wyolum/KlokTHREEjr/images/IMG_20180121_123737154.jpg

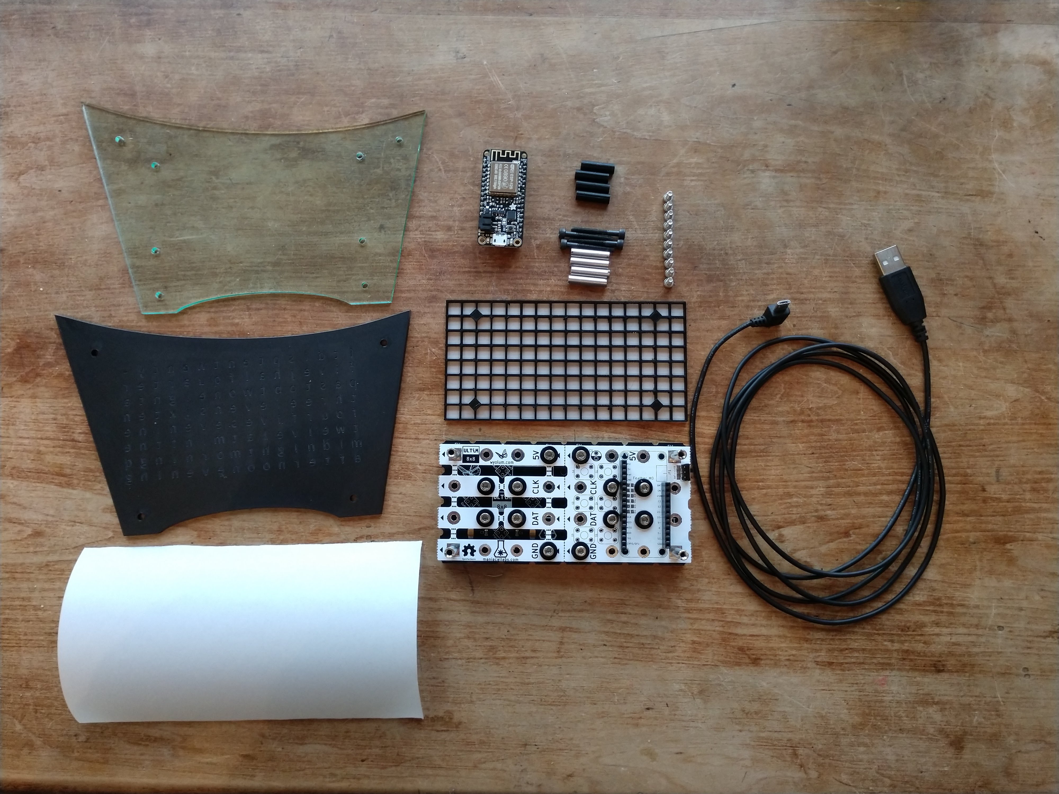
images/IMG_20180121_123737154.jpg
