wyolum/KlokTHREEjr/images/IMG_20180121_124737628.jpg

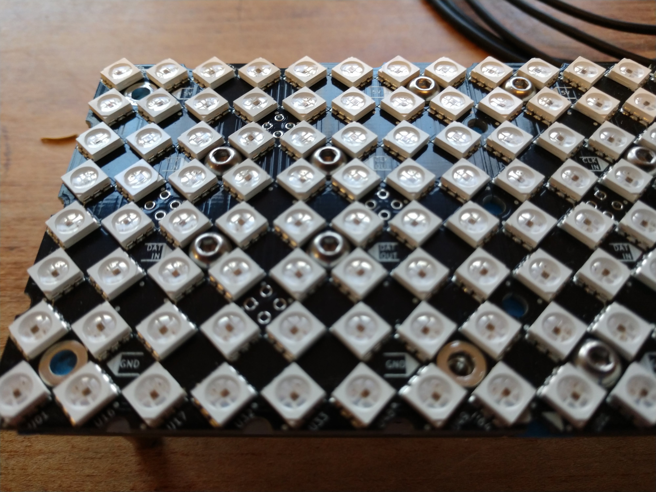
images/IMG_20180121_124737628.jpg
