wyolum/KlokTHREEjr/images/IMG_20180121_130417669.jpg

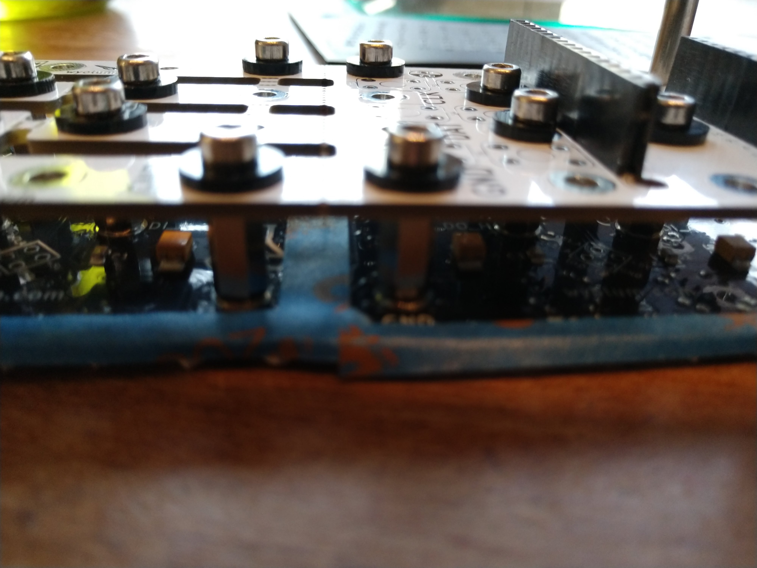
images/IMG_20180121_130417669.jpg
