wyolum/KlokTHREEjr/images/IMG_20180121_130429405.jpg

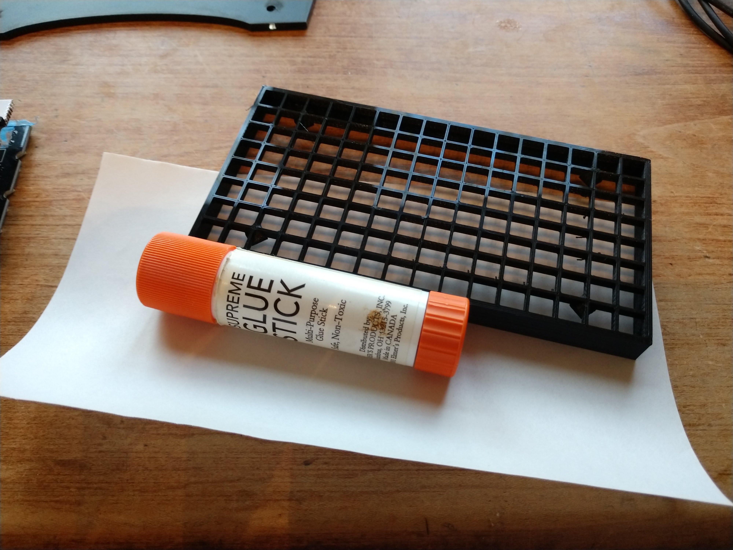
images/IMG_20180121_130429405.jpg
