wyolum/KlokTHREEjr/images/IMG_20180121_130903656.jpg

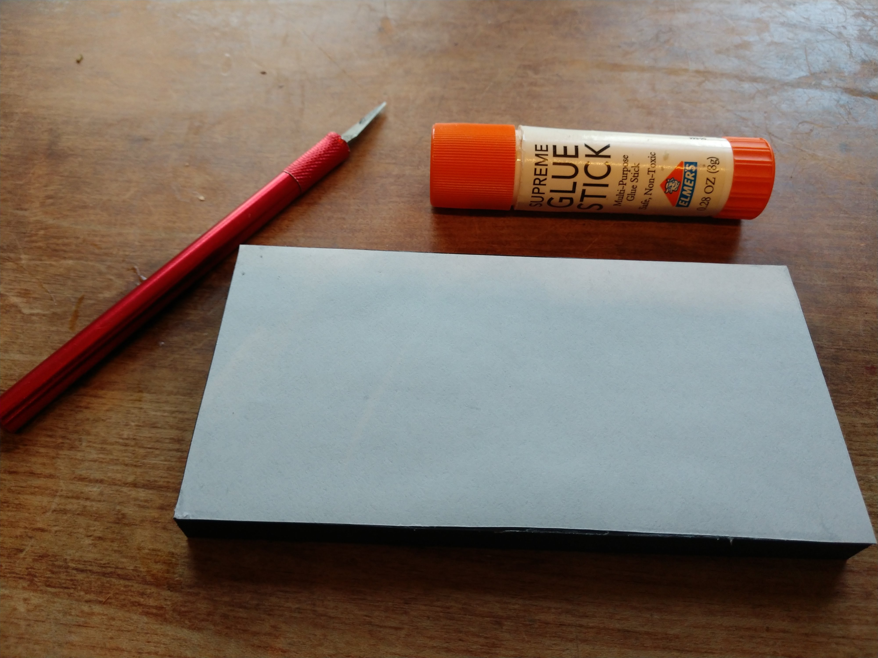
images/IMG_20180121_130903656.jpg
