wyolum/KlokTHREEjr/images/IMG_20180121_130914929.jpg

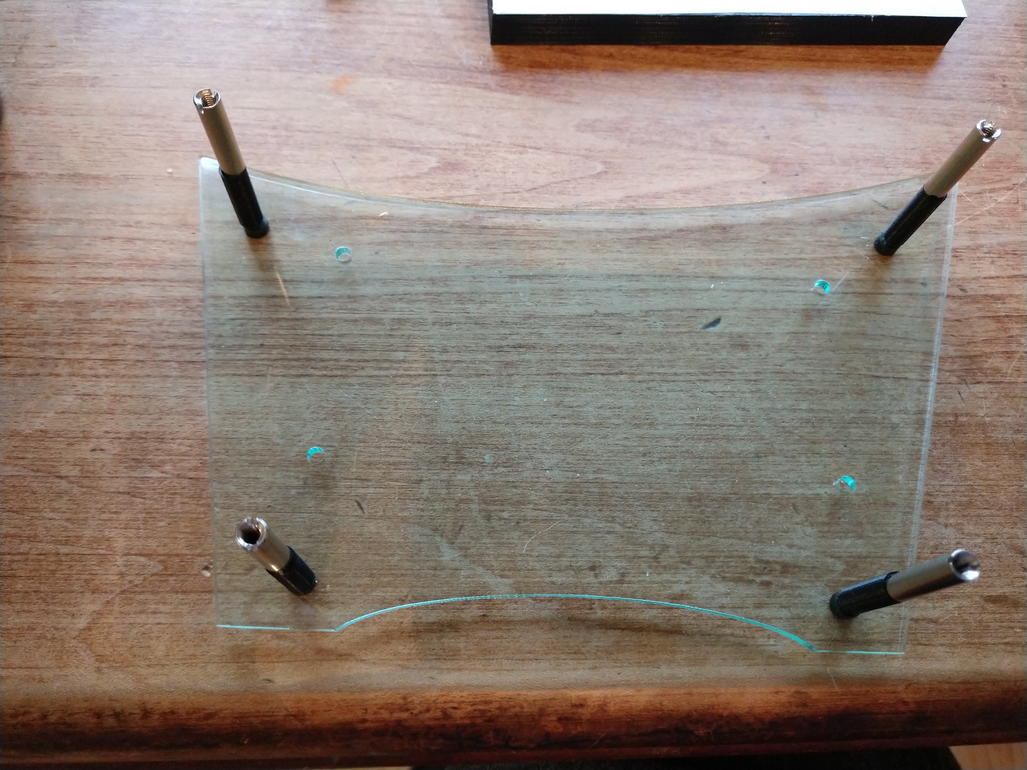
images/IMG_20180121_130914929.jpg
