wyolum/KlokTHREEjr/images/IMG_20180121_131034821.jpg

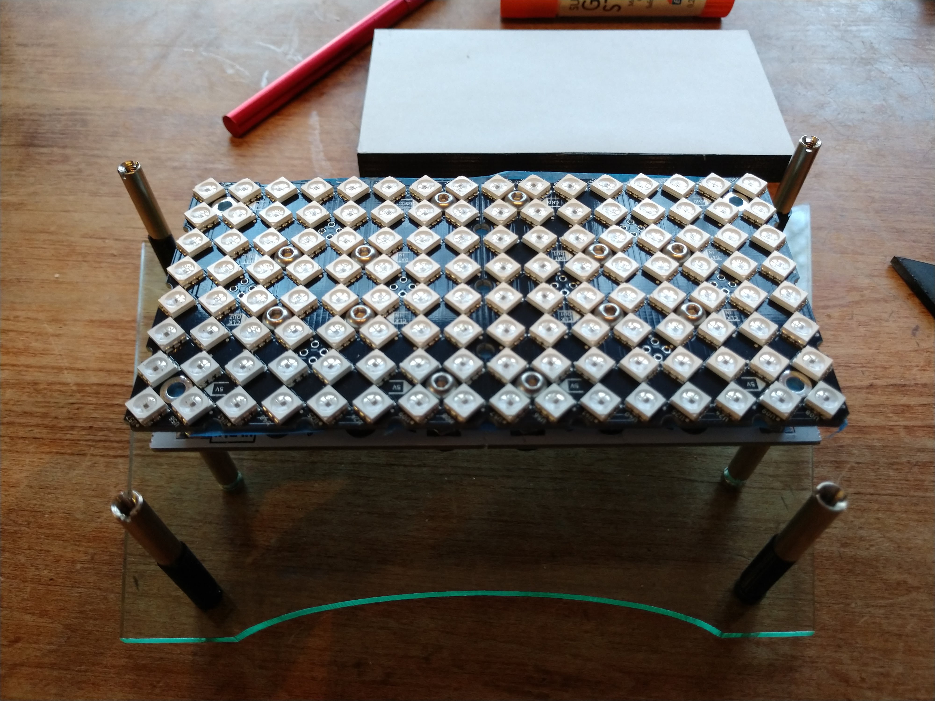
images/IMG_20180121_131034821.jpg
