wyolum/KlokTHREEjr/images/IMG_20180121_131046575.jpg

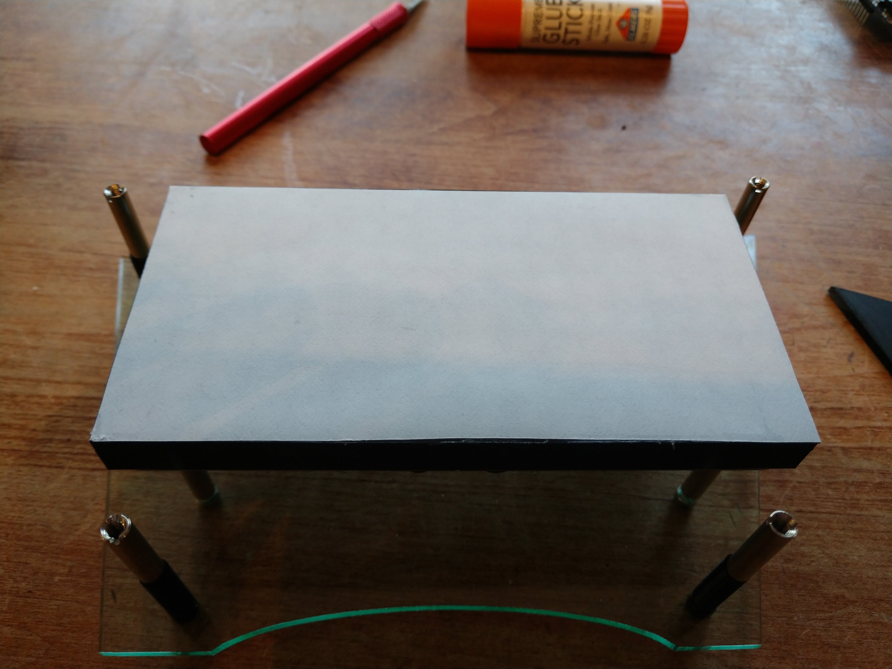
images/IMG_20180121_131046575.jpg
