wyolum/KlokTHREEjr/images/IMG_20180121_131612478.jpg

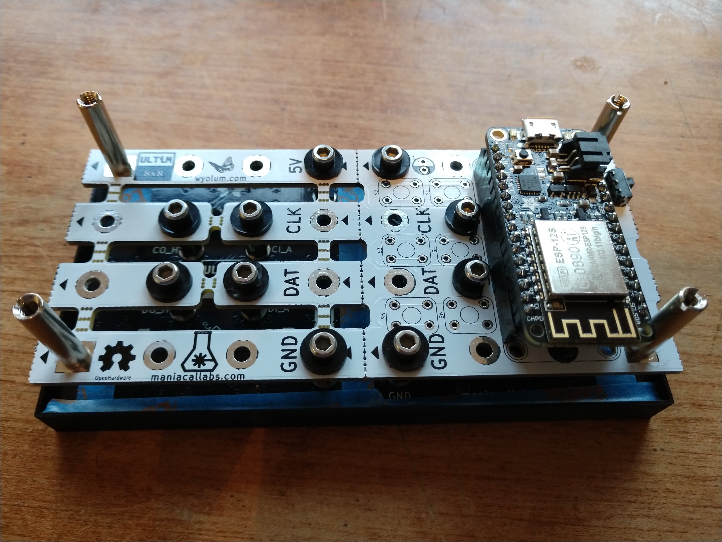
images/IMG_20180121_131612478.jpg
