wyolum/KlokTHREEjr/images/IMG_20180121_131839371.jpg

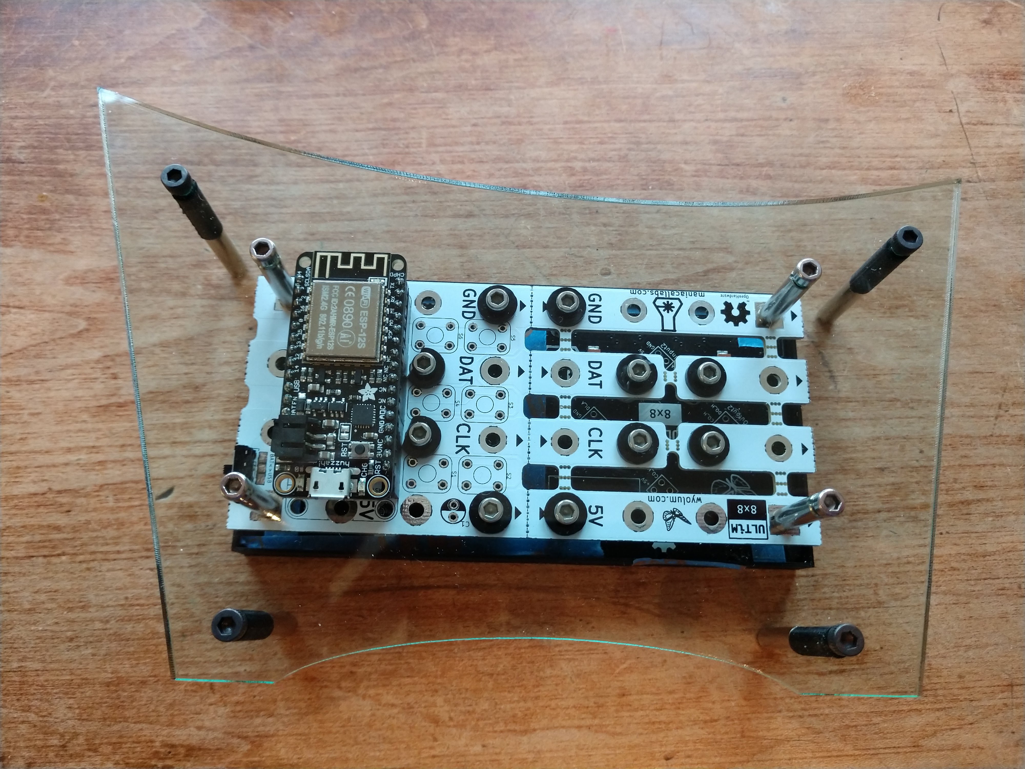
images/IMG_20180121_131839371.jpg
