wyolum/KlokTHREEjr/images/IMG_20180121_131950804.jpg

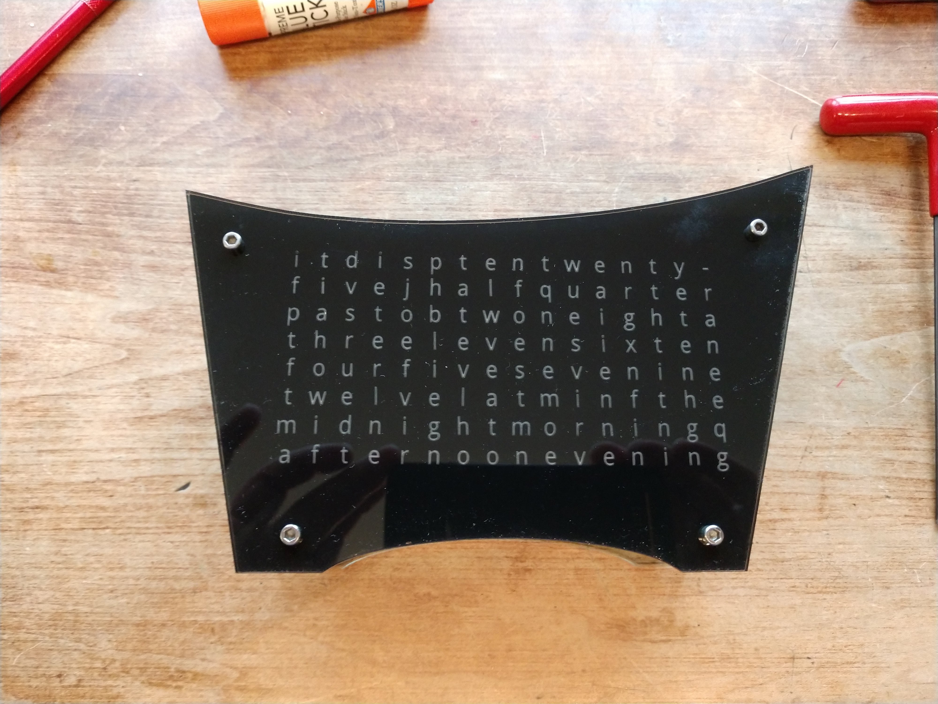
images/IMG_20180121_131950804.jpg
