wyolum/KlokTHREEjr/k3jr_controller_kicad_v2/3d_render/k3jr_controller_01.png

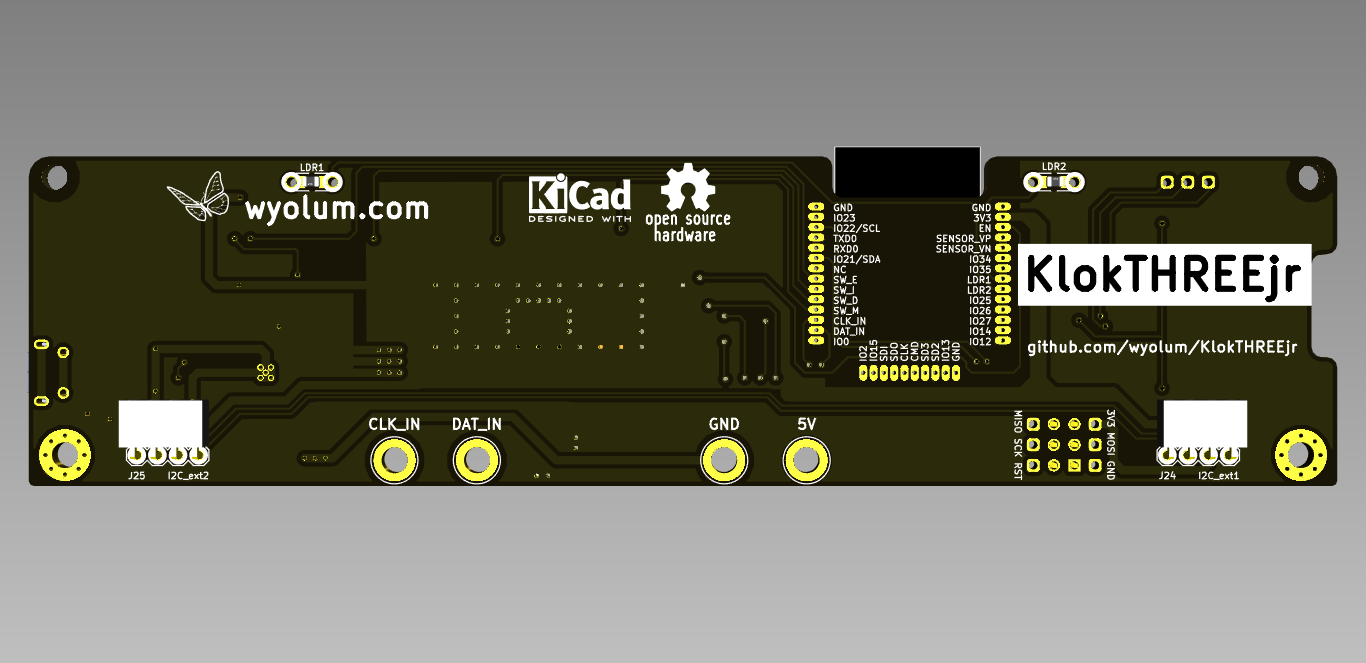
k3jr_controller_kicad_v2/3d_render/k3jr_controller_01.png
