wyolum/KlokTHREEjr/k3jr_controller_kicad_v2/3d_render/k3jr_controller_03.png

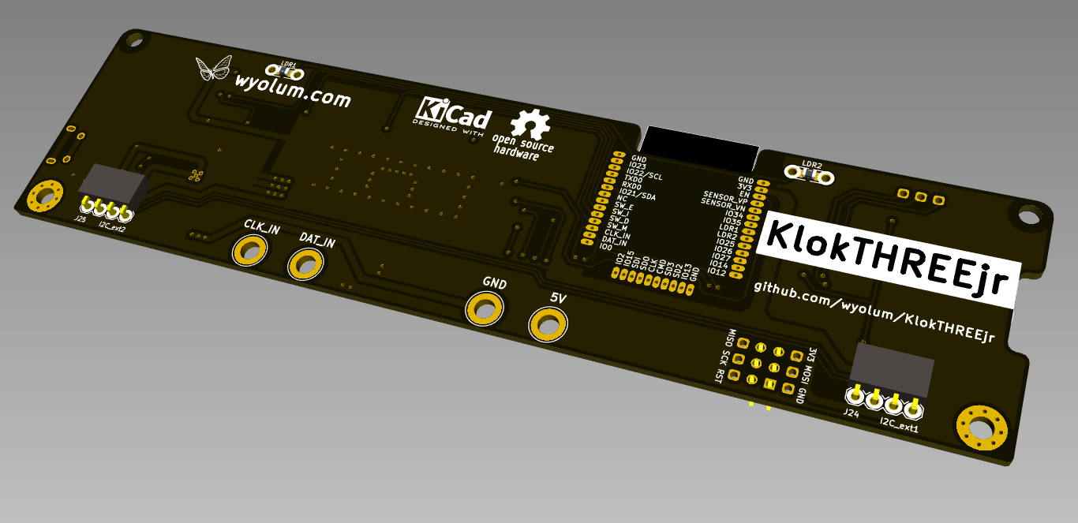
k3jr_controller_kicad_v2/3d_render/k3jr_controller_03.png
