wyolum/KlokTHREEjr/kicad/3d_render/KlokTHREEjr03.png

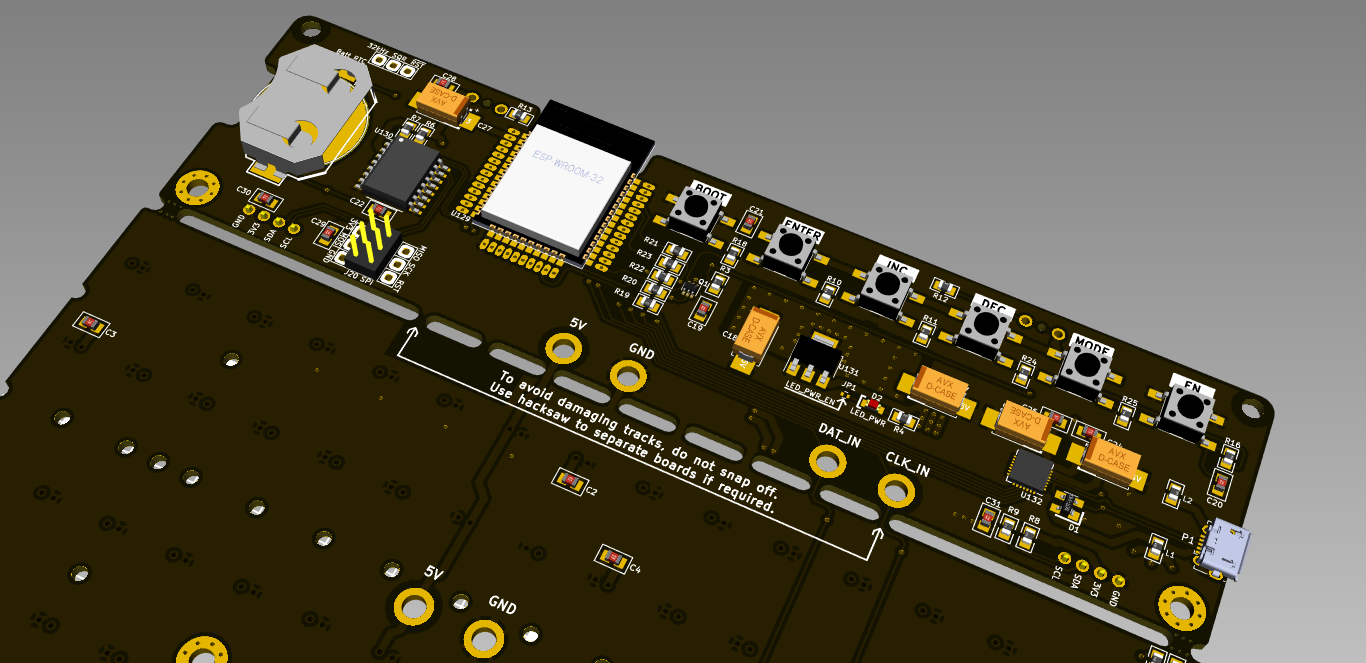
kicad/3d_render/KlokTHREEjr03.png
