wyolum/KlokTHREEjr/kicad/3d_render/KlokTHREEjr04.png

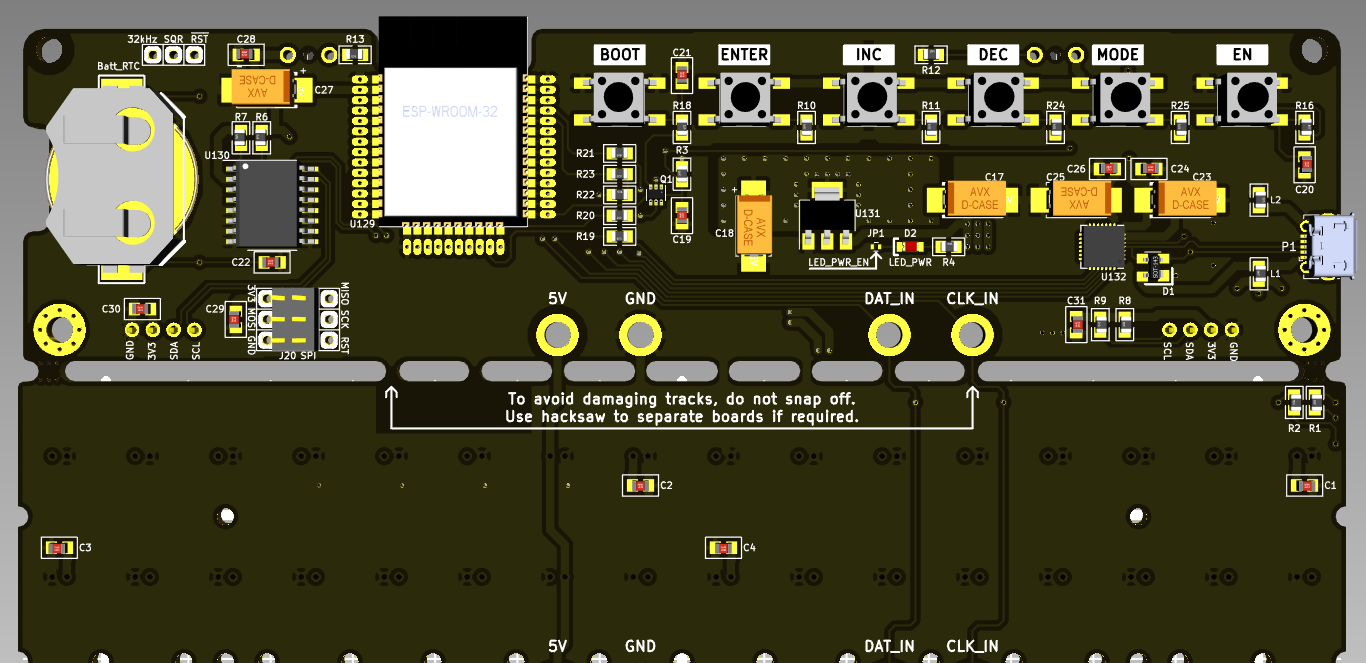
kicad/3d_render/KlokTHREEjr04.png
