wyolum/KlokTHREEjr/kicad/3d_render/KlokTHREEjr05.png

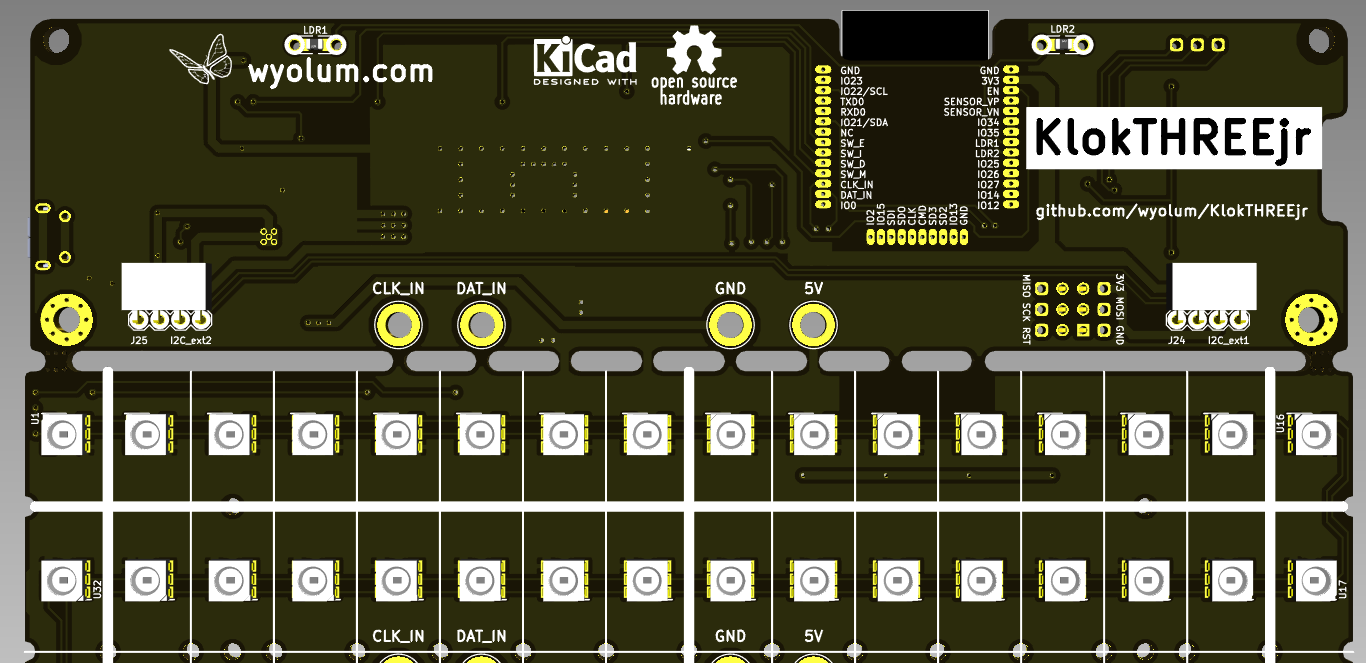
kicad/3d_render/KlokTHREEjr05.png
