wyolum/KlokTHREEjr/kicad/3d_render/KlokTHREEjr06.png

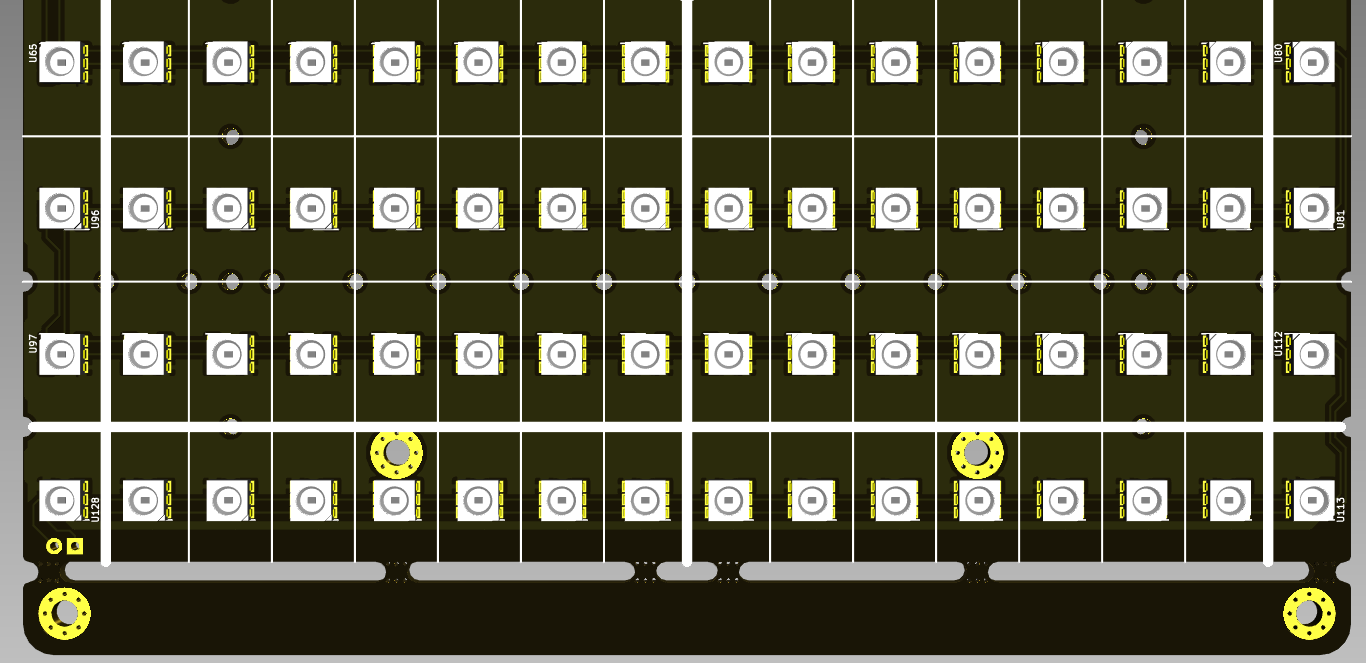
kicad/3d_render/KlokTHREEjr06.png
