wyolum/KlokTHREEjr/k3jr_controller_kicad_v2/3d_modules/QFN28-0_5.step

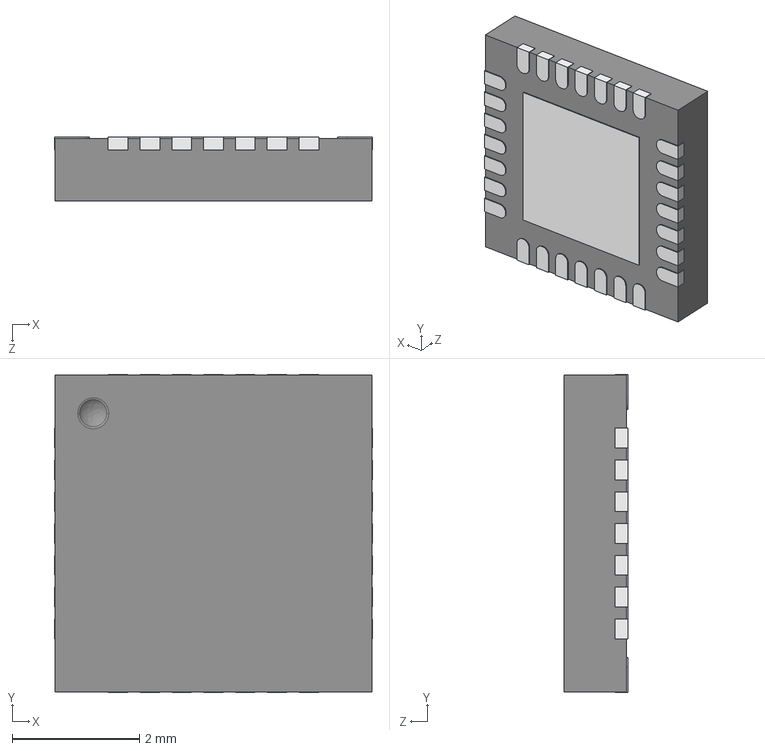
[picture p38: CAD file, 2017-12-30]
k3jr_controller_kicad_v2/3d_modules/QFN28-0_5.step
5.00 x 5.00 x 1.00 mm
User Library-QFN28-0_5_Fusion
User Library-QFN28-0_5_Fillet
