wyolum/KlokTHREEjr/k3jr_controller_kicad_v2/3d_modules/SOT-223.step

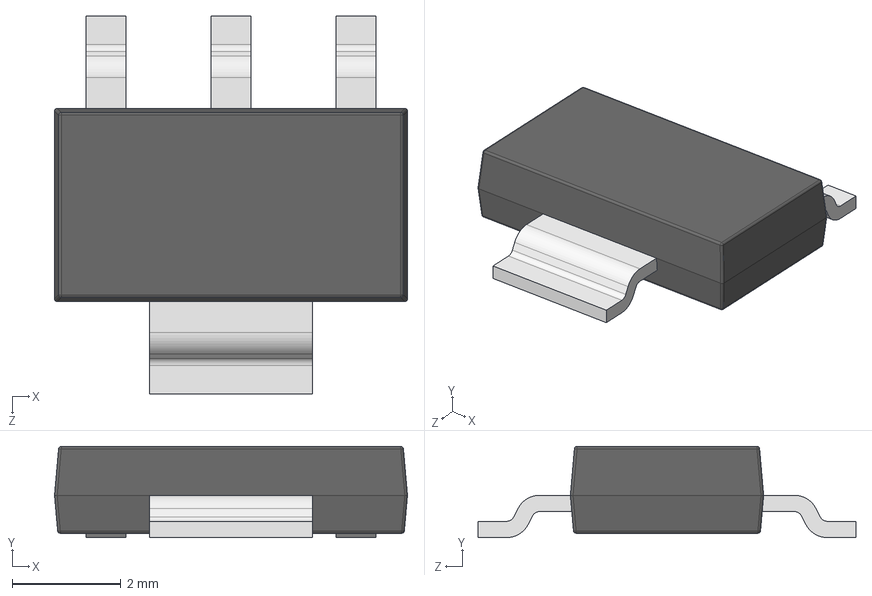
[picture p39: CAD file, 2017-12-30]
k3jr_controller_kicad_v2/3d_modules/SOT-223.step
6.50 x 1.68 x 6.96 mm
