wyolum/KlokTHREEjr/k3jr_controller_kicad_v2/3d_modules/QFN-28.step

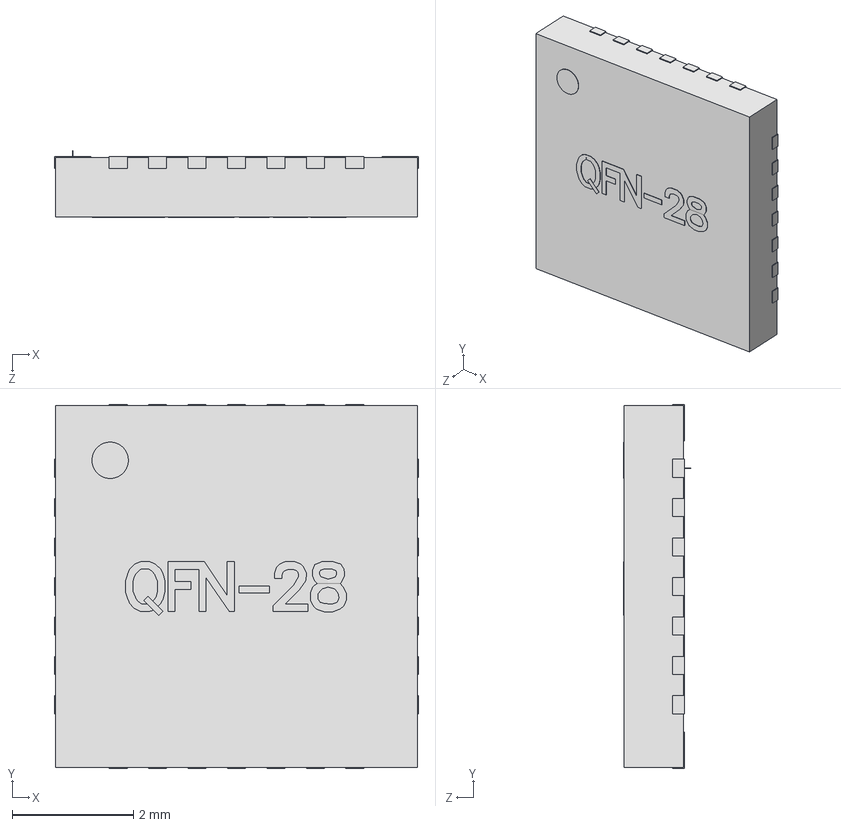
[picture p40: CAD file, 2017-12-30]
k3jr_controller_kicad_v2/3d_modules/QFN-28.step
6.00 x 6.00 x 1.11 mm
SW3dPS-QFN-28_Board1
SW3dPS-QFN-28_Extruded22 x 7
SW3dPS-QFN-28_Cylinder1
SW3dPS-QFN-28_Extruded25 x 7
SW3dPS-QFN-28_Extruded20
SW3dPS-QFN-28_Extruded14 x 7
SW3dPS-QFN-28_Extruded24
SW3dPS-QFN-28_Extruded16
SW3dPS-QFN-28_Extruded19
SW3dPS-QFN-28_Extruded17
SW3dPS-QFN-28_Extruded21 x 7
SW3dPS-QFN-28_Extruded23
SW3dPS-QFN-28_Extruded13
SW3dPS-QFN-28_Extruded18
SW3dPS-QFN-28_Extruded15
