wyolum/KlokTHREEjr/k3jr_controller_kicad_v2/3d_modules/led_0805.step

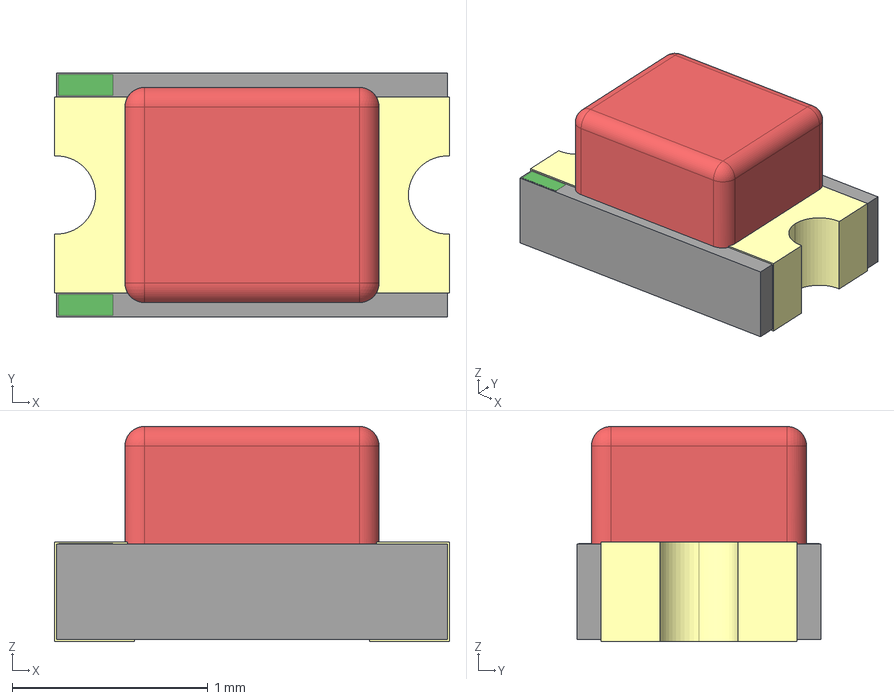
[picture p41: CAD file, 2017-12-30]
k3jr_controller_kicad_v2/3d_modules/led_0805.step
2.02 x 1.25 x 1.10 mm
