wyolum/KlokTHREEjr/k3jr_controller_kicad_v2/3d_modules/SOT-363.step

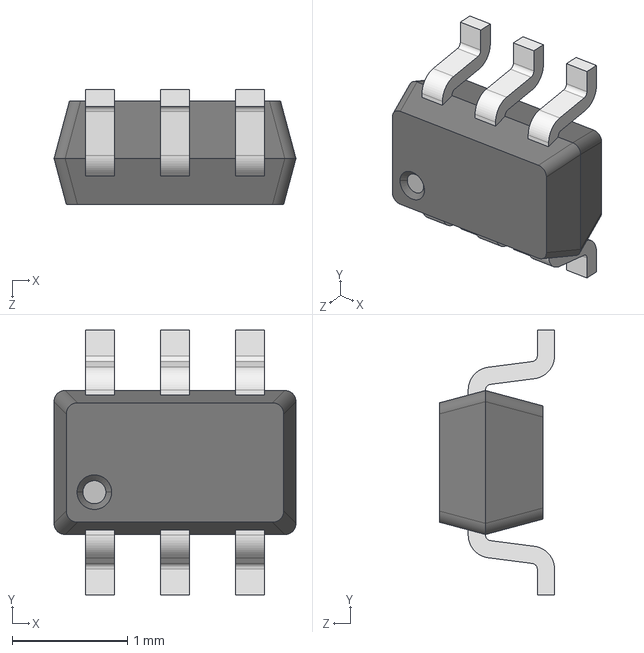
[picture p42: CAD file, 2017-12-30]
k3jr_controller_kicad_v2/3d_modules/SOT-363.step
2.10 x 2.30 x 1.00 mm
