wyolum/KlokTHREEjr/k3jr_controller_kicad_v2/3d_modules/QFN_28_1EP_5x5mm.step

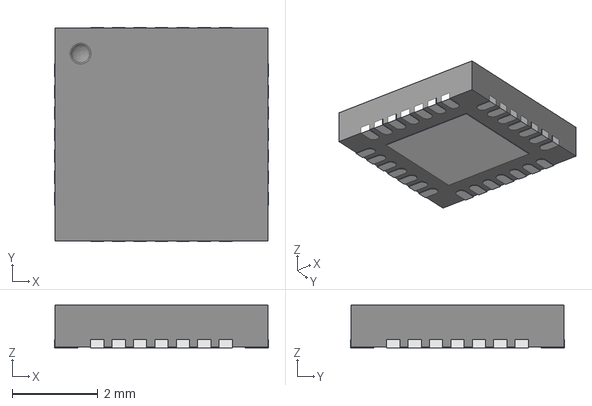
[picture p43: CAD file, 2017-12-30]
k3jr_controller_kicad_v2/3d_modules/QFN_28_1EP_5x5mm.step
5.00 x 5.00 x 1.00 mm
