wyolum/KlokTHREEjr/k3jr_controller_kicad_v2/3d_modules/MicroUSB-B_Molex_105017-0001.step

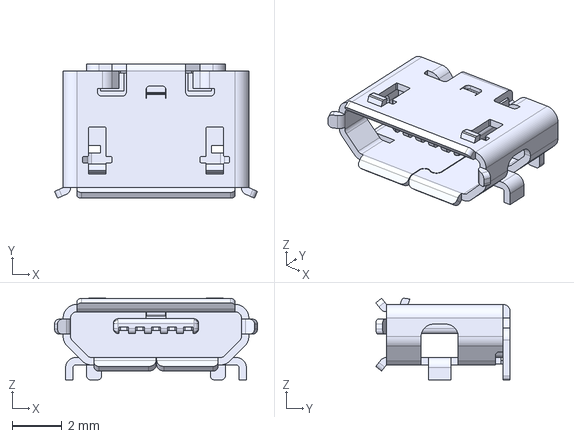
[picture p44: CAD file, 2017-12-30]
k3jr_controller_kicad_v2/3d_modules/MicroUSB-B_Molex_105017-0001.step
8.20 x 5.43 x 3.30 mm
