wyolum/KlokTHREEjr/k3jr_controller_kicad_v2/3d_modules/SOIC16_Wide.step

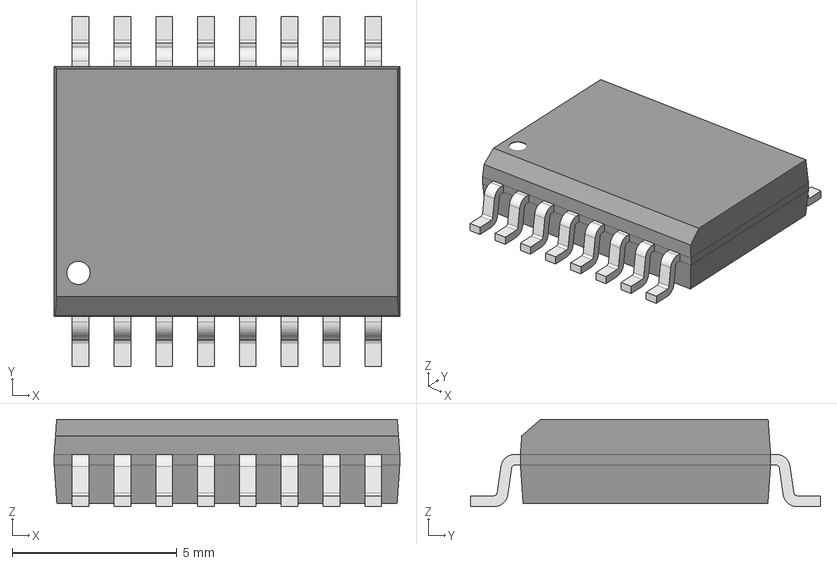
[picture p45: CAD file, 2017-12-27]
k3jr_controller_kicad_v2/3d_modules/SOIC16_Wide.step
10.5 x 10.6 x 2.65 mm
