wyolum/KlokTHREEjr/k3jr_controller_kicad_v2/3d_modules/cap_2917_7343M.step

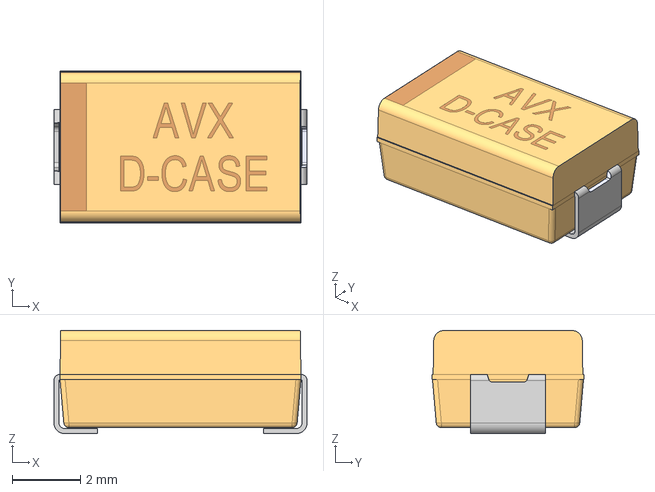
[picture p46: CAD file, 2017-12-27]
k3jr_controller_kicad_v2/3d_modules/cap_2917_7343M.step
7.40 x 4.45 x 3.01 mm
