wyolum/KlokTHREEjr/k3jr_controller_kicad_v2/3d_modules/cap_0805_2012M.step

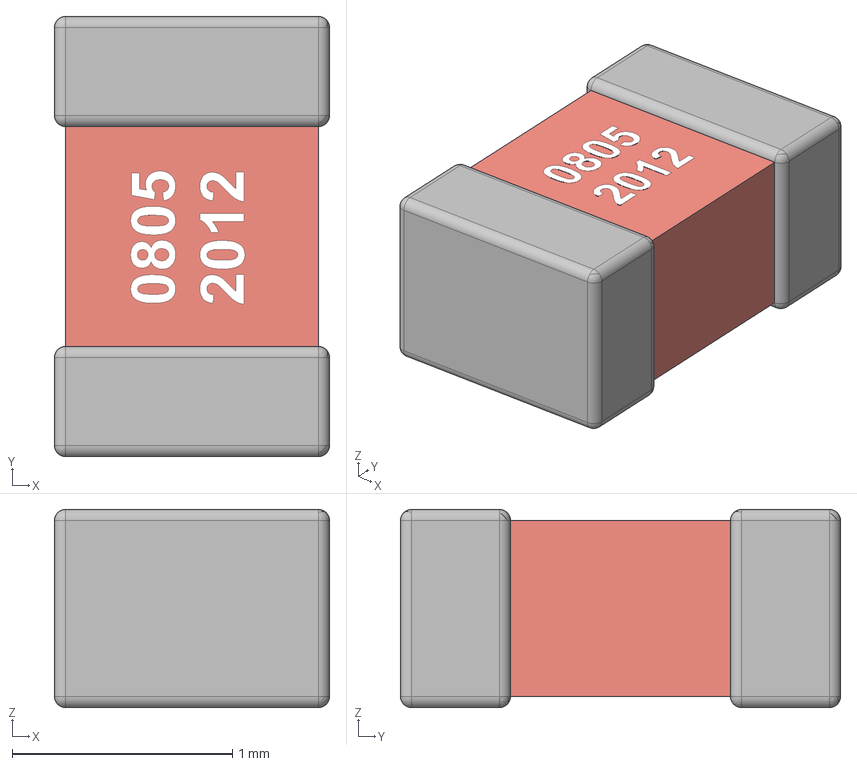
[picture p47: CAD file, 2017-12-27]
k3jr_controller_kicad_v2/3d_modules/cap_0805_2012M.step
1.25 x 2.00 x 0.9 mm
