wyolum/KlokTHREEjr/k3jr_controller_kicad_v2/3d_modules/esp-wroom-32.step

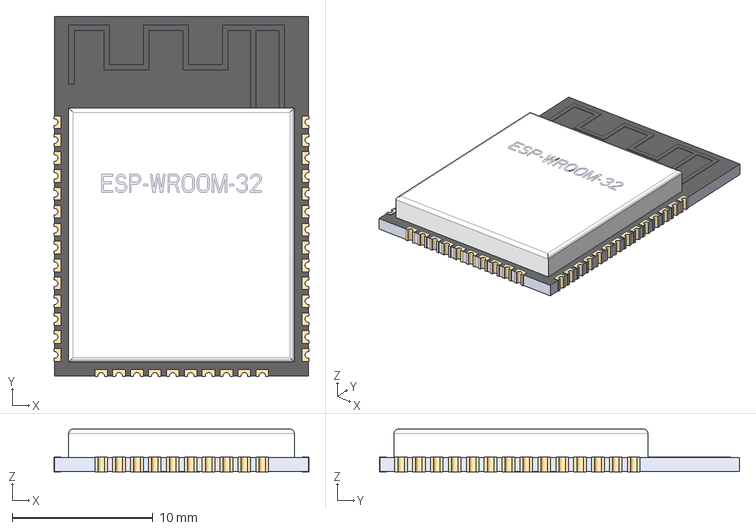
[picture p48: CAD file, 2017-12-27]
k3jr_controller_kicad_v2/3d_modules/esp-wroom-32.step
18.1 x 25.5 x 3.04 mm
