wyolum/KlokTHREEjr/k3jr_controller_kicad_v2/3d_modules/do214aa.step

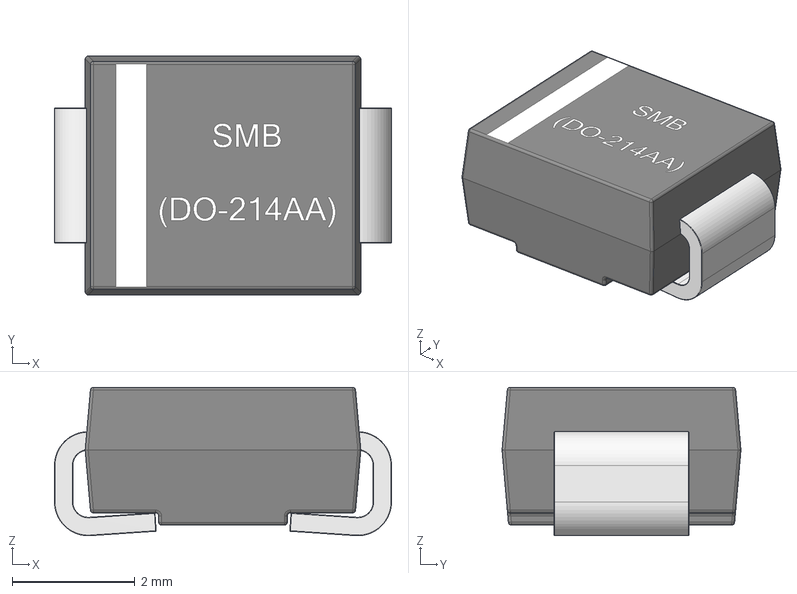
[picture p49: CAD file, 2017-12-27]
k3jr_controller_kicad_v2/3d_modules/do214aa.step
5.50 x 3.90 x 2.42 mm
