wyolum/KlokTHREEjr/k3jr_controller_kicad_v2/3d_modules/fuse_1812_4532M.step

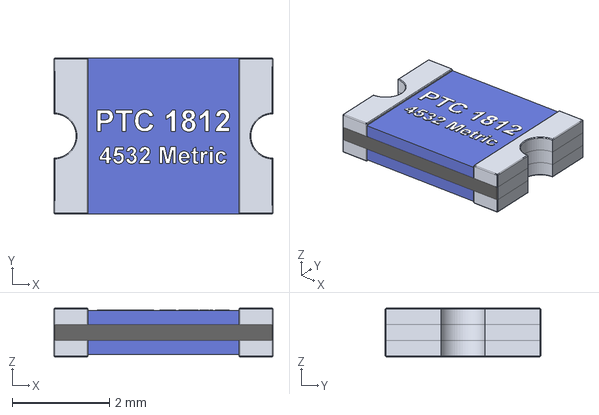
[picture p50: CAD file, 2017-12-27]
k3jr_controller_kicad_v2/3d_modules/fuse_1812_4532M.step
4.50 x 3.20 x 1.00 mm
