wyolum/KlokTHREEjr/k3jr_controller_kicad_v2/3d_modules/r_0805.step

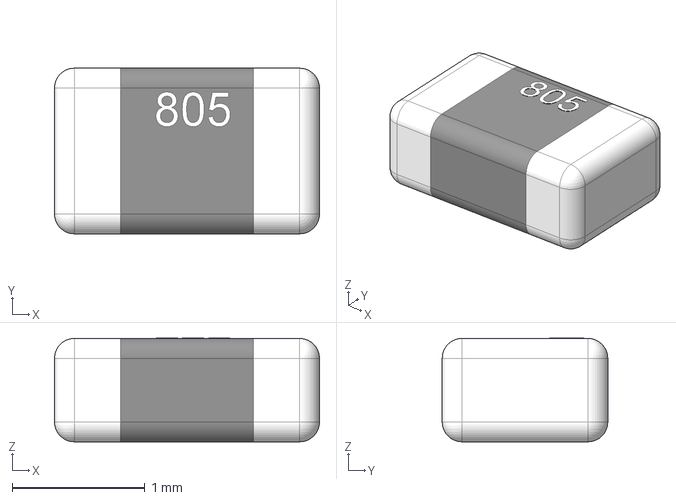
[picture p51: CAD file, 2017-12-27]
k3jr_controller_kicad_v2/3d_modules/r_0805.step
2.00 x 1.25 x 0.782 mm
