wyolum/KlokTHREEjr/k3jr_controller_kicad_v2/3d_modules/sw_pb_smd.step

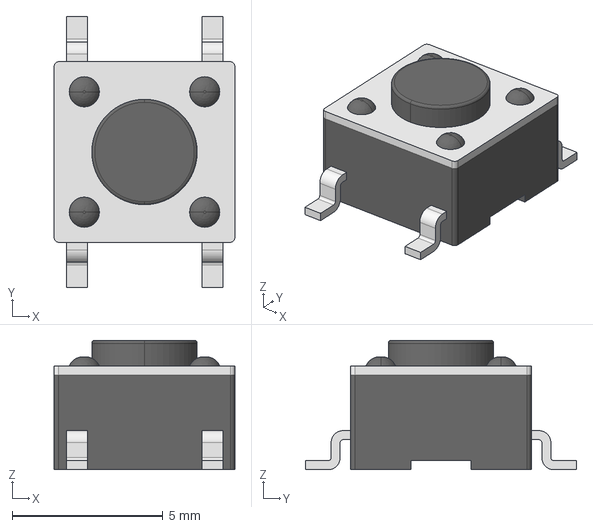
[picture p52: CAD file, 2017-12-27]
k3jr_controller_kicad_v2/3d_modules/sw_pb_smd.step
6.00 x 9.00 x 4.30 mm
