wyolum/KlokTHREEjr/k3jr_controller_kicad_v2/3d_modules/LED_SMD_APA102.step

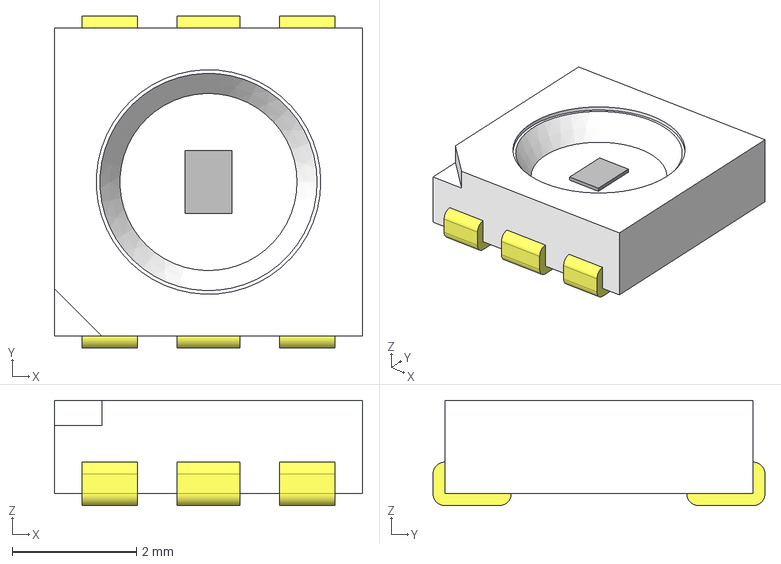
[picture p53: CAD file, 2017-12-27]
k3jr_controller_kicad_v2/3d_modules/LED_SMD_APA102.step
4.95 x 5.33 x 1.69 mm
