wyolum/KlokTHREEjr/k3jr_controller_kicad_v2/3d_modules/cap_1210_3225M.step

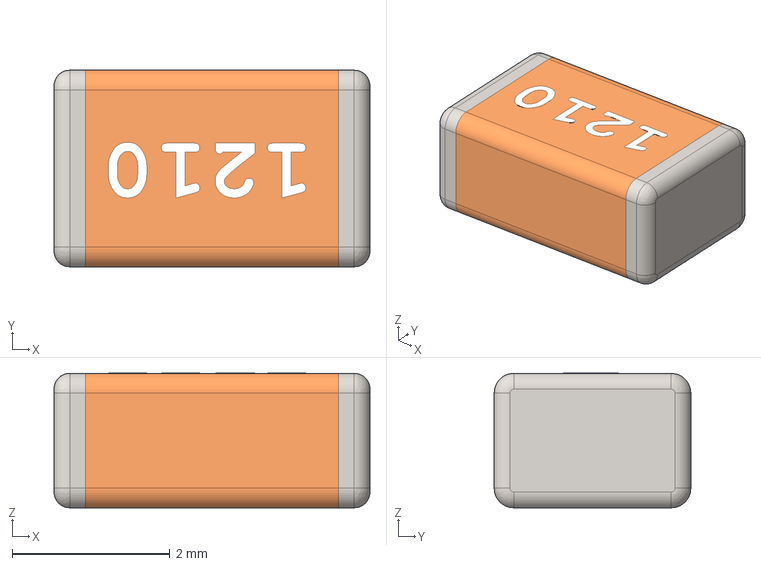
[picture p54: CAD file, 2017-12-27]
k3jr_controller_kicad_v2/3d_modules/cap_1210_3225M.step
4.00 x 2.49 x 1.70 mm
