wyolum/KlokTHREEjr/k3jr_controller_kicad_v2/3d_modules/socket_ra_2pin.step

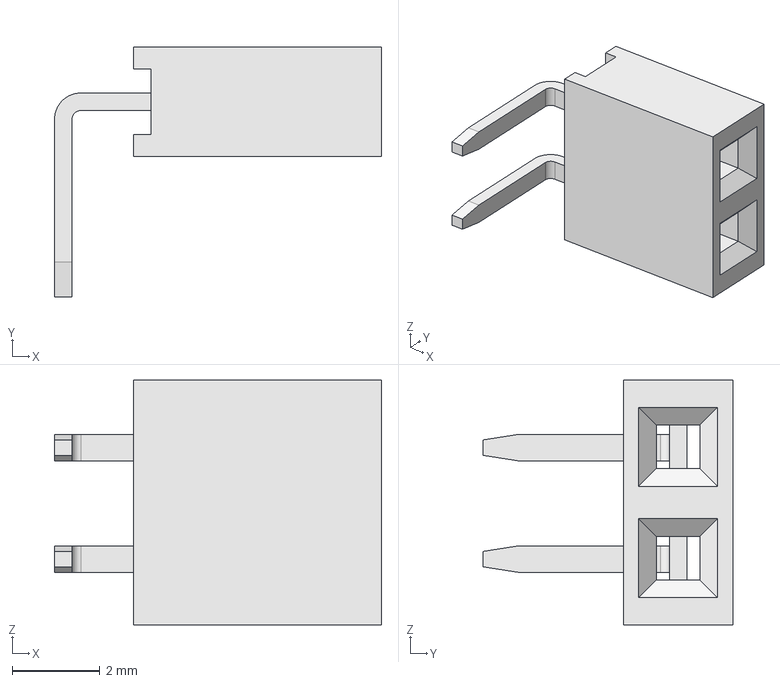
[picture p55: CAD file, 2017-12-27]
k3jr_controller_kicad_v2/3d_modules/socket_ra_2pin.step
7.45 x 5.70 x 5.58 mm
