wyolum/KlokTHREEjr/k3jr_controller_kicad_v2/3d_modules/header_Male_RA_Low_3Pin.step

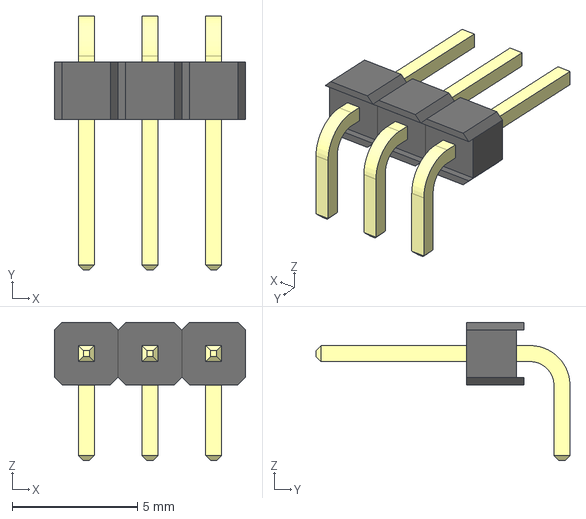
[picture p56: CAD file, 2017-12-27]
k3jr_controller_kicad_v2/3d_modules/header_Male_RA_Low_3Pin.step
7.62 x 10.1 x 5.52 mm
