wyolum/KlokTHREEjr/k3jr_controller_kicad_v2/3d_modules/header_1x3_TH_2_54mm.step

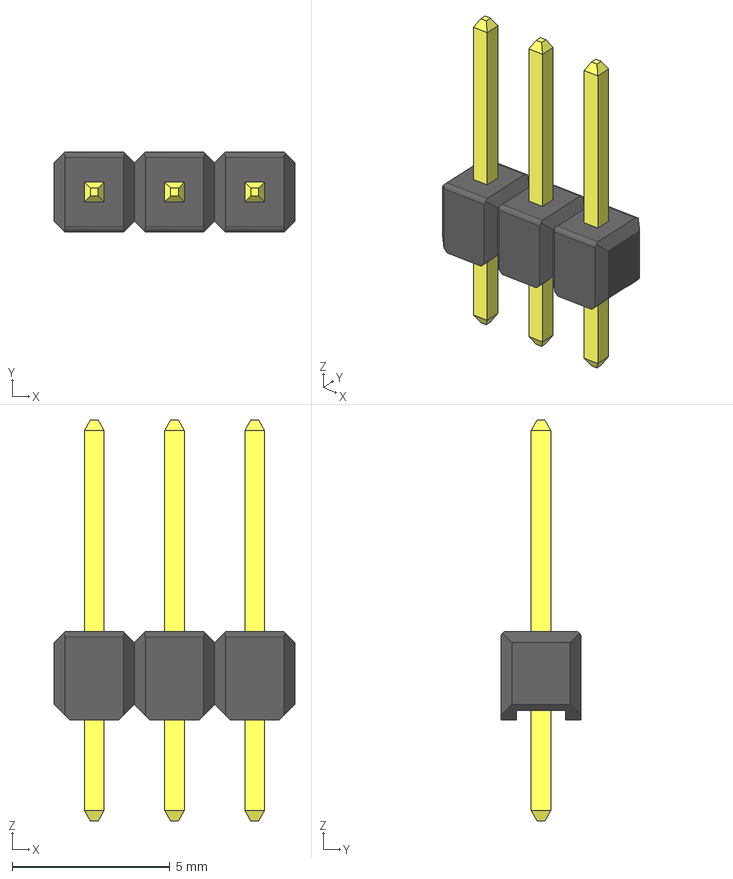
[picture p57: CAD file, 2017-12-27]
k3jr_controller_kicad_v2/3d_modules/header_1x3_TH_2_54mm.step
7.62 x 2.54 x 12.7 mm
