wyolum/KlokTHREEjr/k3jr_controller_kicad_v2/3d_modules/socket_ra_4pin.step

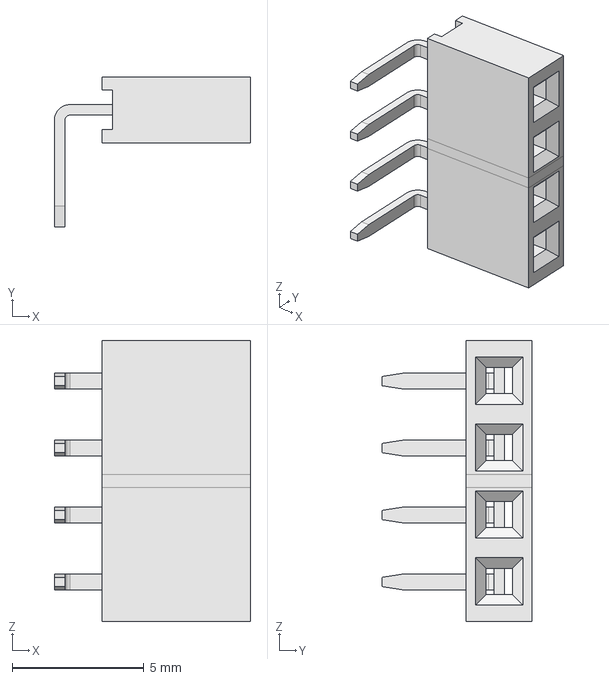
[picture p58: CAD file, 2017-12-27]
k3jr_controller_kicad_v2/3d_modules/socket_ra_4pin.step
7.45 x 5.70 x 10.7 mm
