wyolum/KlokTHREEjr/k3jr_controller_kicad_v2/k3jr_controller_pdf/k3jr_controller-B.SilkS.pdf

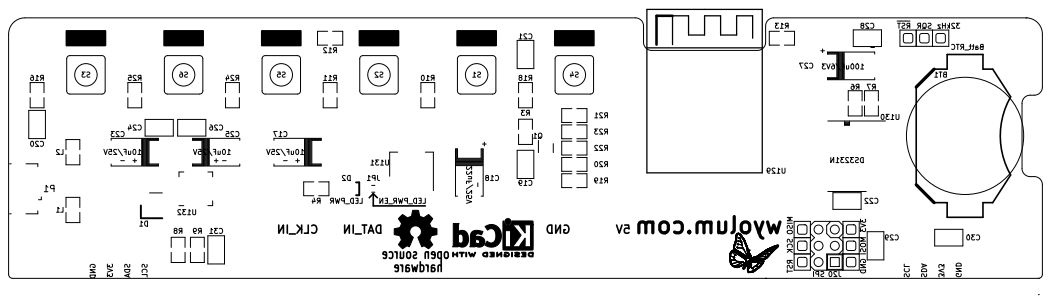
[picture p66: page 1]

https://github.com/wyolum/KlokTHREEjr
File: k3jr_controller.kicad_pcb Sheet: www.wyolum.com
