wyolum/KlokTHREEjr/k3jr_controller_kicad_v2/k3jr_controller_pdf/k3jr_controller-Dwgs.User.pdf

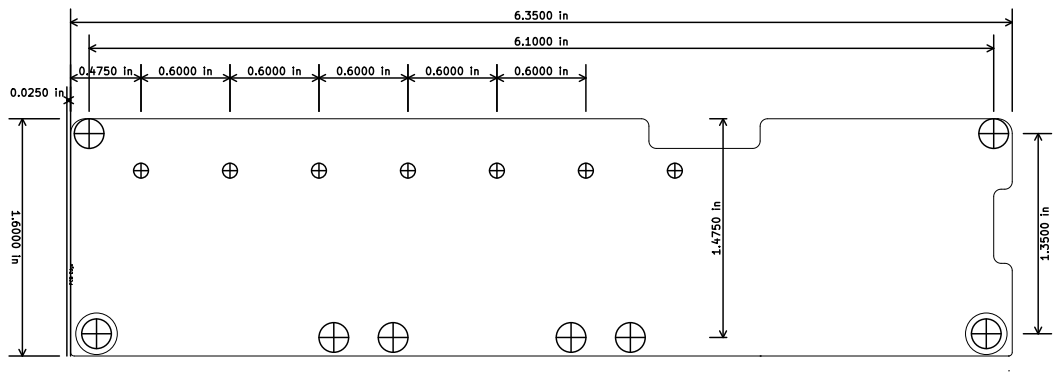
[picture p67: page 1]

https://github.com/wyolum/KlokTHREEjr 1.4750 in

File: k3jr_controller.kicad_pcb Sheet: www.wyolum.com
