wyolum/KlokTHREEjr/kicad/KlokTHREEjr_pdf/KlokTHREEjr-B.SilkS.pdf

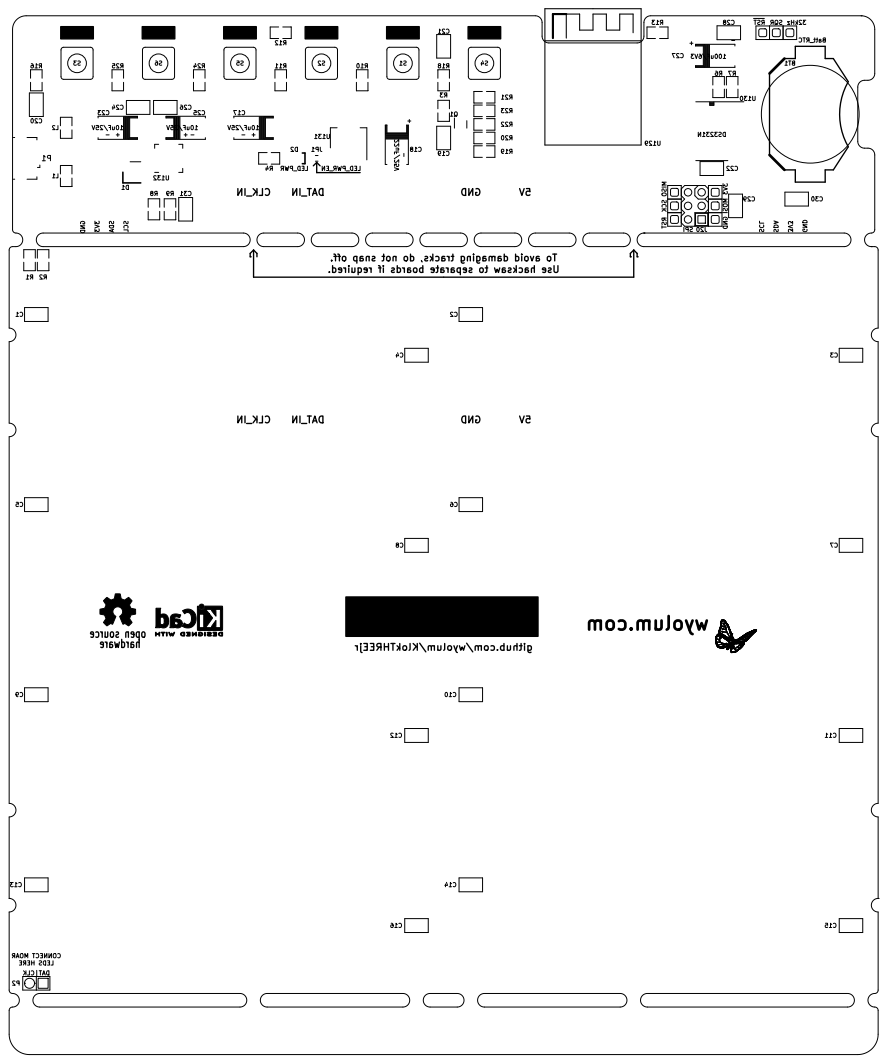
[picture p75: page 1]

https://github.com/wyolum/KlokTHREEjr
File: KlokTHREEjr.kicad_pcb Sheet: www.wyolum.com
