wyolum/KlokTHREEjr/kicad/KlokTHREEjr_pdf/KlokTHREEjr-Dwgs.User.pdf

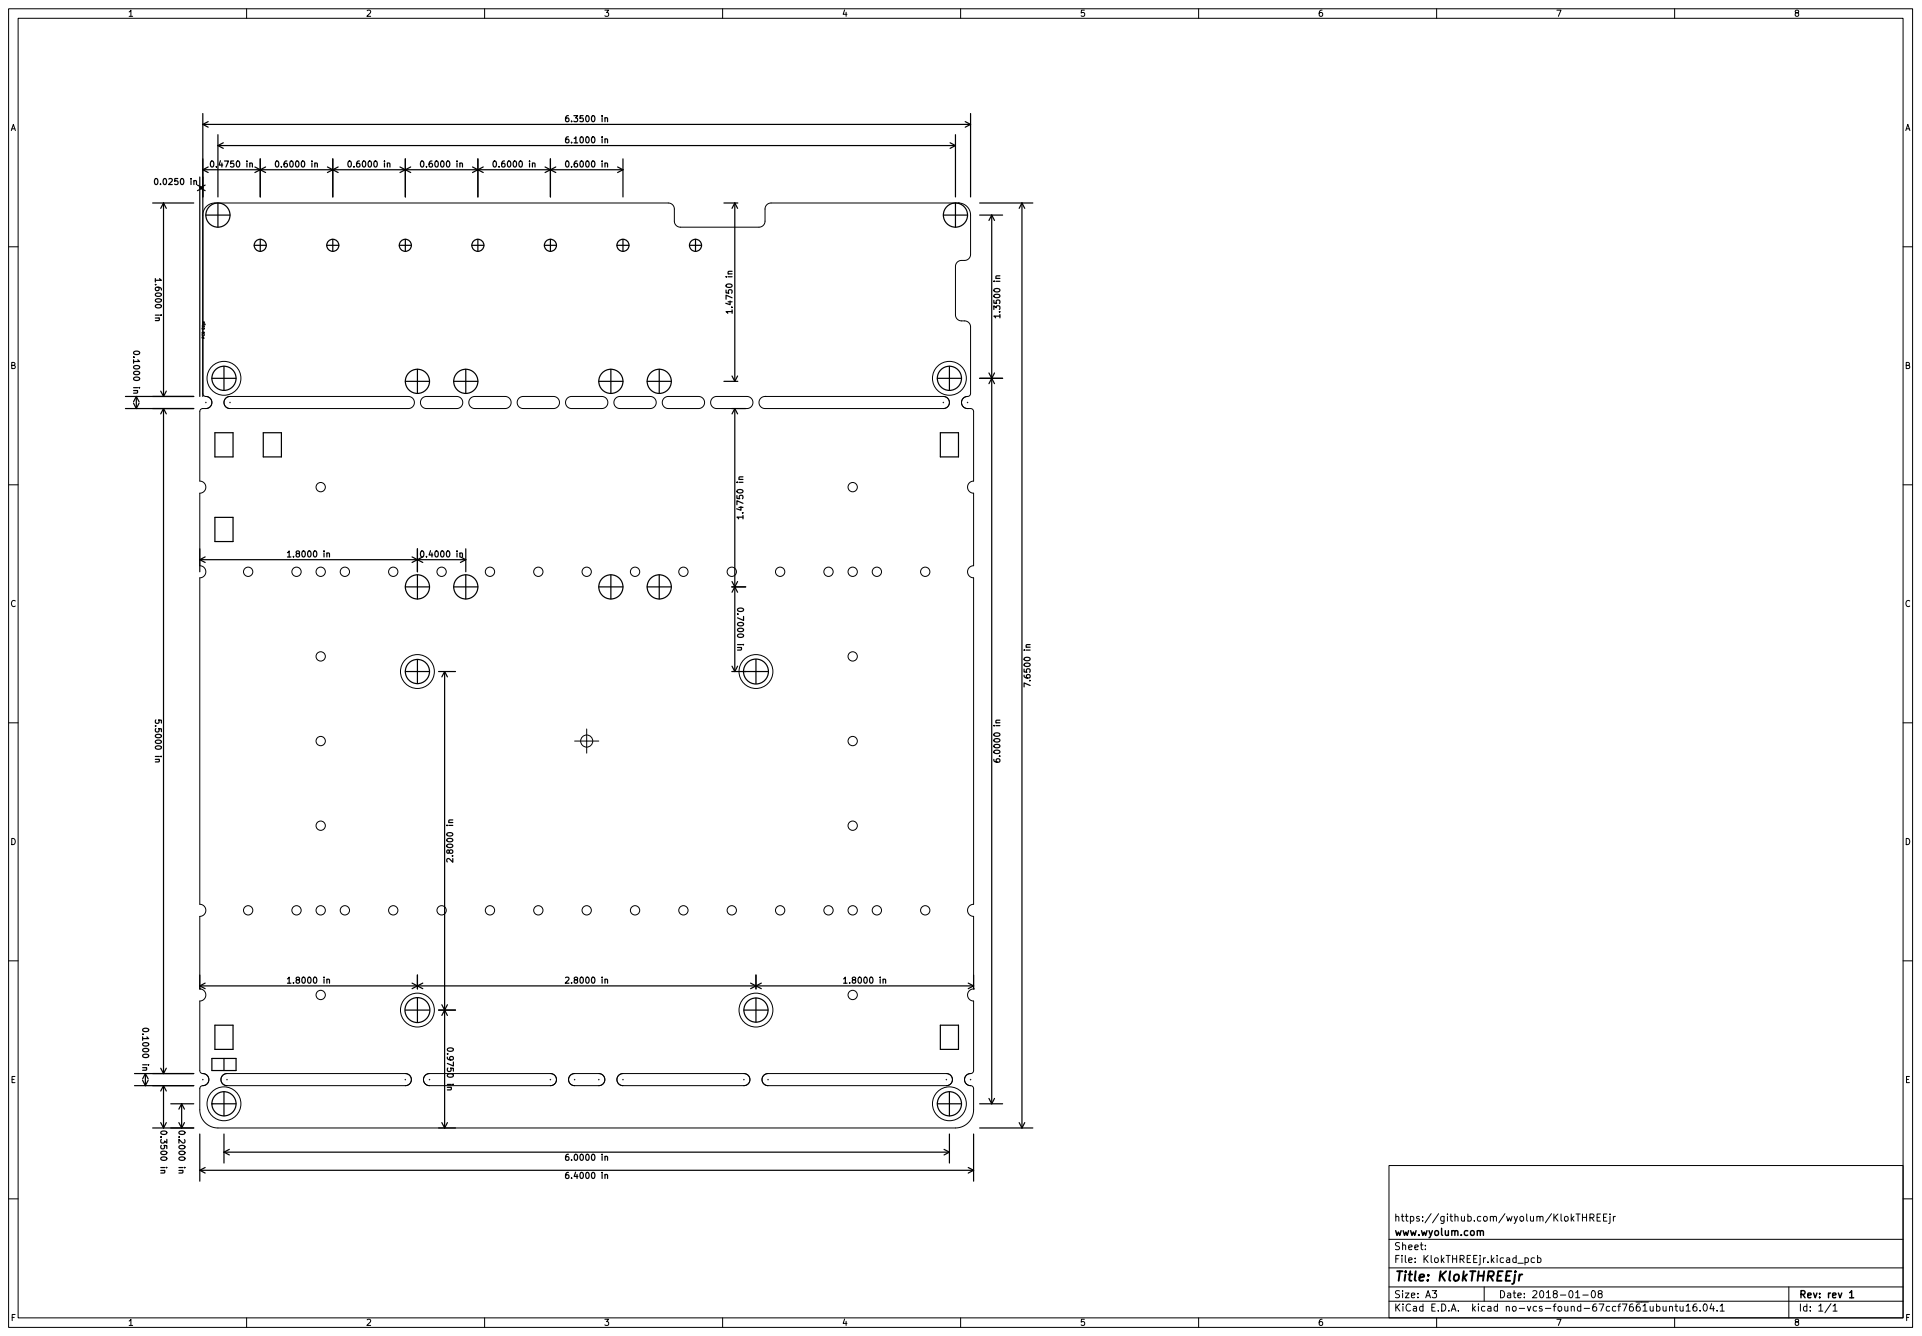
[picture p76: page 1]

https://github.com/wyolum/KlokTHREEjr 0.7000 in

File: KlokTHREEjr.kicad_pcb Sheet: www.wyolum.com
