wyolum/KlokTHREEjr/kicad/KlokTHREEjr_pdf/KlokTHREEjr-F.SilkS.pdf

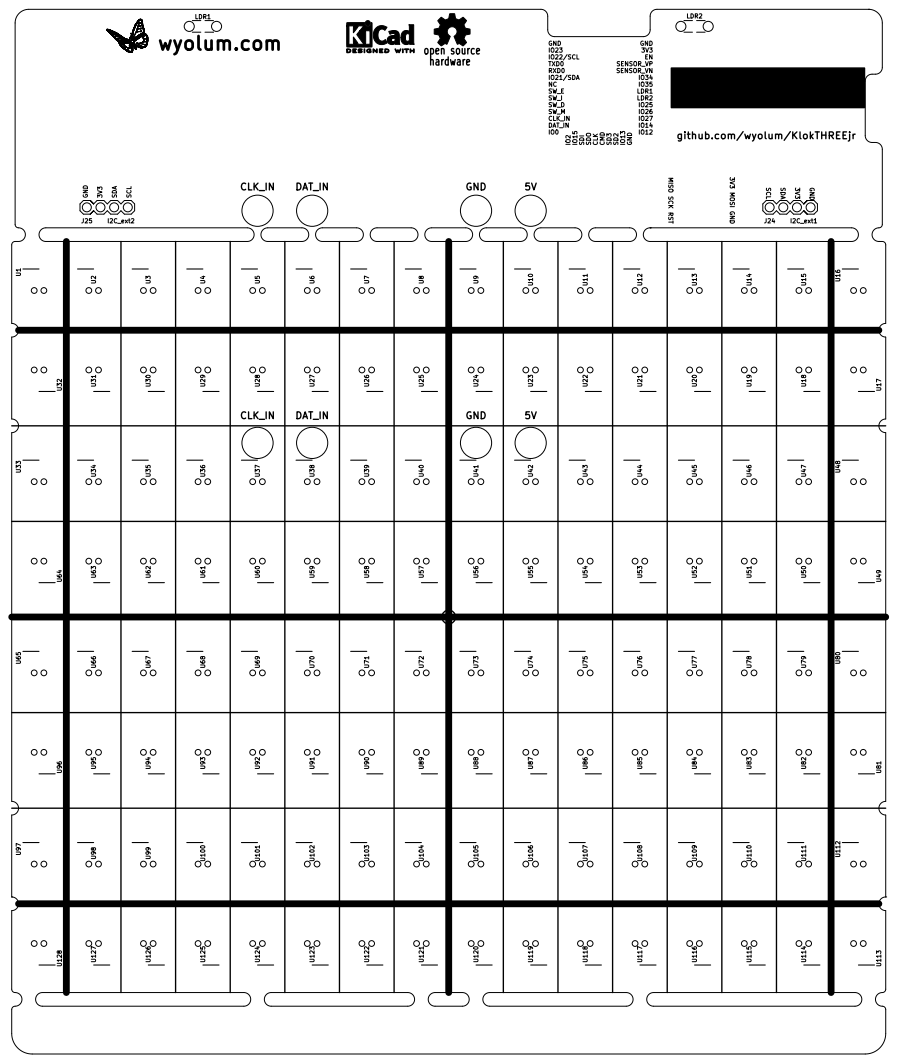
[picture p78: page 1]

https://github.com/wyolum/KlokTHREEjr
File: KlokTHREEjr.kicad_pcb Sheet: www.wyolum.com
