wyolum/KlokTHREEjr/kicad/KlokTHREEjr_pdf/KlokTHREEjr.pdf

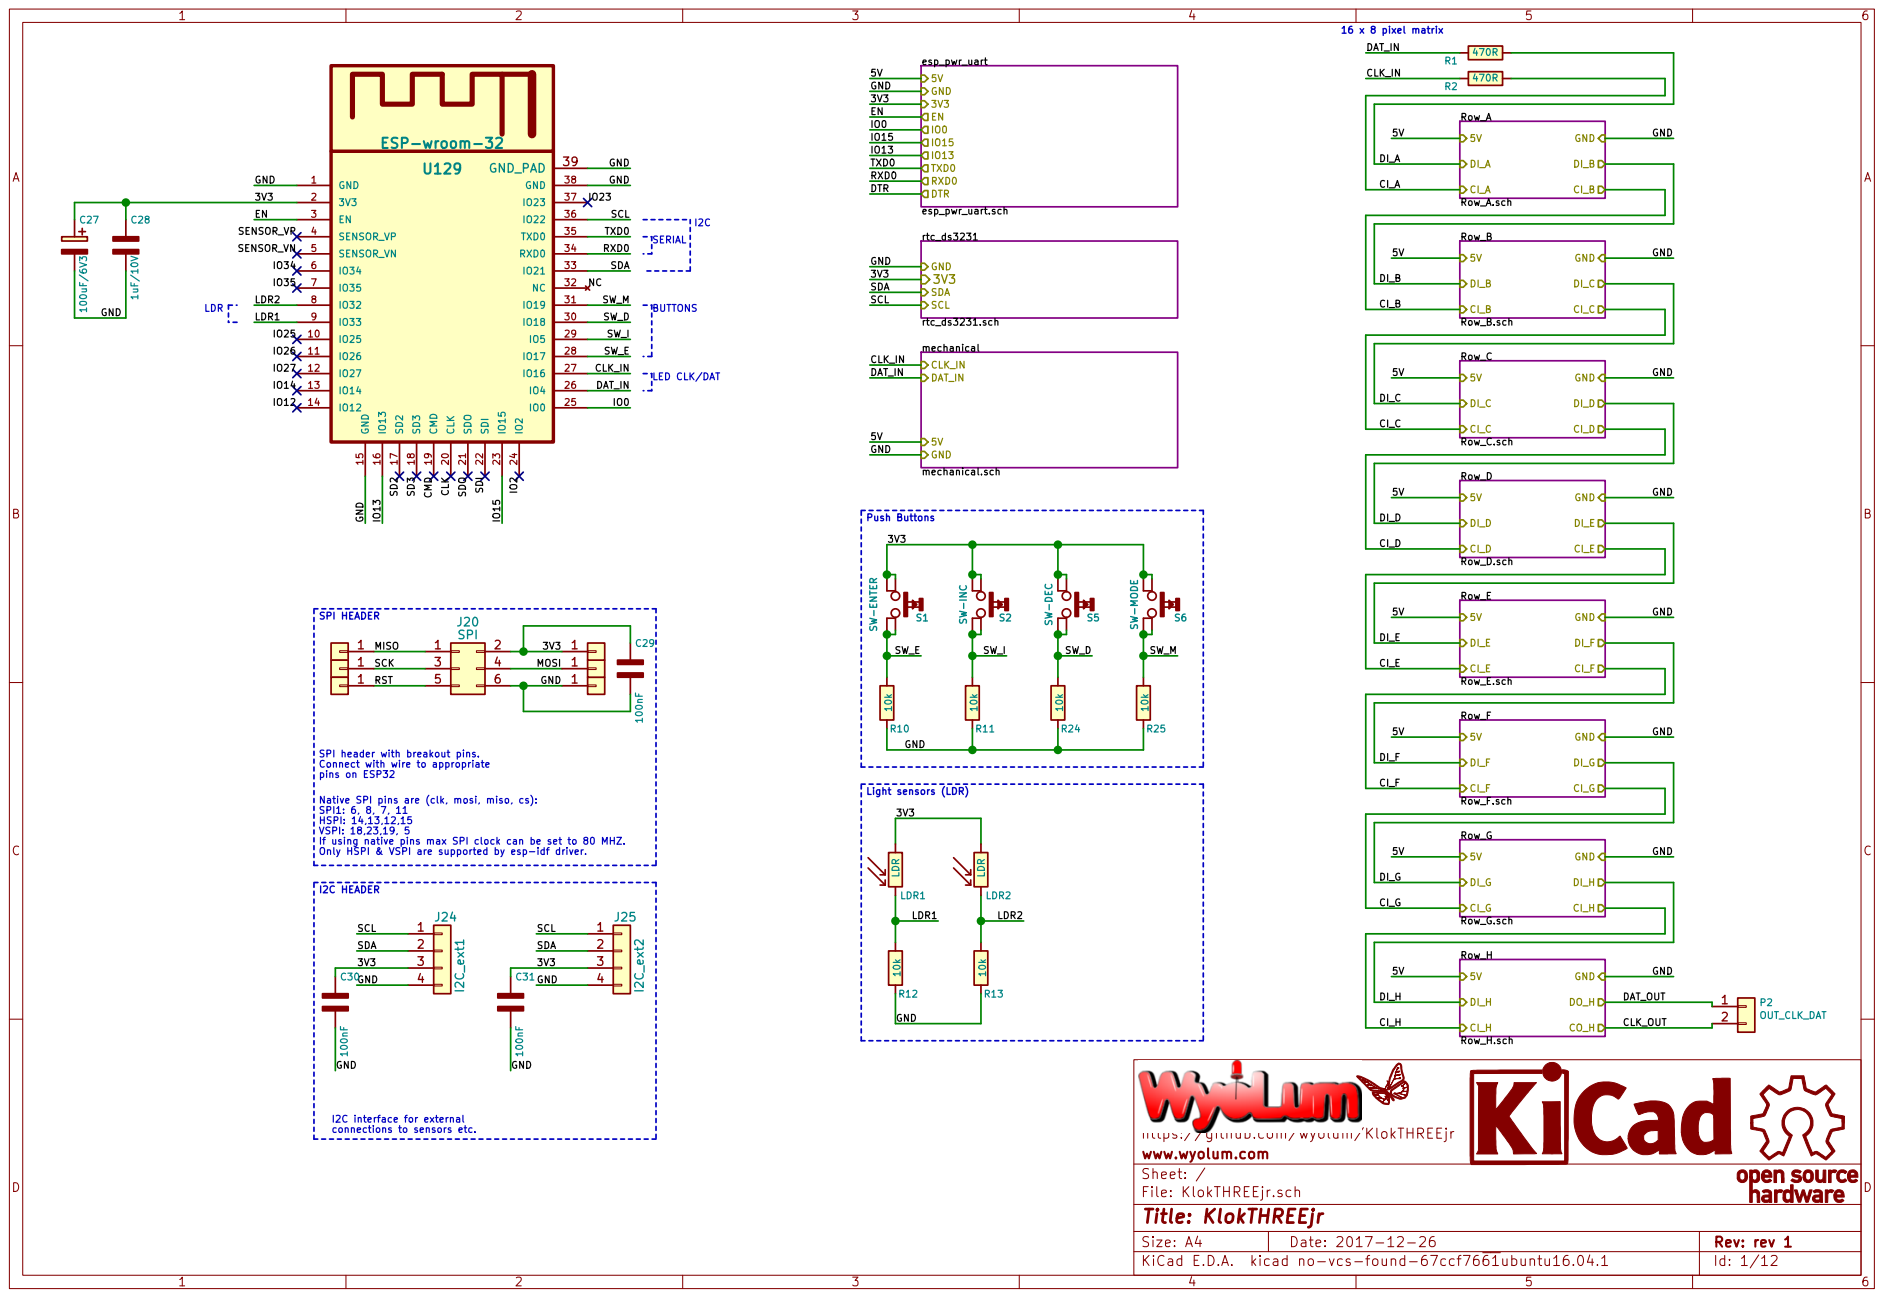
[picture p79: page 1]

3V3 Native SPI pins are (clk, mosi, miso, cs): SPI1: 6, 8, 7, 11 HSPI: 14,13,12,15 VSPI: 18,23,19, 5

GND GND GND GND GND

SPI header with breakout pins. Connect with wire to appropriate

I2C interface for external connections to sensors etc.

https://github.com/wyolum/KlokTHREEjr
File: KlokTHREEjr.sch Sheet: / www.wyolum.com

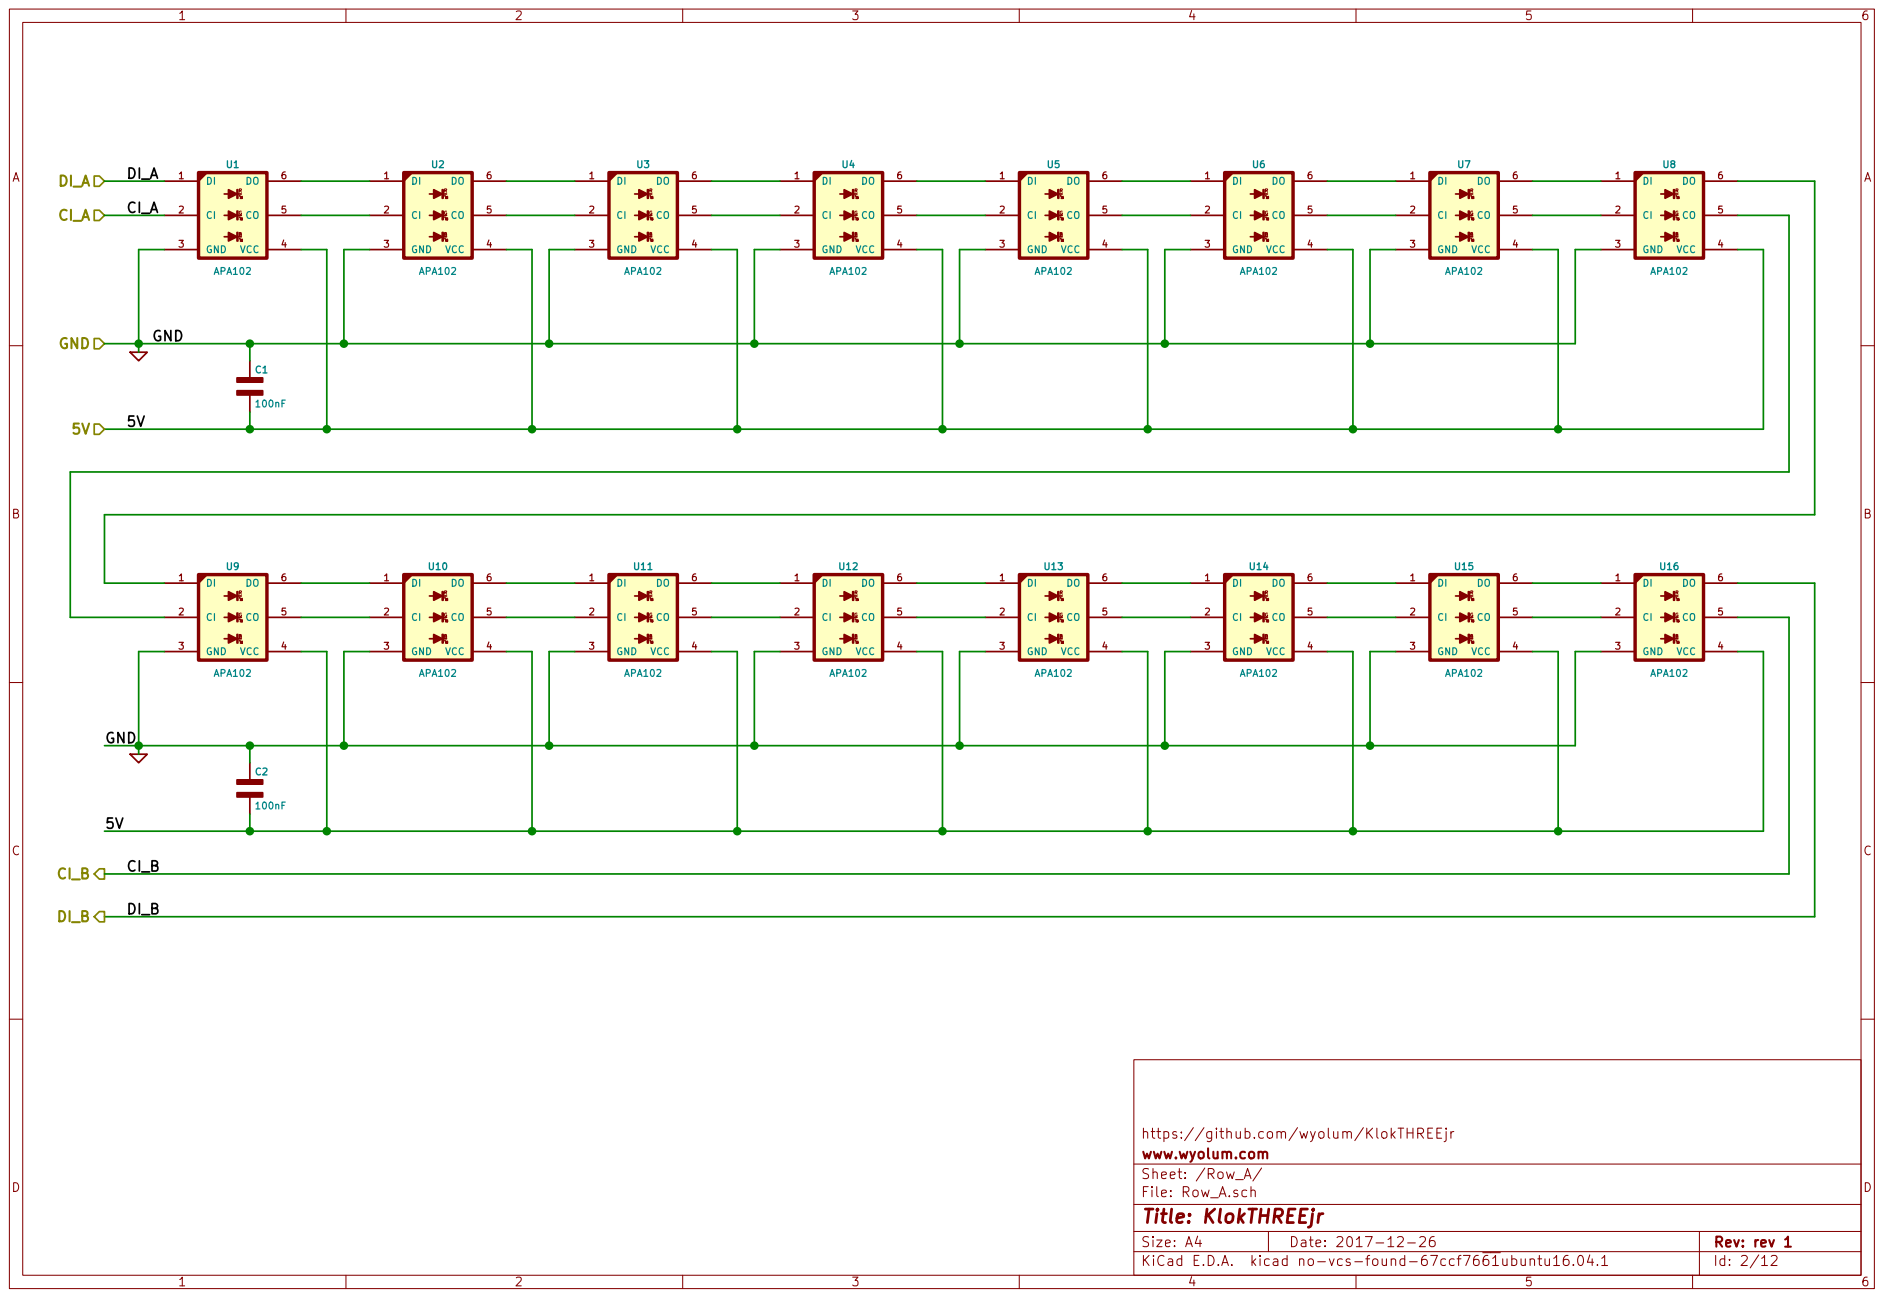
[picture p80: page 2]

https://github.com/wyolum/KlokTHREEjr
www.wyolum.com
Sheet: /Row_A/
File: Row_A.sch
Id: 2/12 Title: KlokTHREEjr

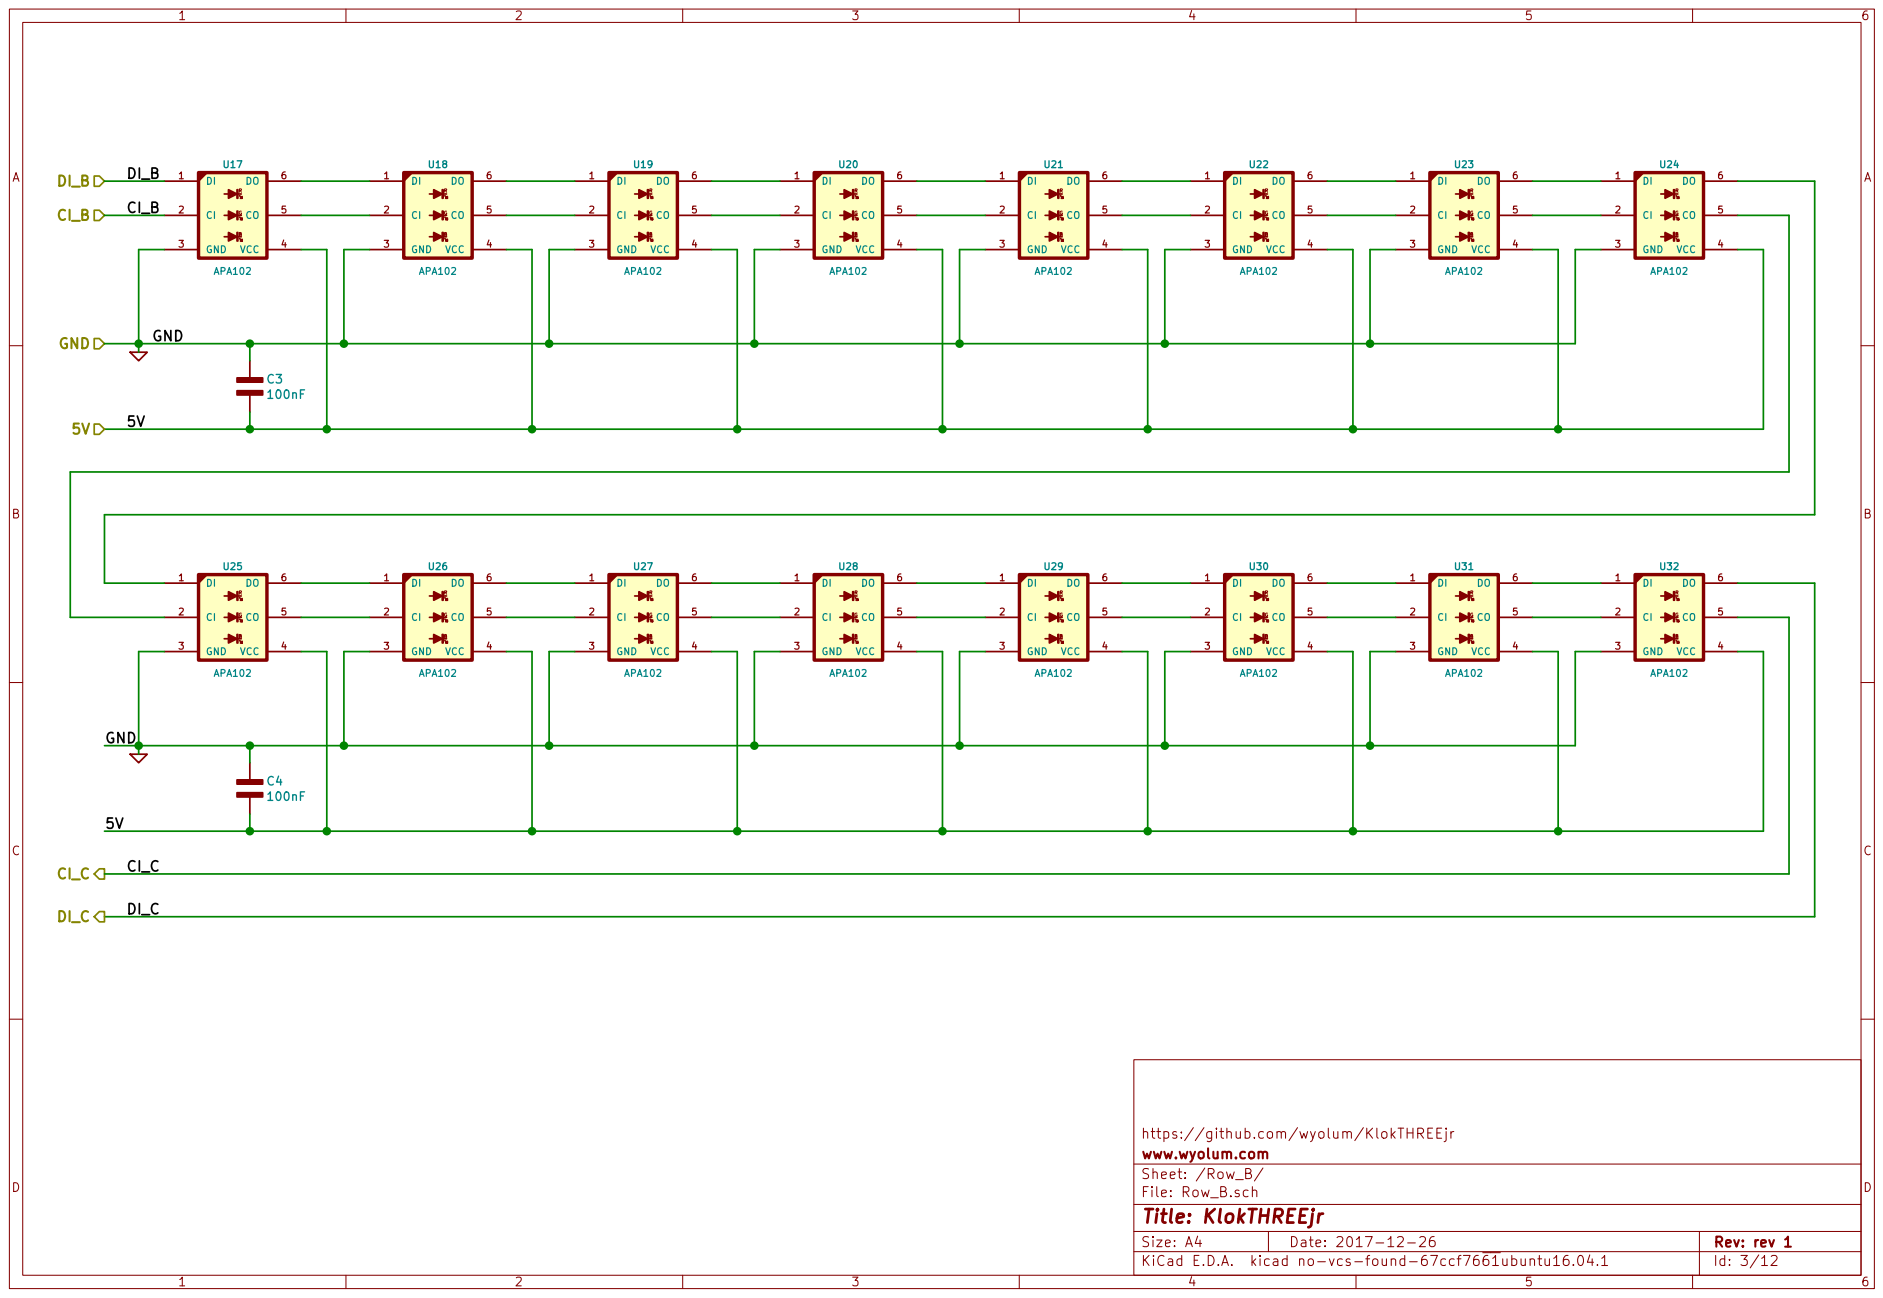
[picture p81: page 3]

https://github.com/wyolum/KlokTHREEjr
www.wyolum.com
Sheet: /Row_B/
File: Row_B.sch
Id: 3/12 Title: KlokTHREEjr

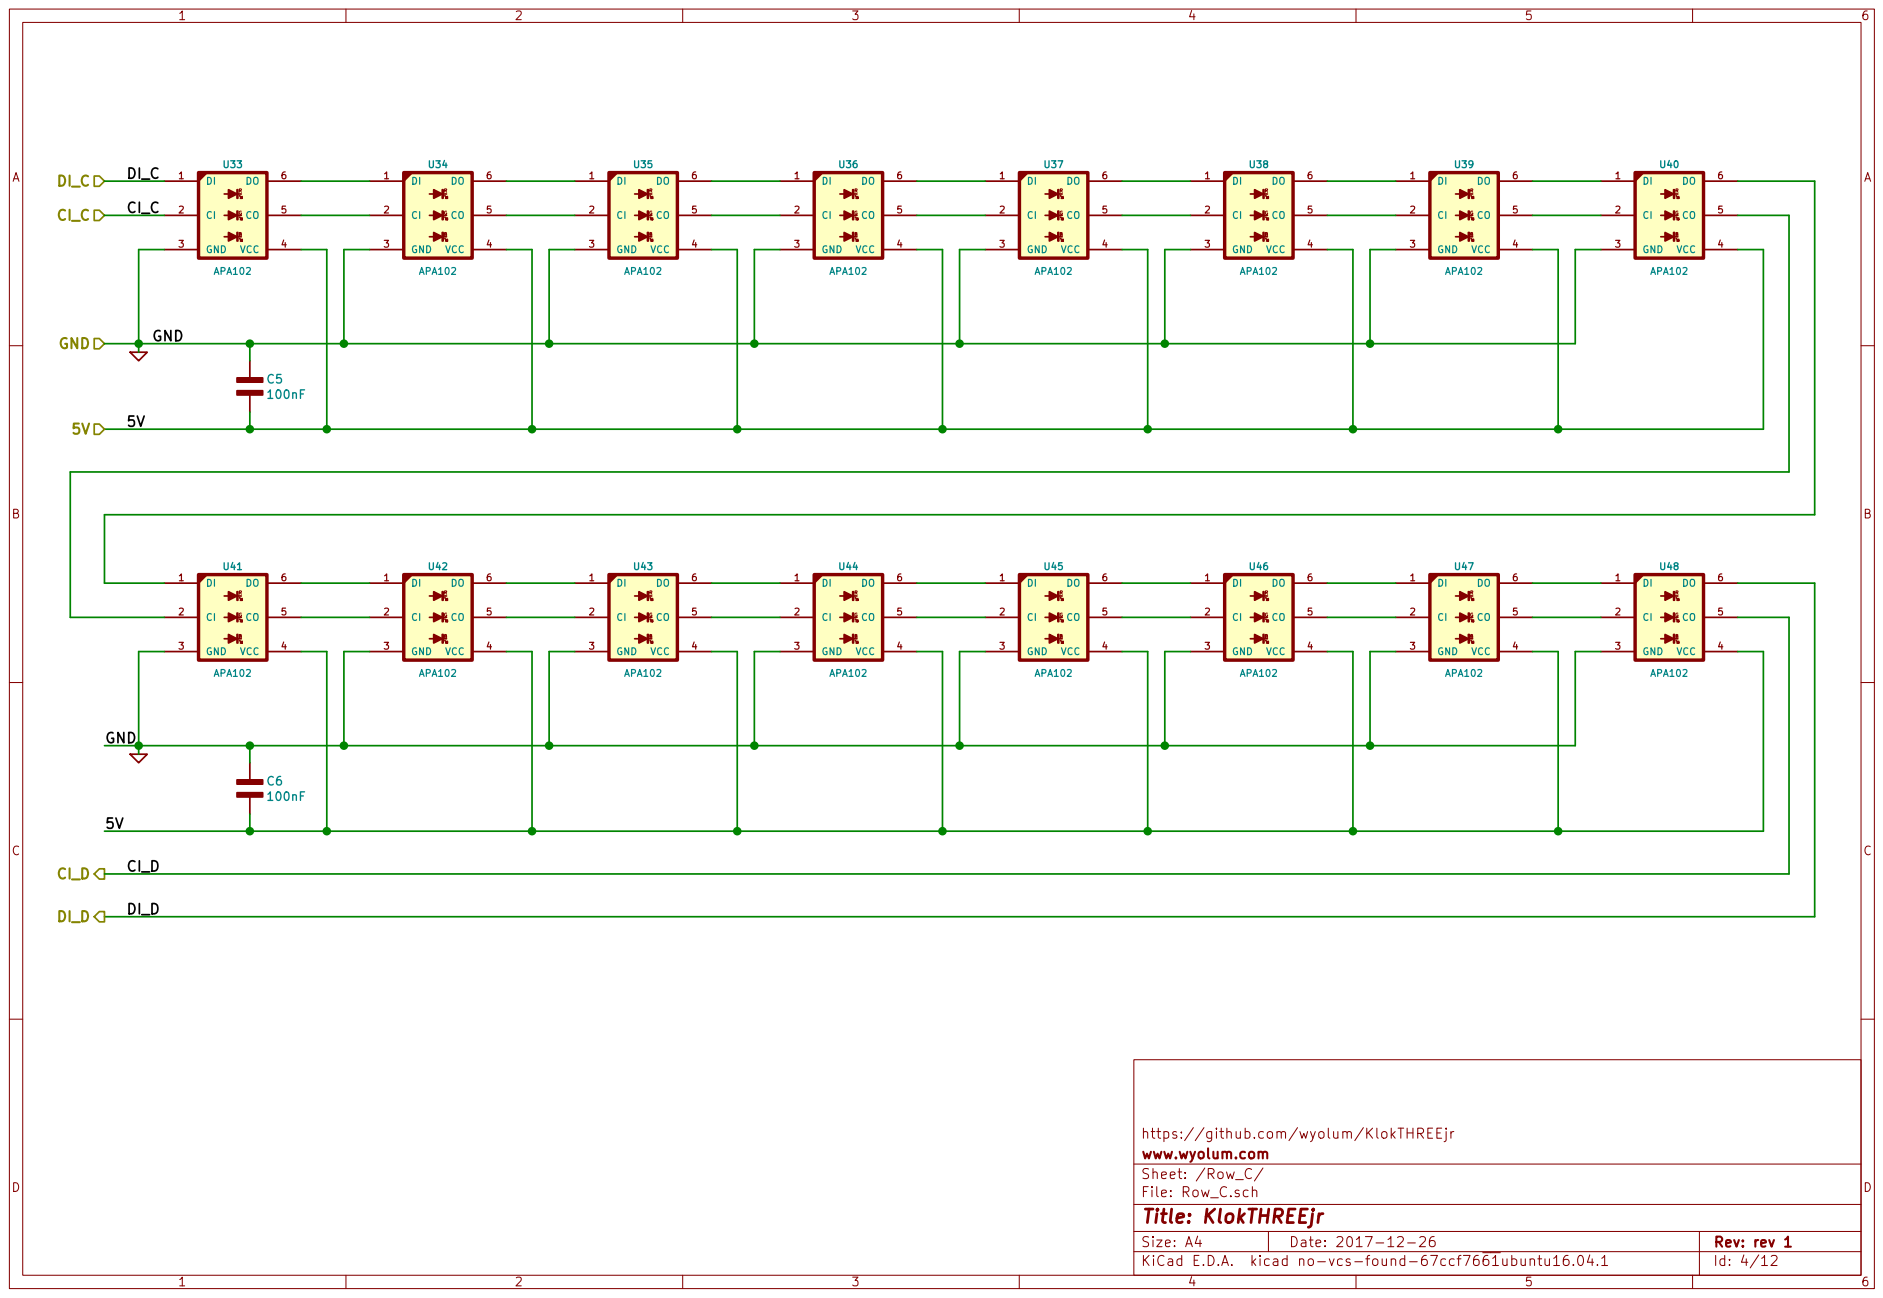
[picture p82: page 4]

https://github.com/wyolum/KlokTHREEjr
www.wyolum.com
Sheet: /Row_C/
File: Row_C.sch
Id: 4/12 Title: KlokTHREEjr

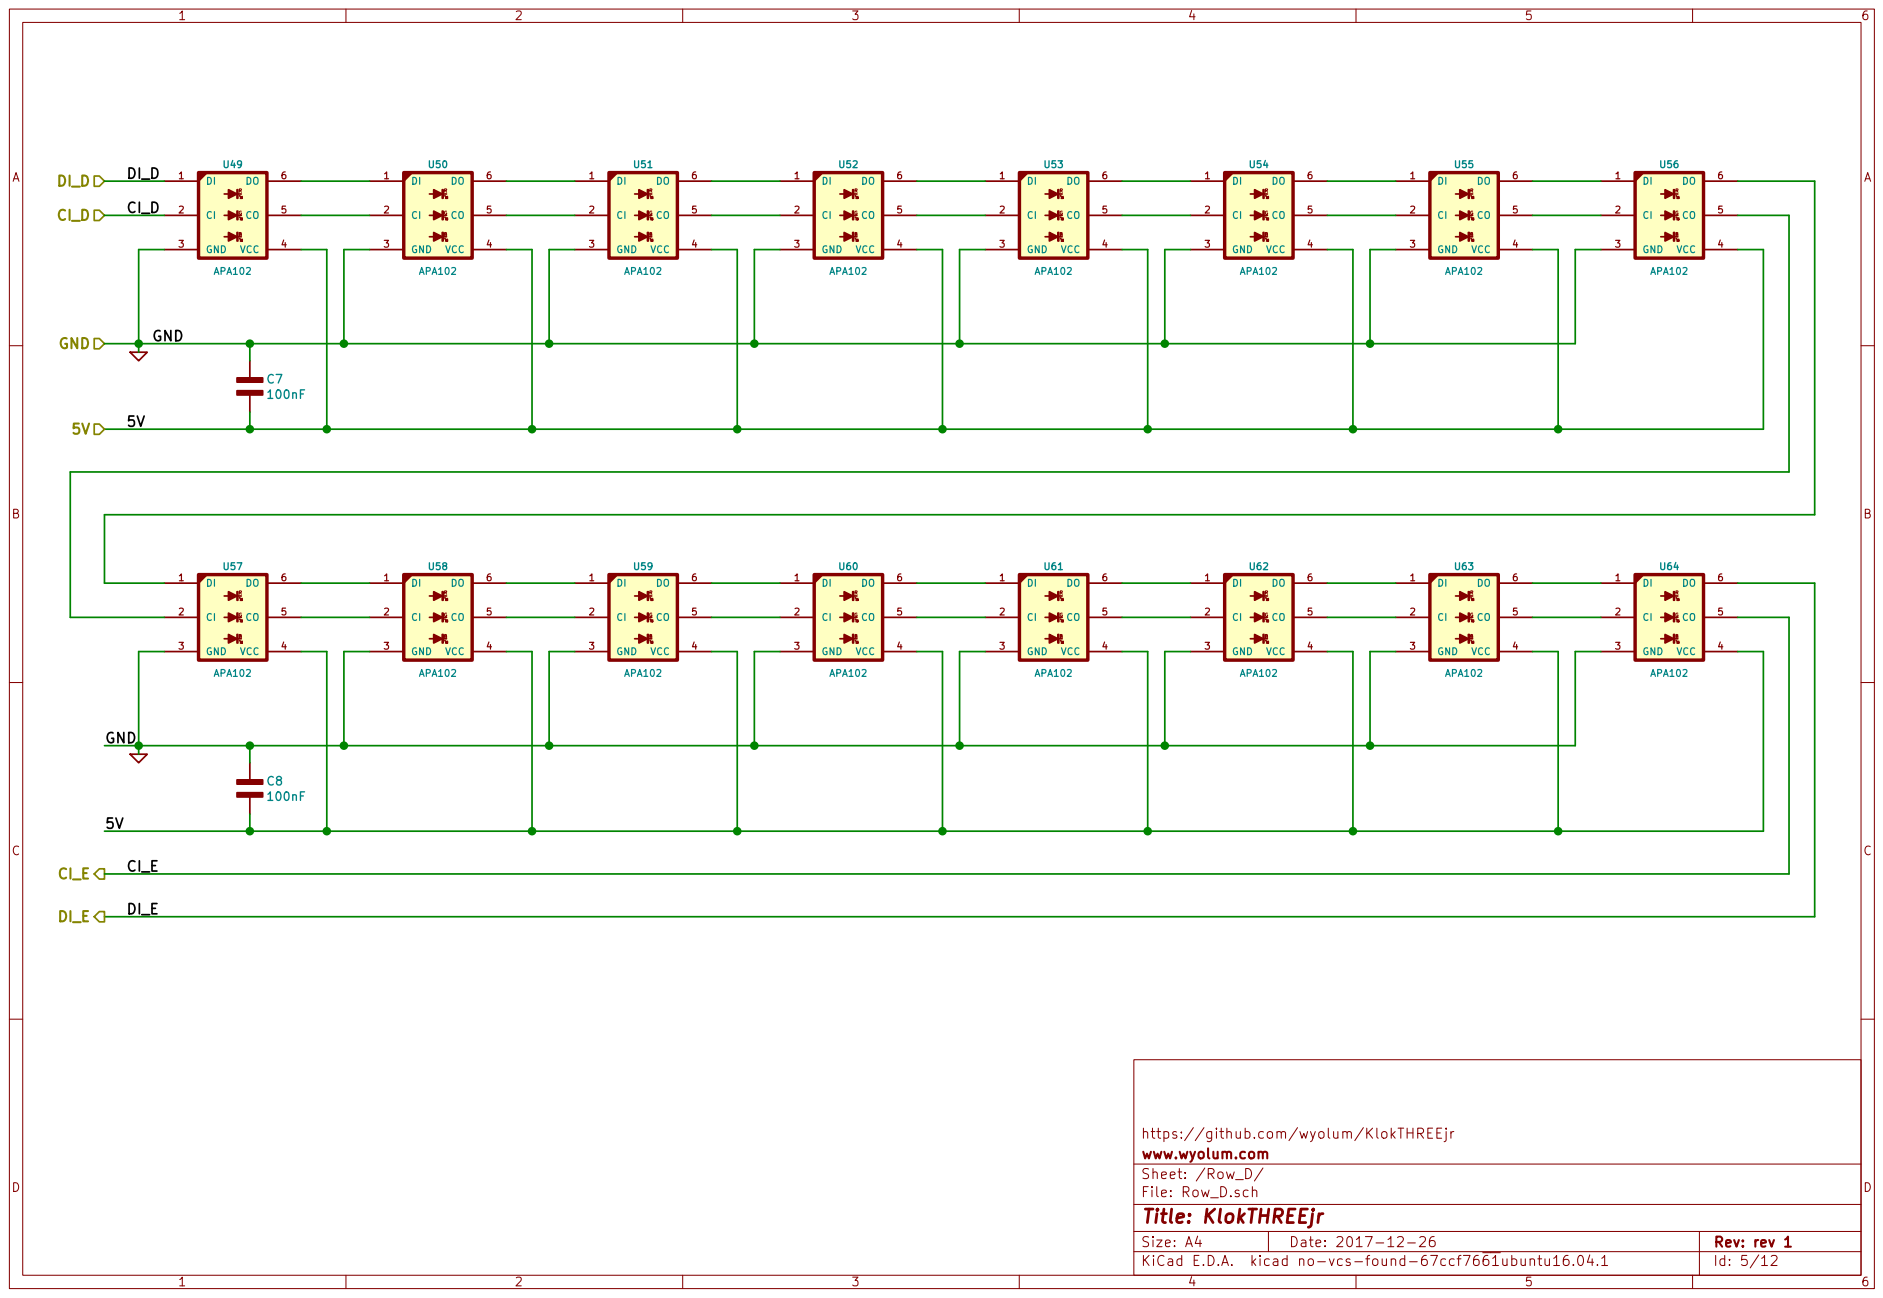
[picture p83: page 5]

https://github.com/wyolum/KlokTHREEjr
www.wyolum.com
Sheet: /Row_D/
File: Row_D.sch
Id: 5/12 Title: KlokTHREEjr

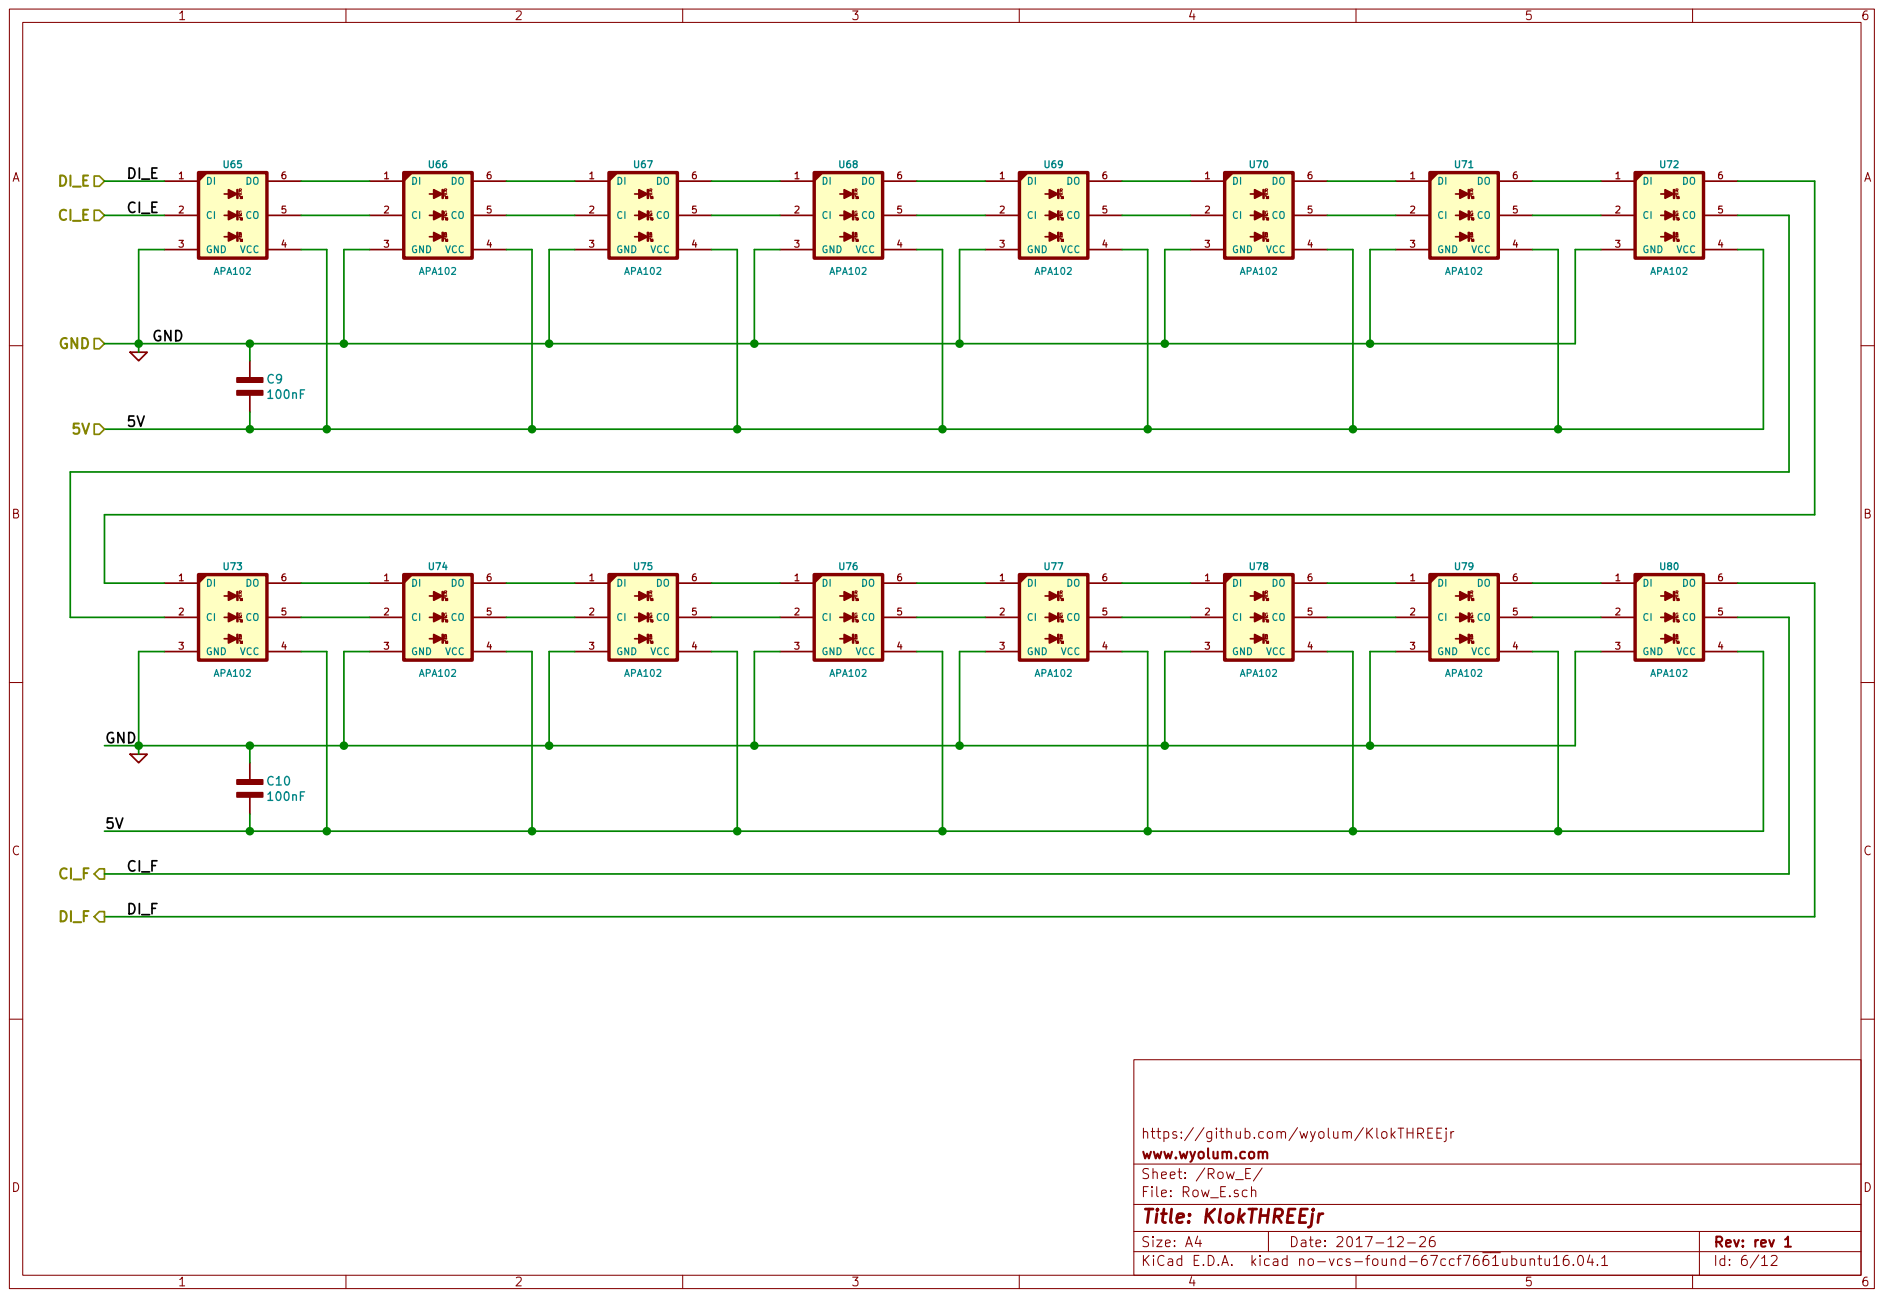
[picture p84: page 6]

https://github.com/wyolum/KlokTHREEjr
www.wyolum.com
Sheet: /Row_E/
File: Row_E.sch
Id: 6/12 Title: KlokTHREEjr

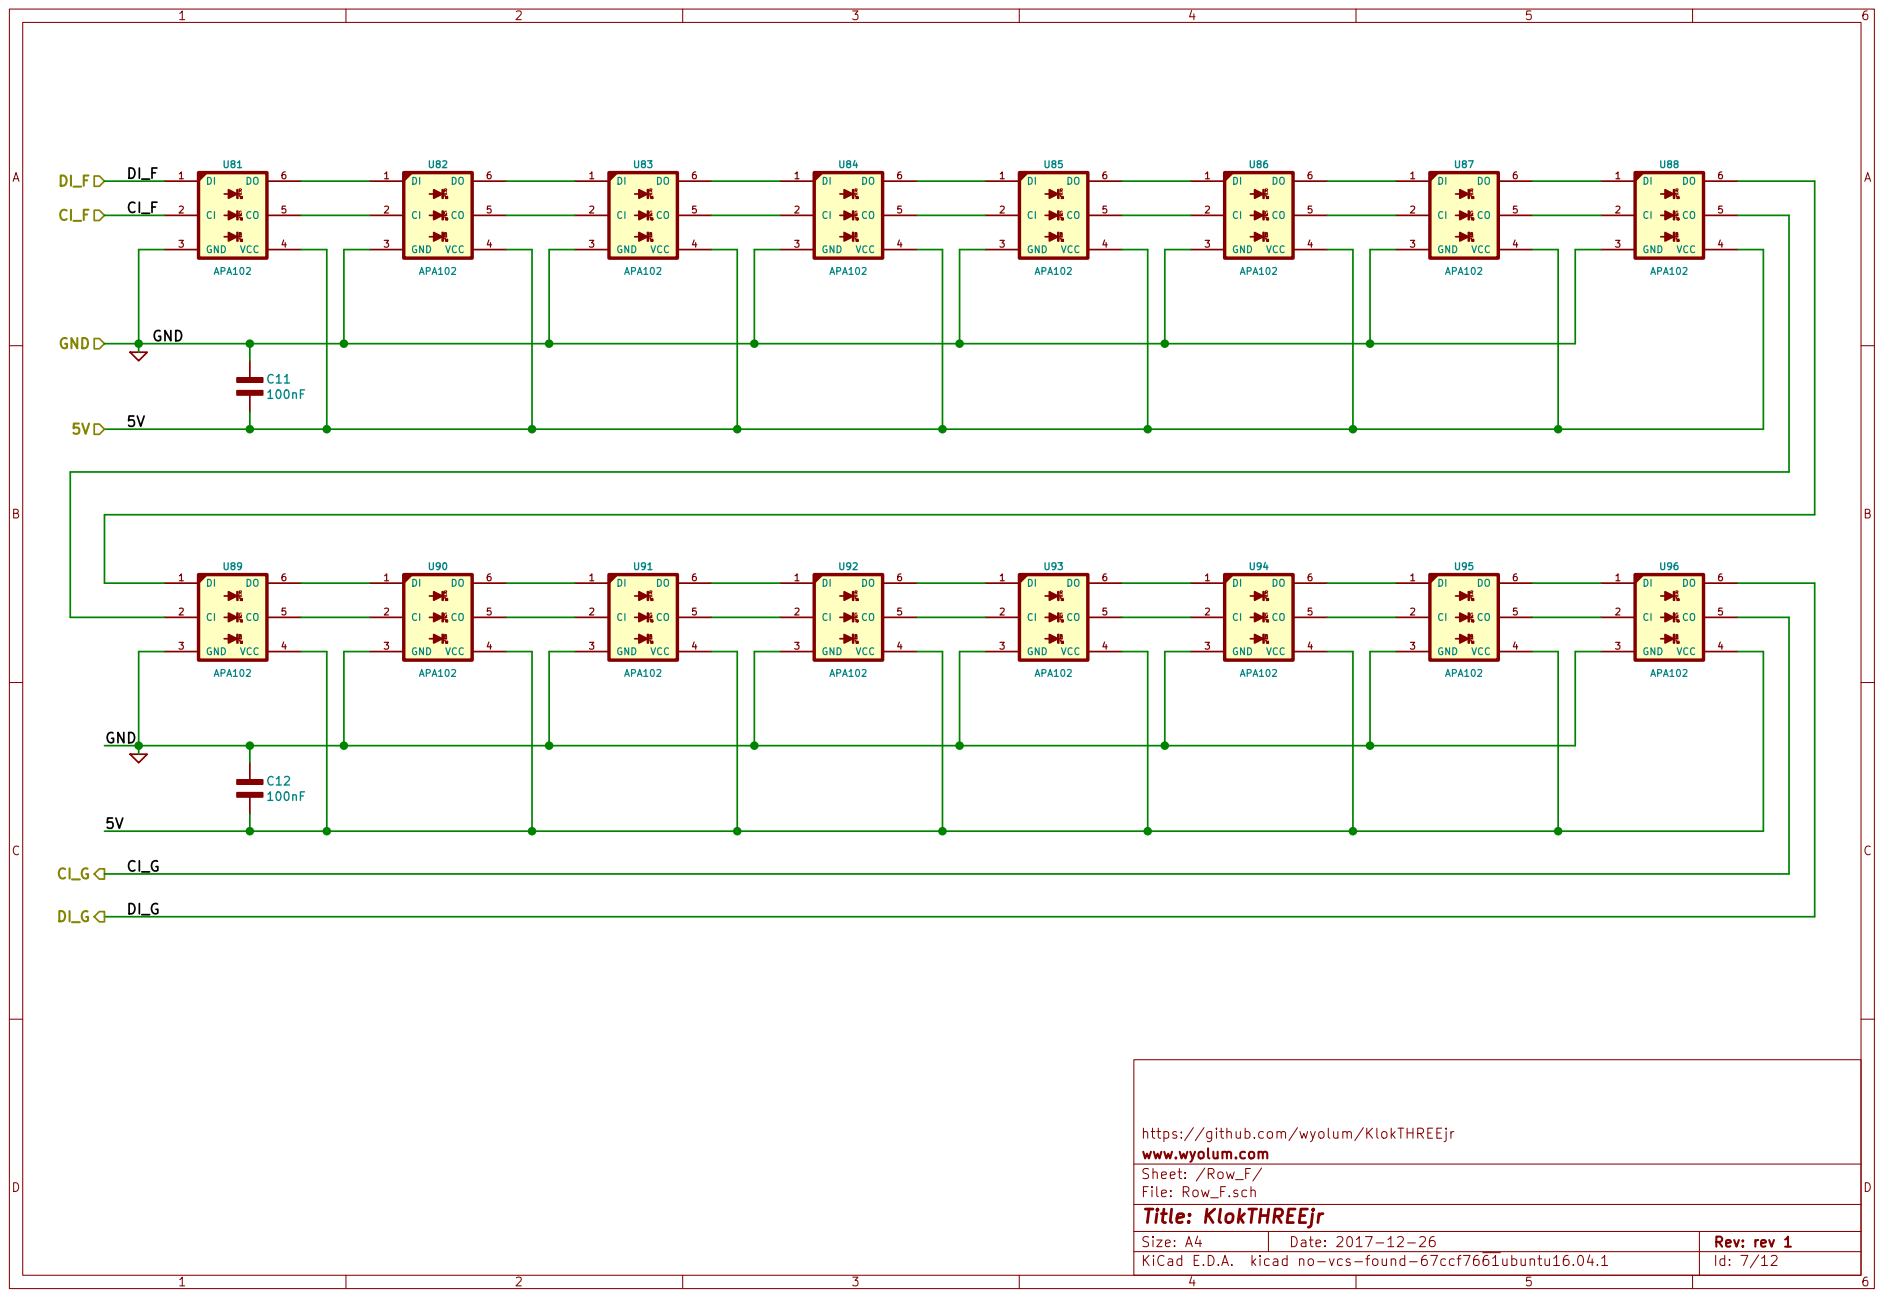
[picture p85: page 7]

https://github.com/wyolum/KlokTHREEjr
www.wyolum.com
Sheet: /Row_F/
File: Row_F.sch
Id: 7/12 Title: KlokTHREEjr

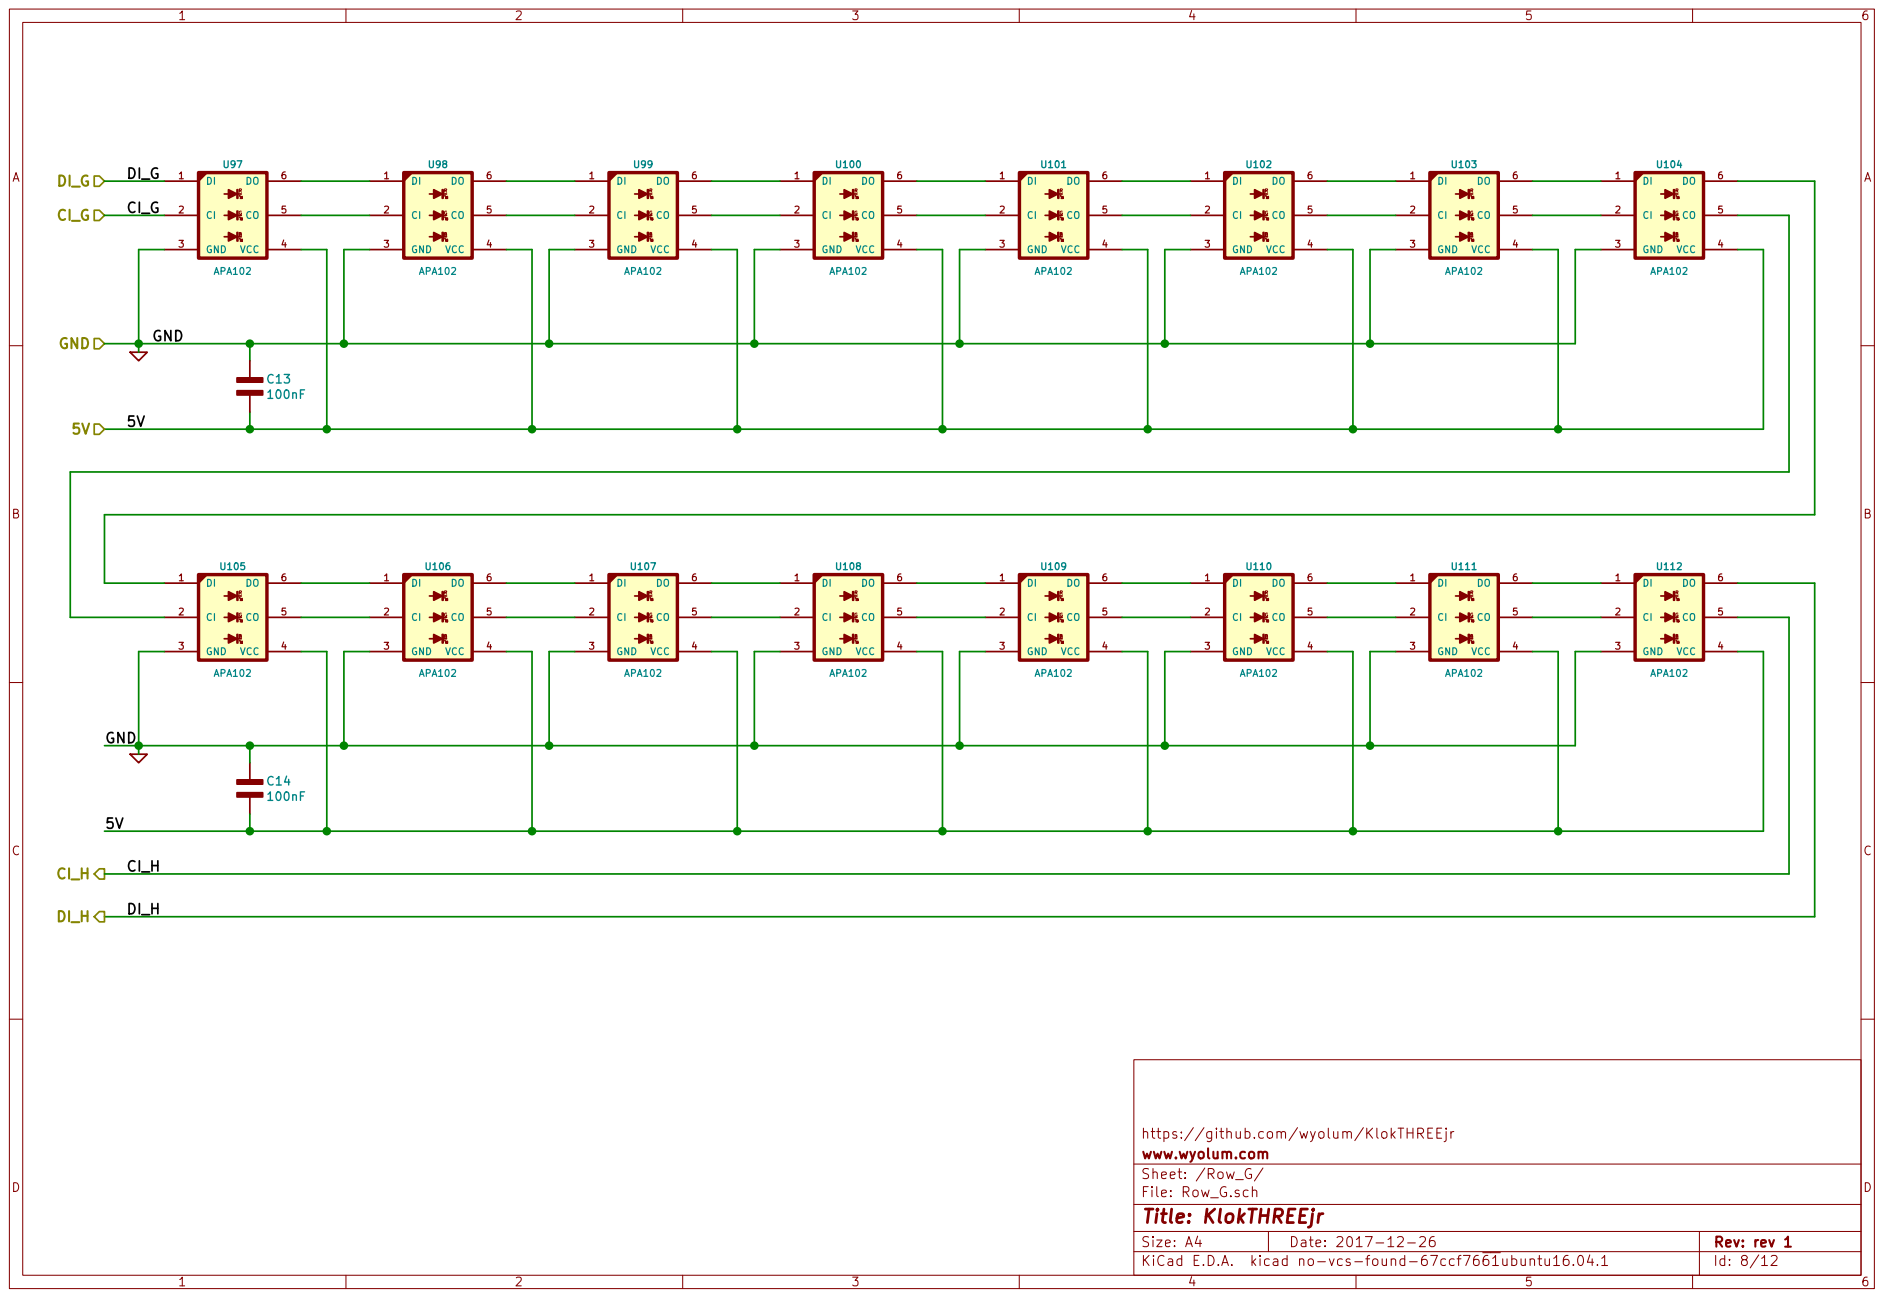
[picture p86: page 8]

https://github.com/wyolum/KlokTHREEjr
www.wyolum.com
Sheet: /Row_G/
File: Row_G.sch
Id: 8/12 Title: KlokTHREEjr

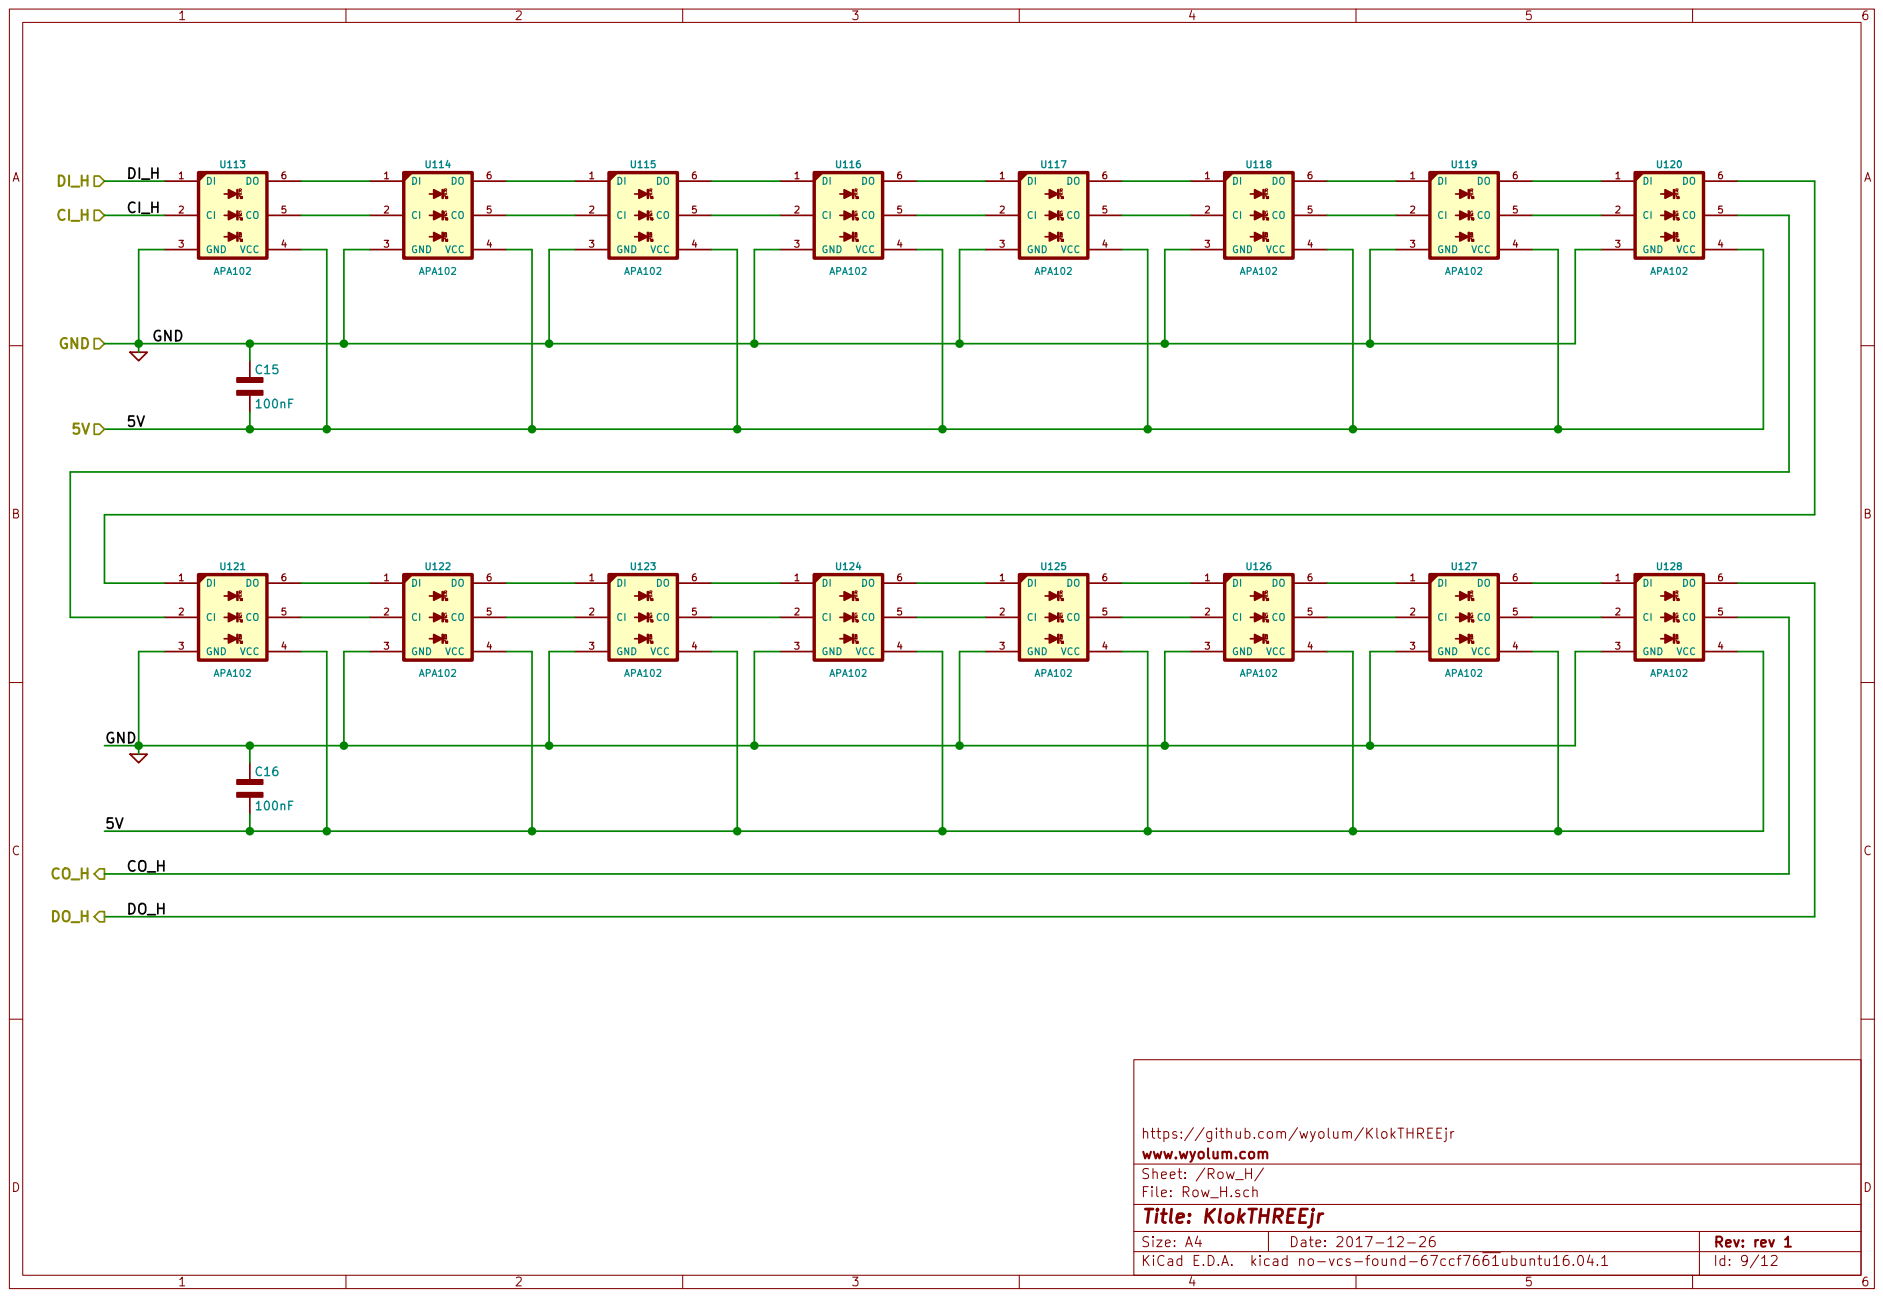
[picture p87: page 9]

https://github.com/wyolum/KlokTHREEjr
www.wyolum.com
Sheet: /Row_H/
File: Row_H.sch
Id: 9/12 Title: KlokTHREEjr

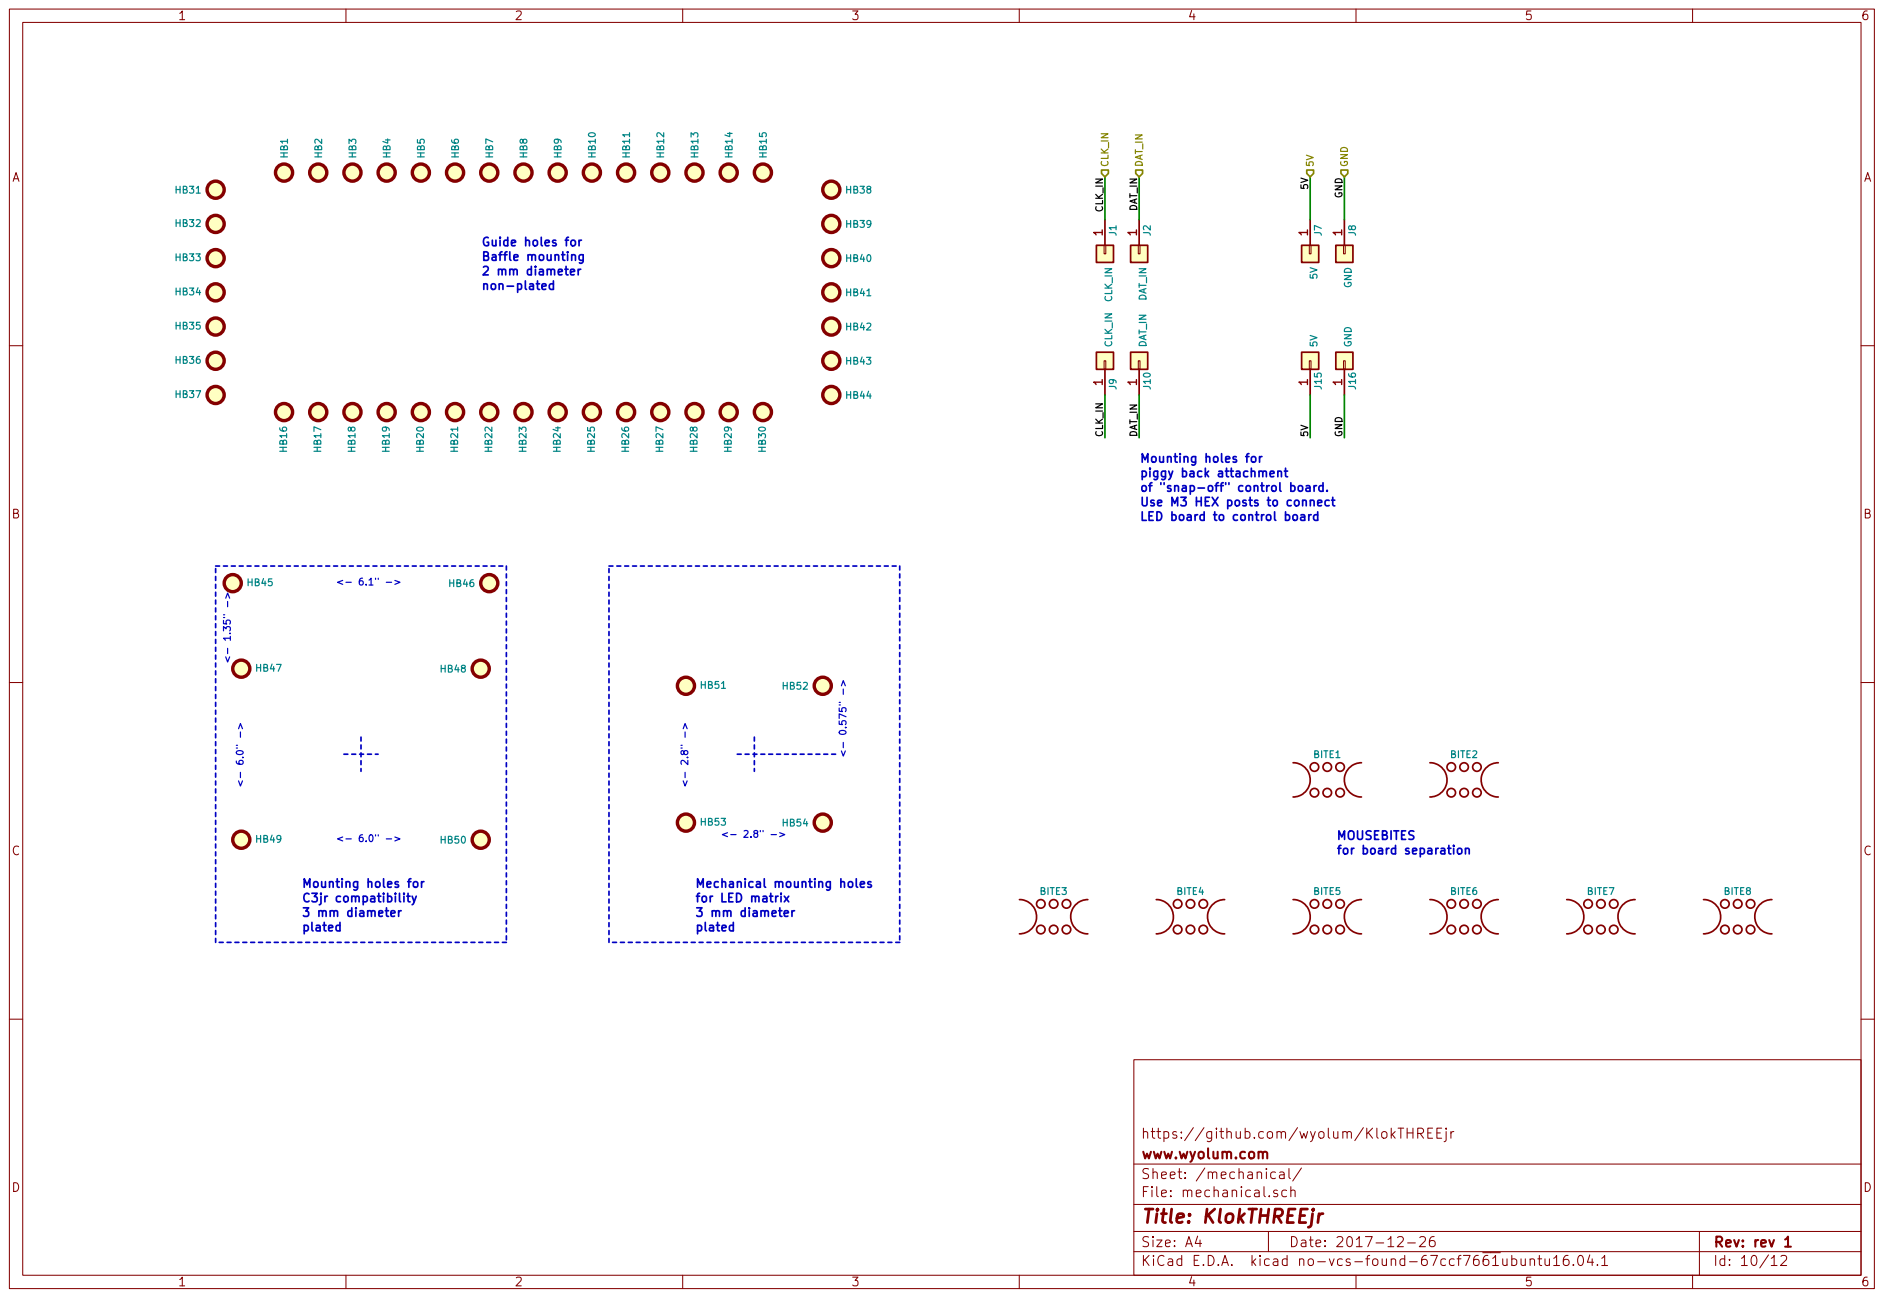
[picture p88: page 10]

2 mm diameter non-plated

Mounting holes for
piggy back attachment
of "snap-off" control board.

Id: 10/12 Title: KlokTHREEjr File: mechanical.sch Sheet: /mechanical/ www.wyolum.com

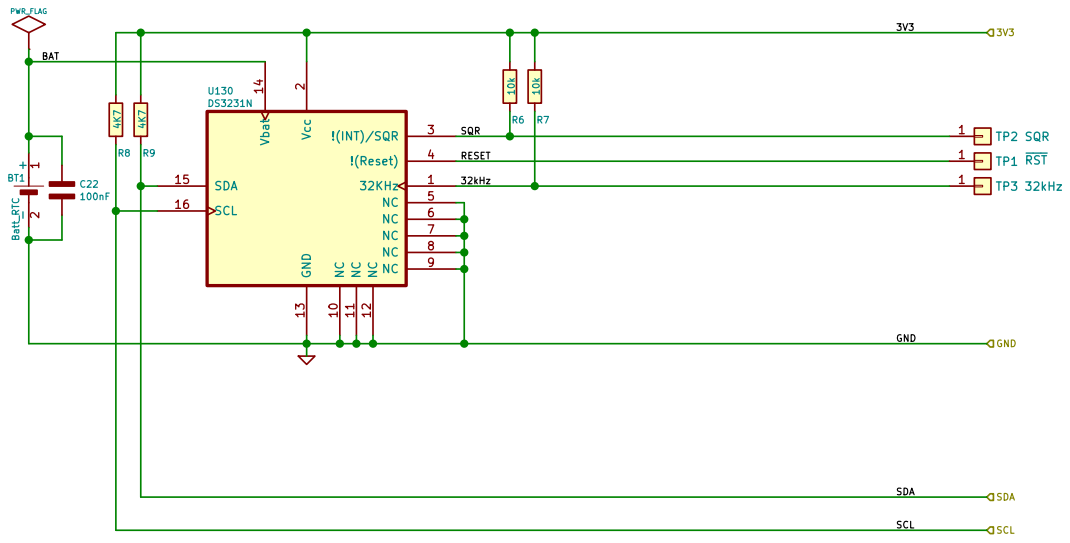
[picture p89: page 11]

https://github.com/wyolum/KlokTHREEjr
www.wyolum.com
Sheet: /rtc_ds3231/
File: rtc_ds3231.sch
Id: 11/12 Title: KlokTHREEjr

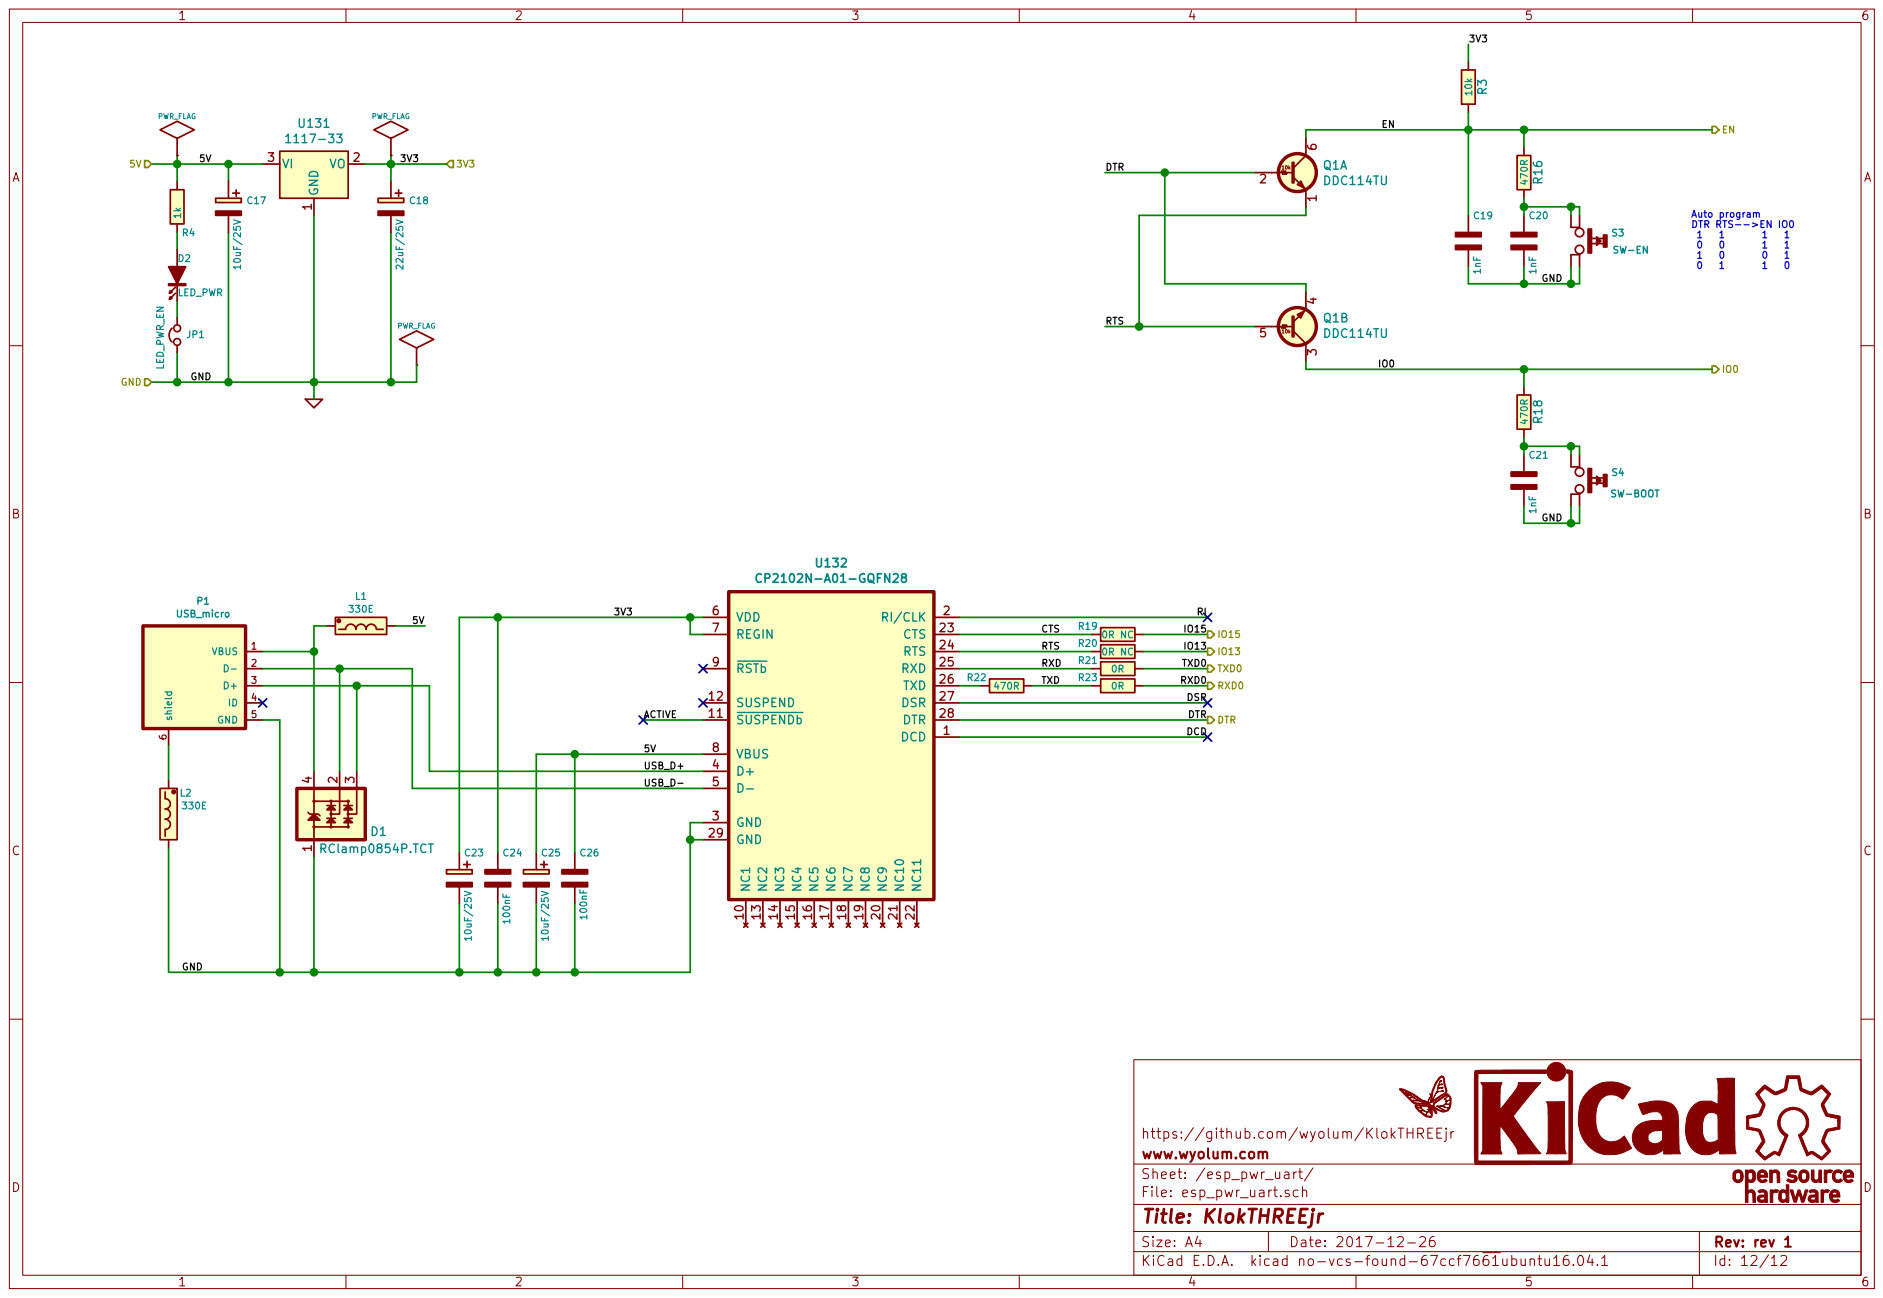
[picture p90: page 12]

https://github.com/wyolum/KlokTHREEjr
www.wyolum.com
Sheet: /esp_pwr_uart/
File: esp_pwr_uart.sch
Id: 12/12 Title: KlokTHREEjr
