wyolum/KlokTHREEjr/kicad/KlokTHREEjr_data/ESP-WROOM-32-v3.2_sch.pdf

5

4

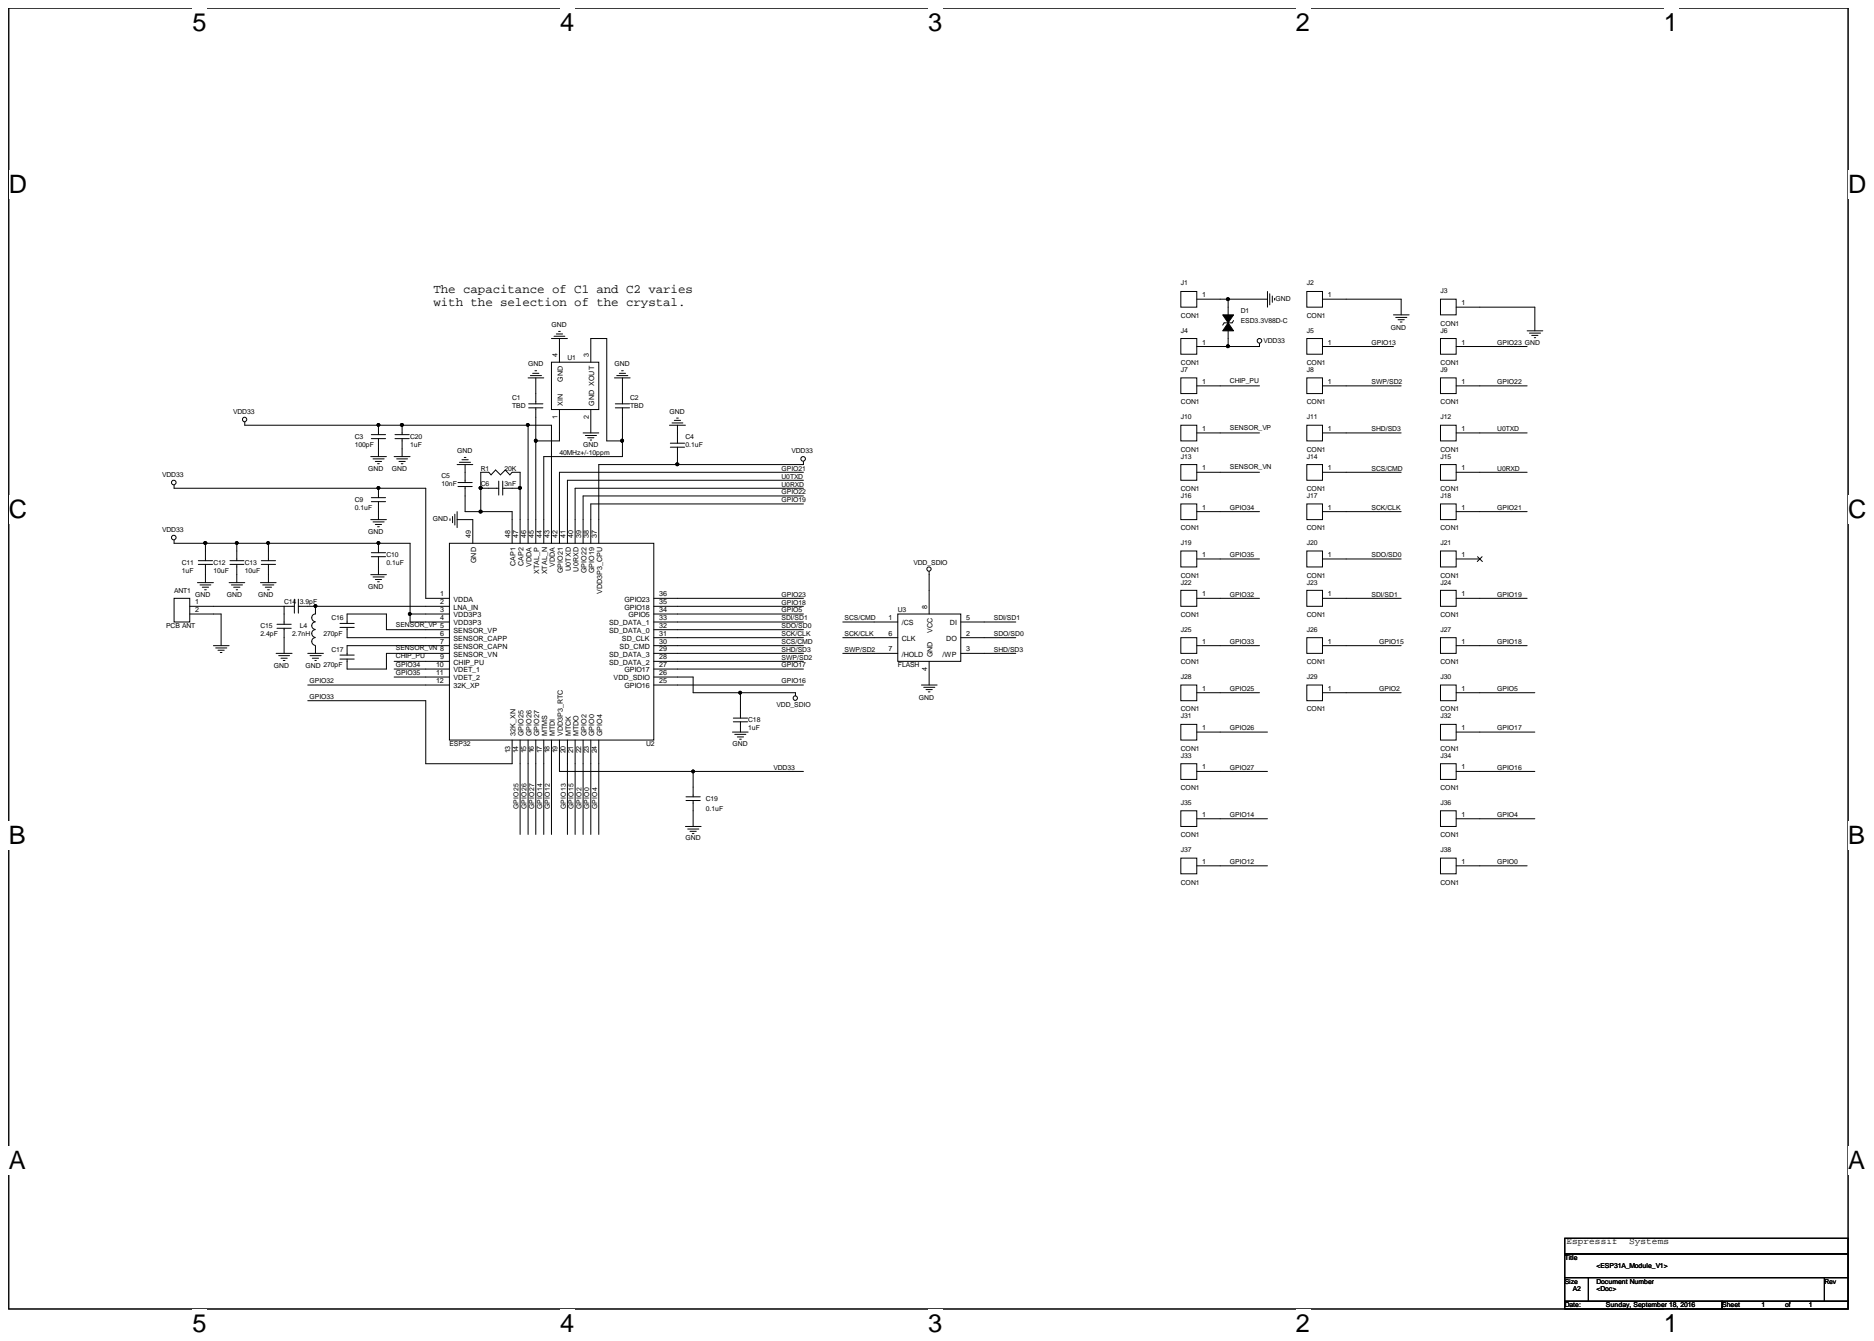
[picture p91: page 1]

The capacitance of C1 and C2 varies
with the selection of the crystal.
