wyolum/KlokTHREEjr/kicad/KlokTHREEjr_data/CR2032_batt_clip_BK-912_smd.pdf

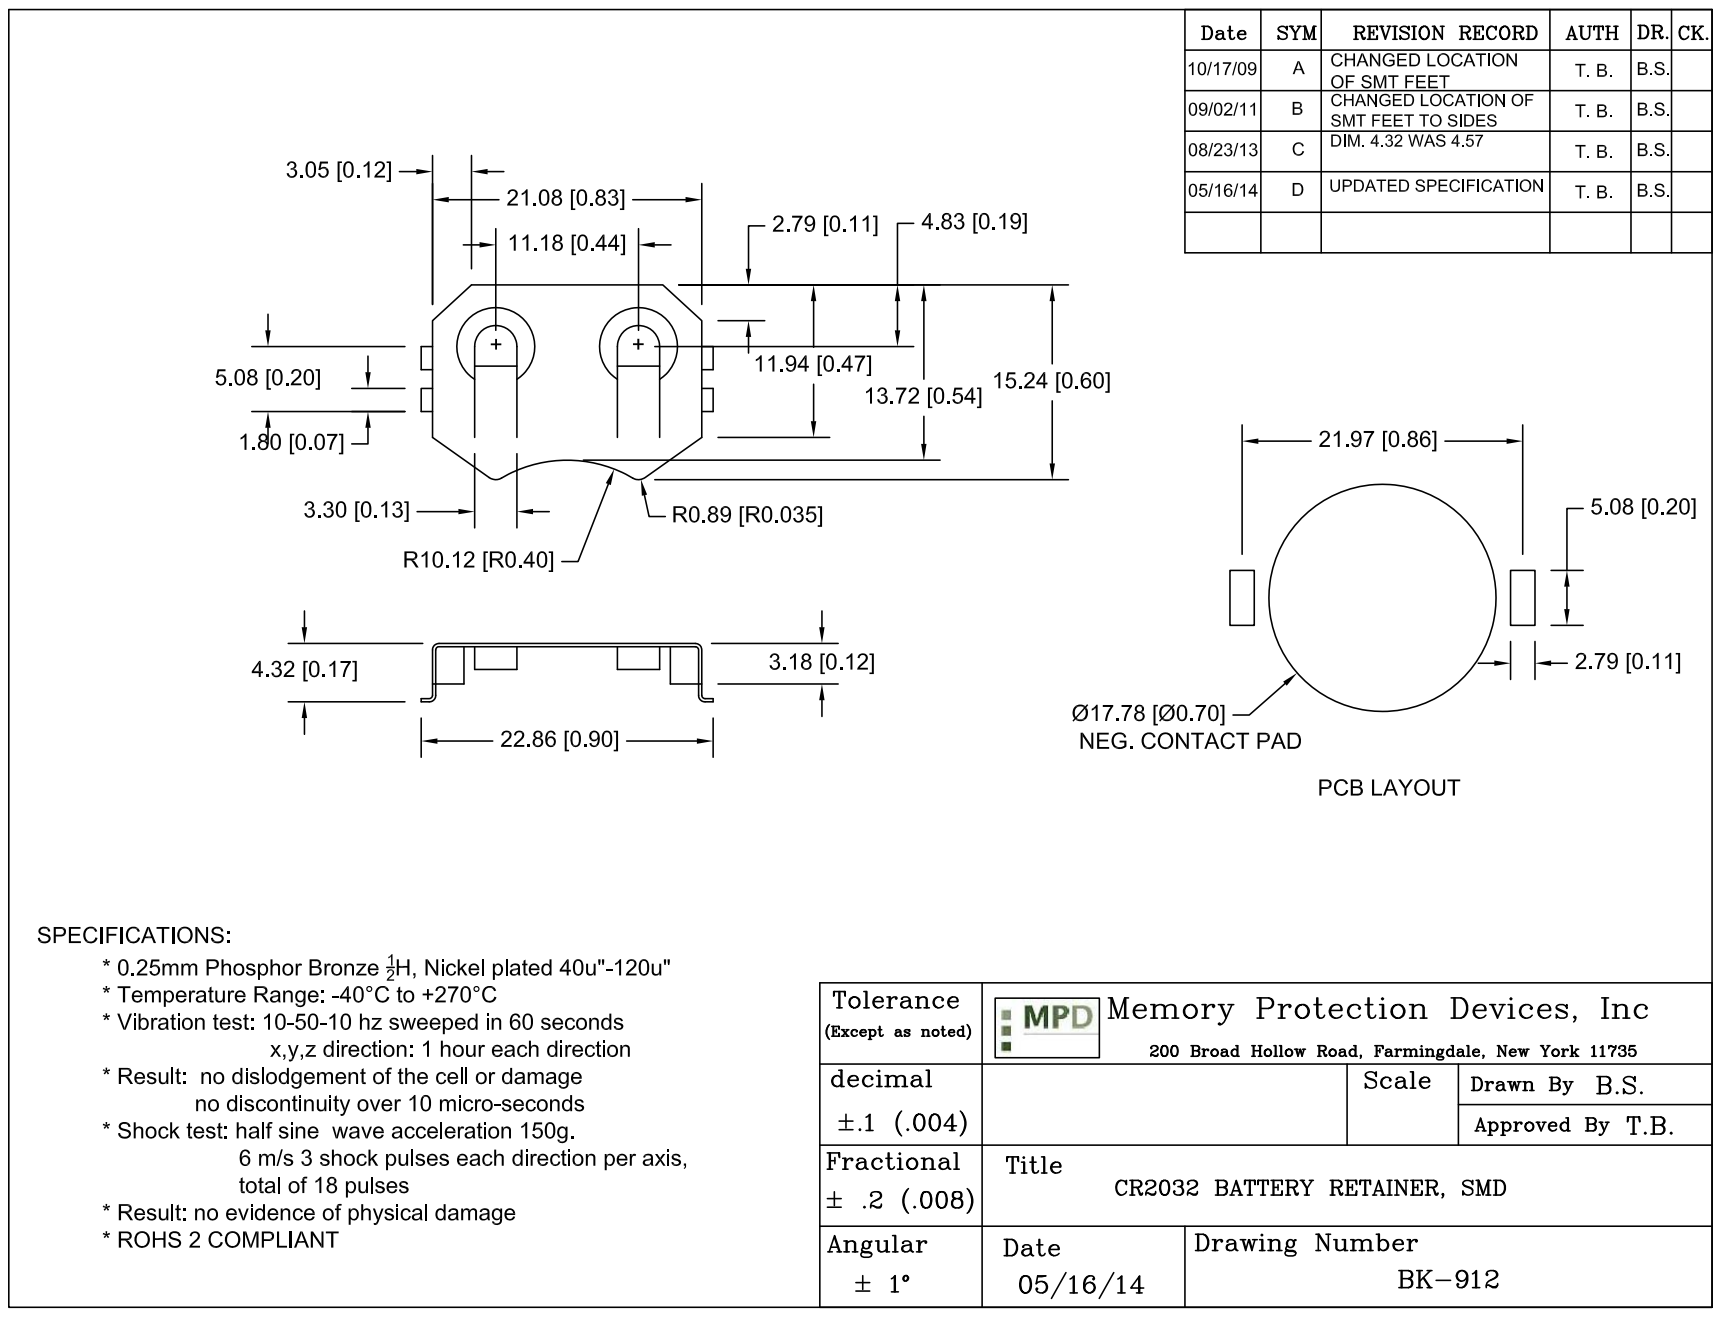
[picture p100: page 1]
