wyolum/KlokTHREEjr/k3jr_controller_kicad_v1/k3jr_controller_pdf/k3jr_controller-F.SilkS.pdf

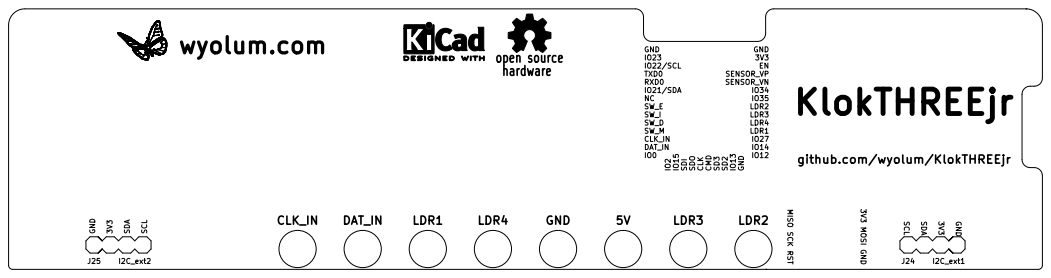
[picture p105: page 1]

github.com/wyolum/KlokTHREEjr

https://github.com/wyolum/KlokTHREEjr
File: k3jr_controller.kicad_pcb Sheet: www.wyolum.com
