wyolum/KlokTHREEjr/k3jr_controller_kicad_v1/k3jr_controller_pdf/k3jr_controller.pdf

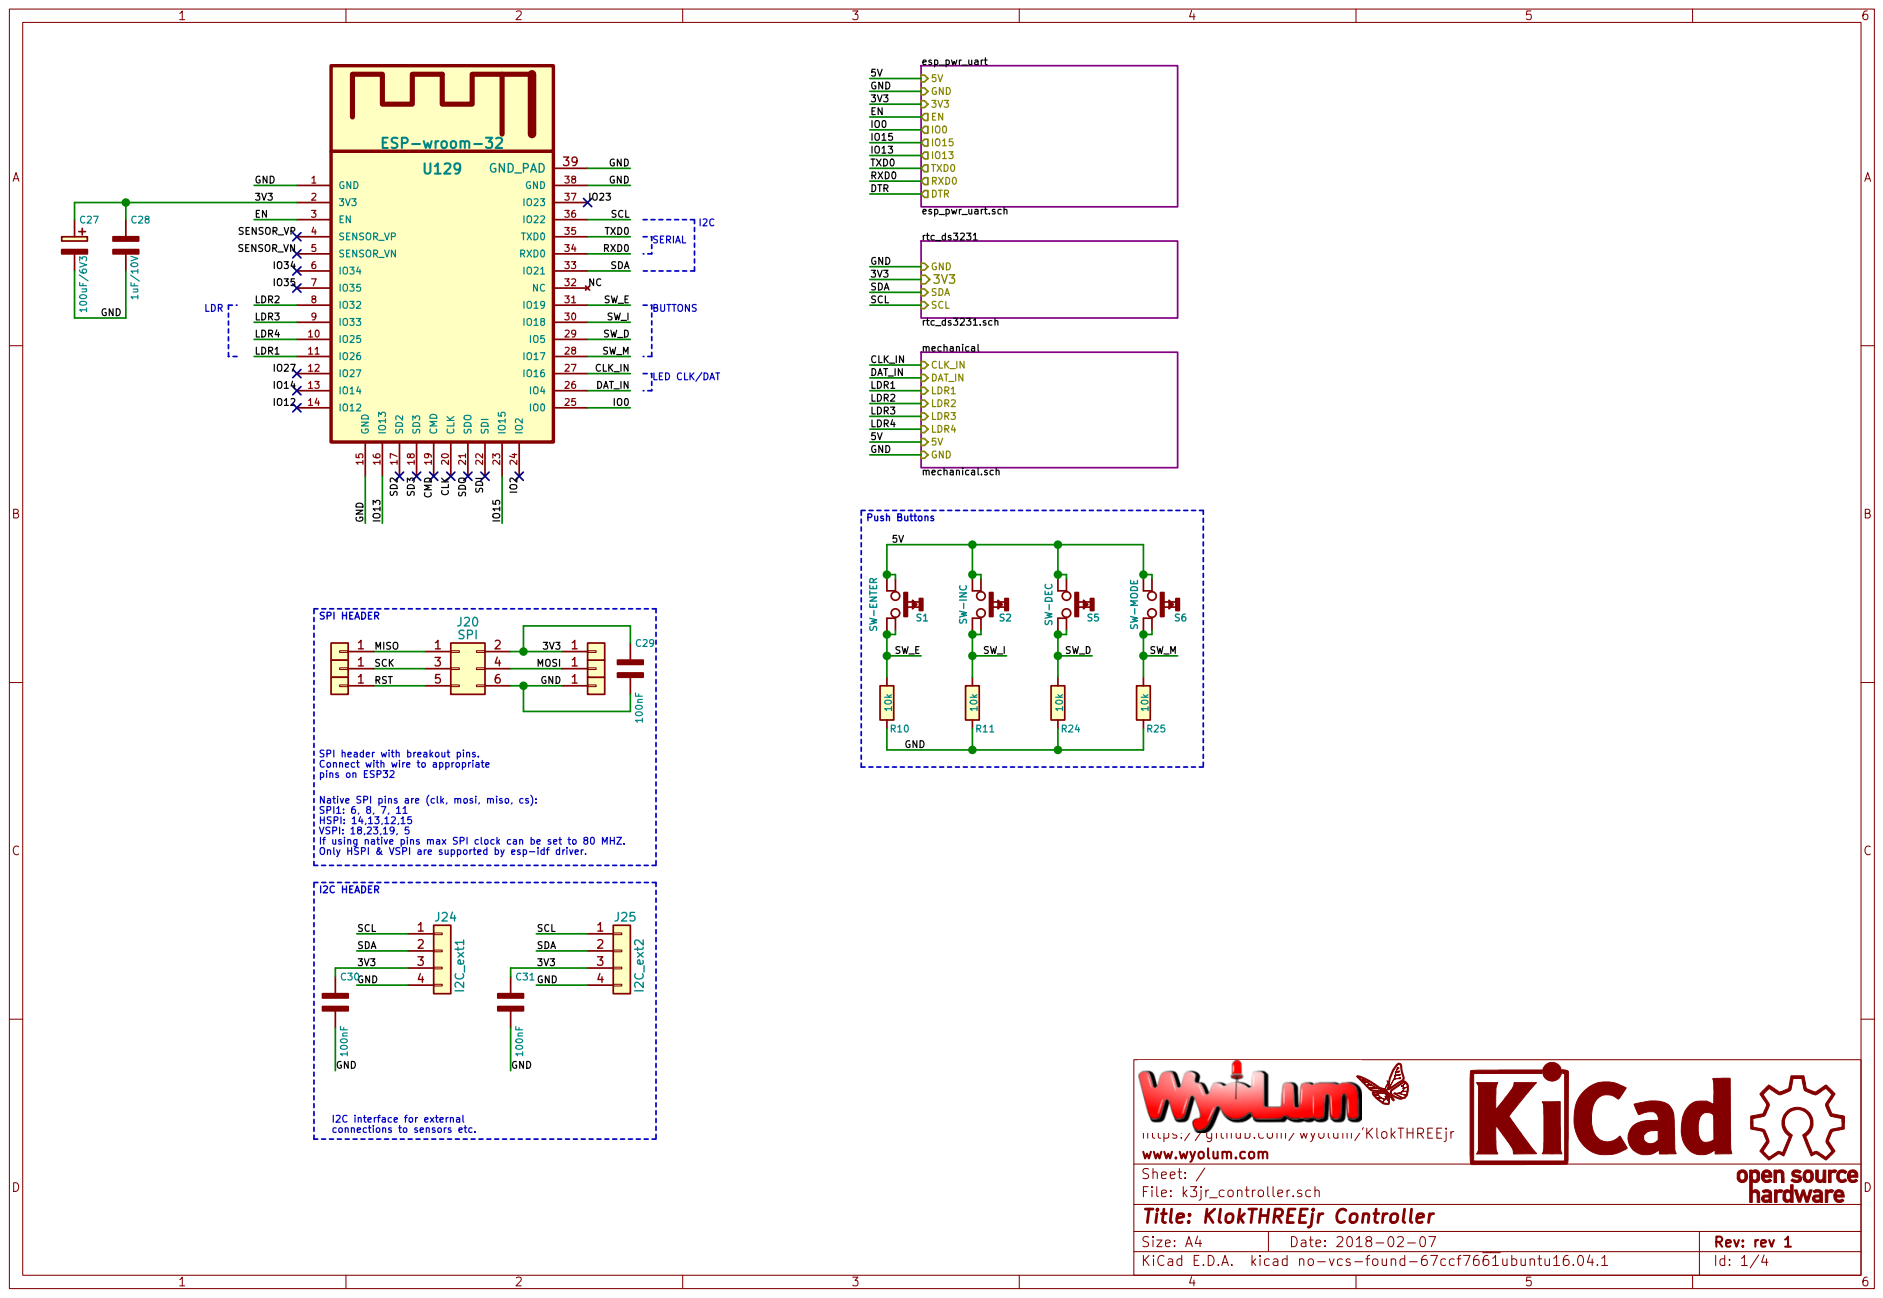
[picture p106: page 1]

3V3 Native SPI pins are (clk, mosi, miso, cs): SPI1: 6, 8, 7, 11 HSPI: 14,13,12,15 VSPI: 18,23,19, 5

SPI header with breakout pins. Connect with wire to appropriate

I2C interface for external connections to sensors etc.

https://github.com/wyolum/KlokTHREEjr
File: k3jr_controller.sch Sheet: / www.wyolum.com

Id: 1/4 Title: KlokTHREEjr Controller

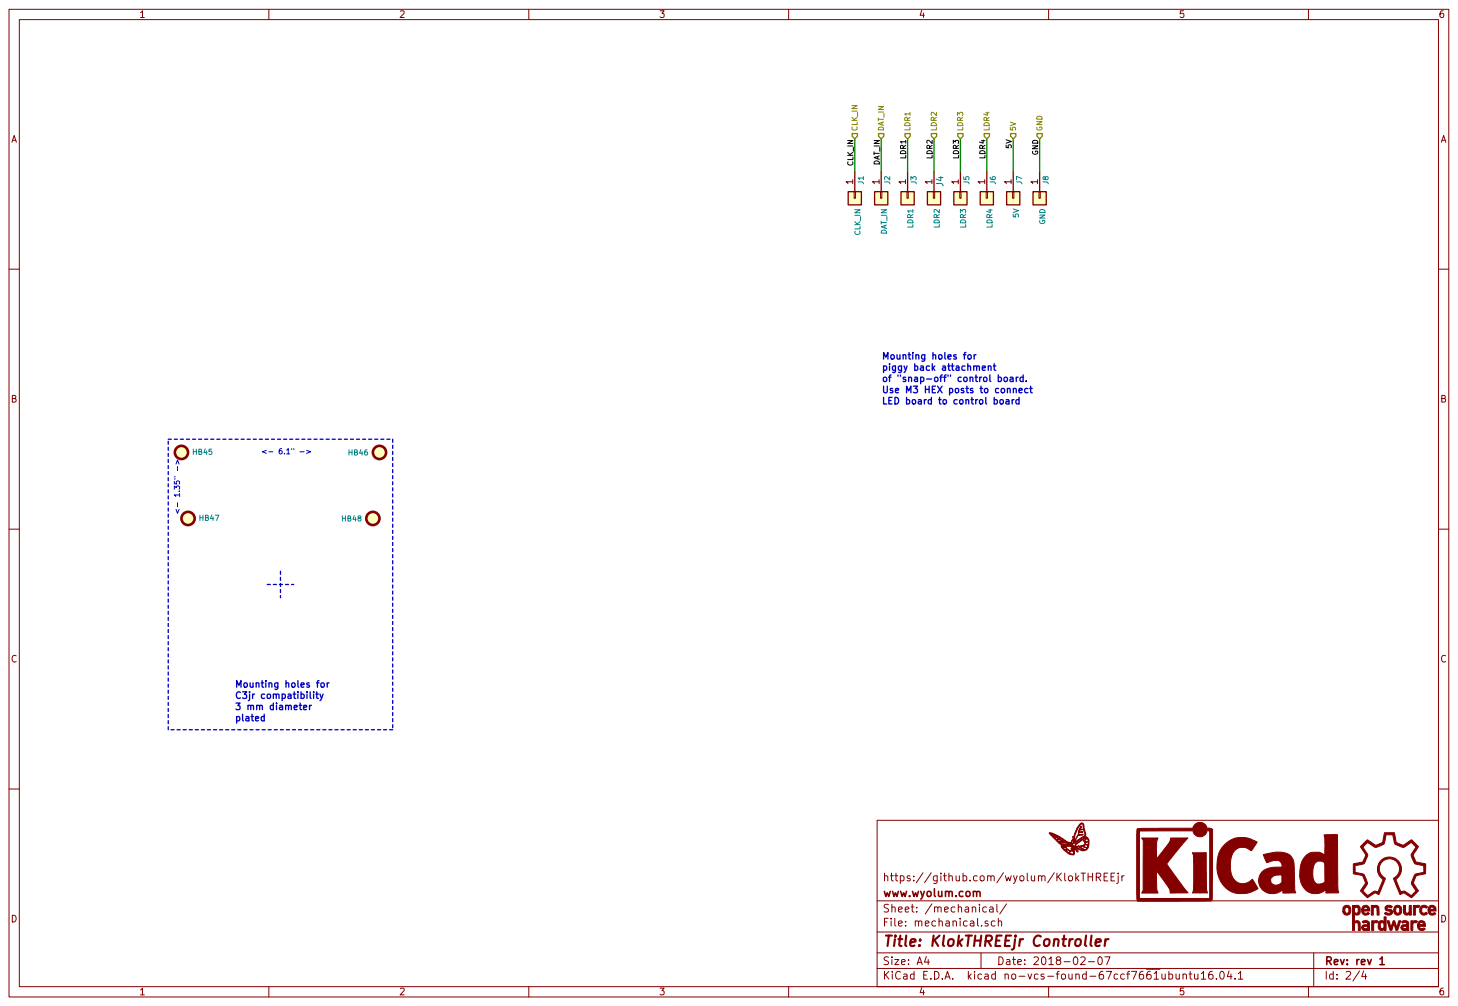
[picture p107: page 2]

Mounting holes for
piggy back attachment
of "snap-off" control board.

https://github.com/wyolum/KlokTHREEjr
Id: 2/4 Title: KlokTHREEjr Controller File: mechanical.sch Sheet: /mechanical/ www.wyolum.com


https://github.com/wyolum/KlokTHREEjr
www.wyolum.com
Sheet: /rtc_ds3231/
File: rtc_ds3231.sch
Id: 3/4 Title: KlokTHREEjr Controller

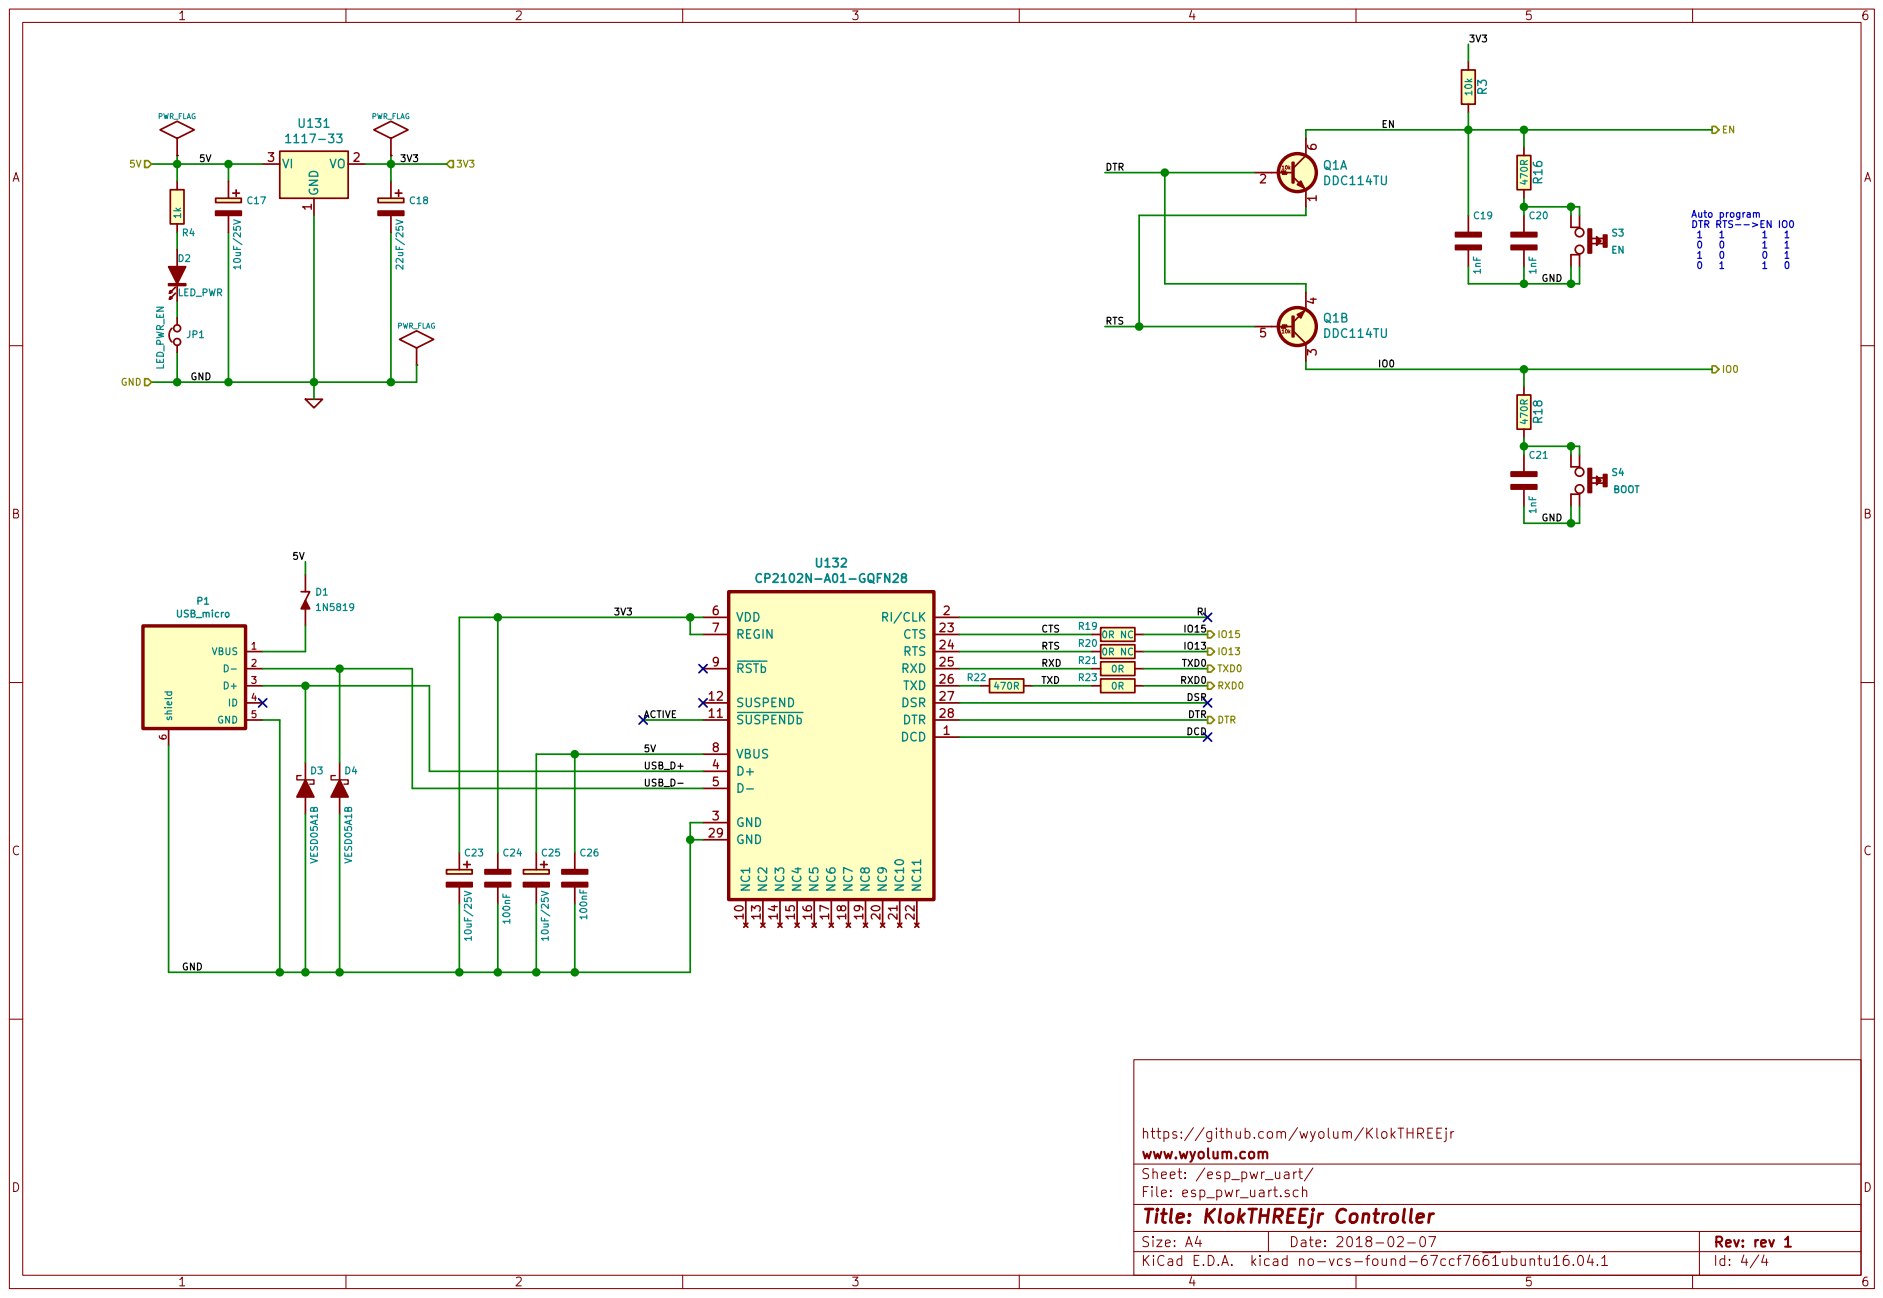
[picture p108: page 4]

https://github.com/wyolum/KlokTHREEjr
www.wyolum.com
Sheet: /esp_pwr_uart/
File: esp_pwr_uart.sch
Id: 4/4 Title: KlokTHREEjr Controller
