wyolum/KlokTHREEjr/k3jr_controller_kicad_v1/k3jr_controller_pdf/v1/k3jr_controller_v1-F.SilkS.pdf

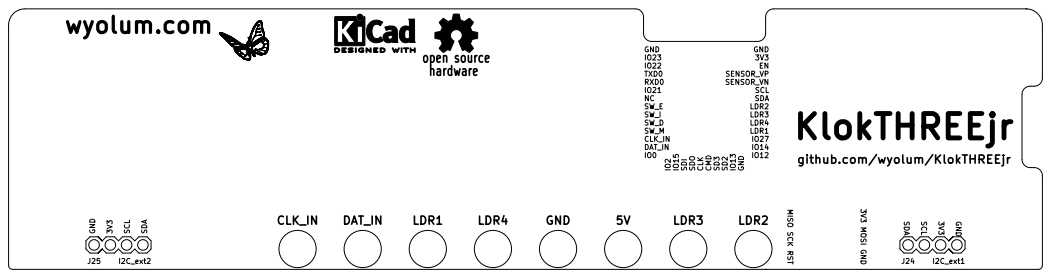
[picture p110: page 1]

File: k3jr_controller.kicad_pcb Sheet: www.wyolum.com
