wyolum/KlokTHREEjr/k3jr_controller_kicad_v1/k3jr_controller_pdf/v1/k3jr_controller_v1-Dwgs.User.pdf

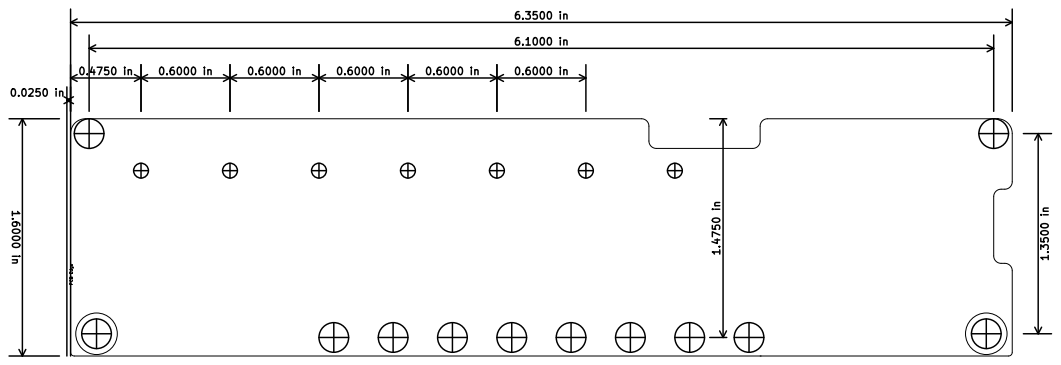
[picture p112: page 1]

https://github.com/wyolum/KlokTHREEjr 1.4750 in

File: k3jr_controller.kicad_pcb Sheet: www.wyolum.com
