wyolum/KlokTHREEjr/k3jr_controller_kicad_v1/k3jr_controller_pdf/v1/k3jr_controller_v1-F.Cu.pdf

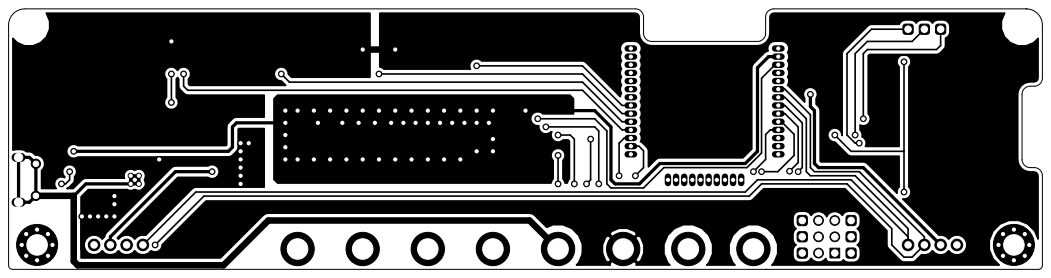
[picture p113: page 1]

https://github.com/wyolum/KlokTHREEjr
File: k3jr_controller.kicad_pcb Sheet: www.wyolum.com
