wyolum/KlokTHREEjr/fabricate/DesKLOK_case_anool/laser_cut_ver1/desk_klok_FlexBox.pdf

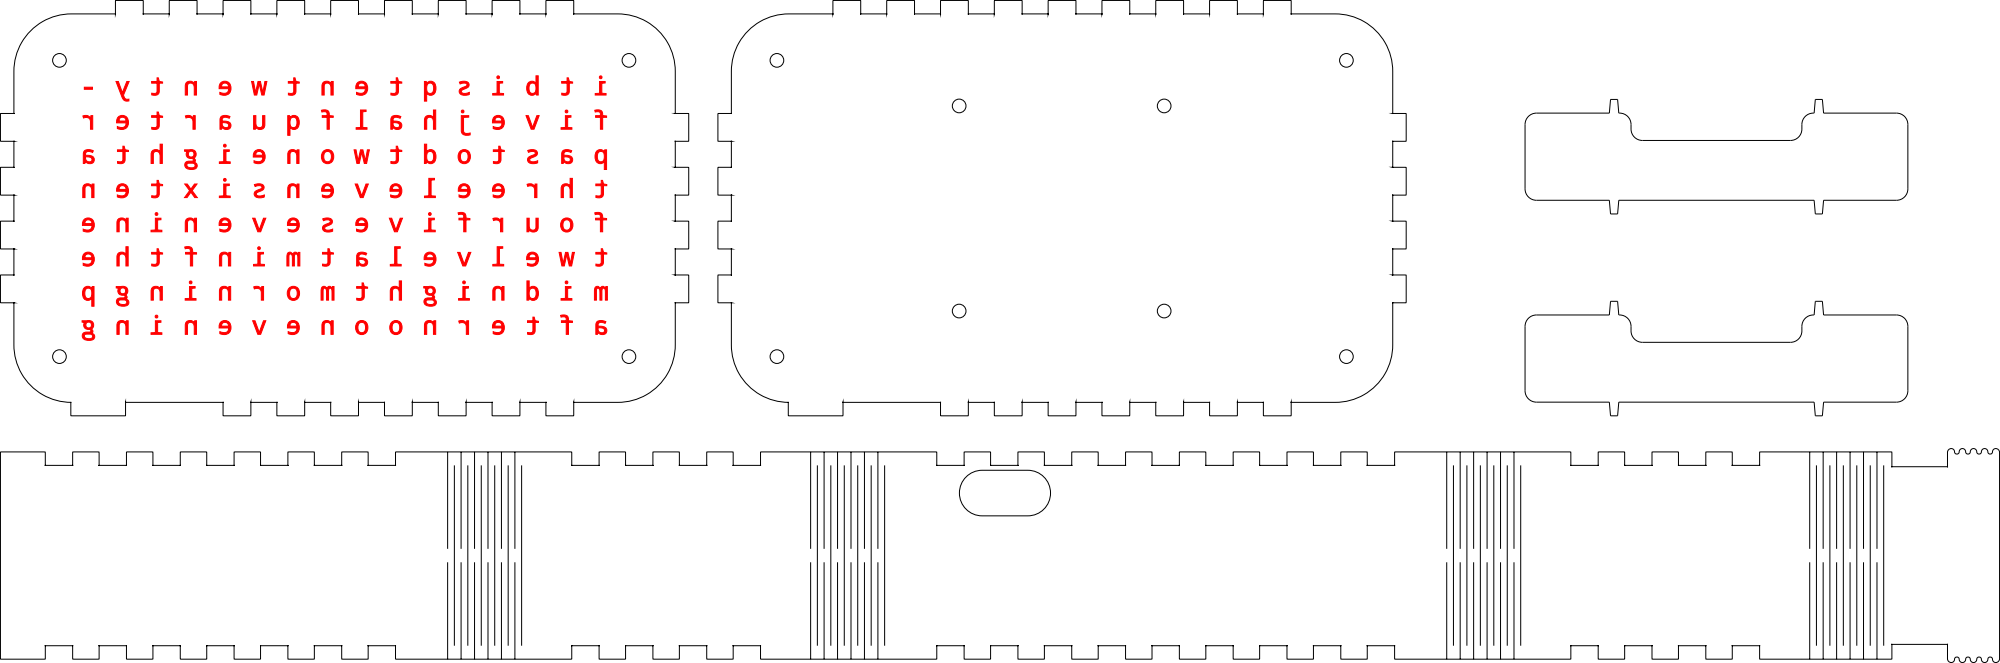
[picture p117: page 1]
