wyolum/KlokTHREEjr/fabricate/DesKLOK_case_anool/laser_cut_ver1/desk_klok_FlexBox_back.pdf

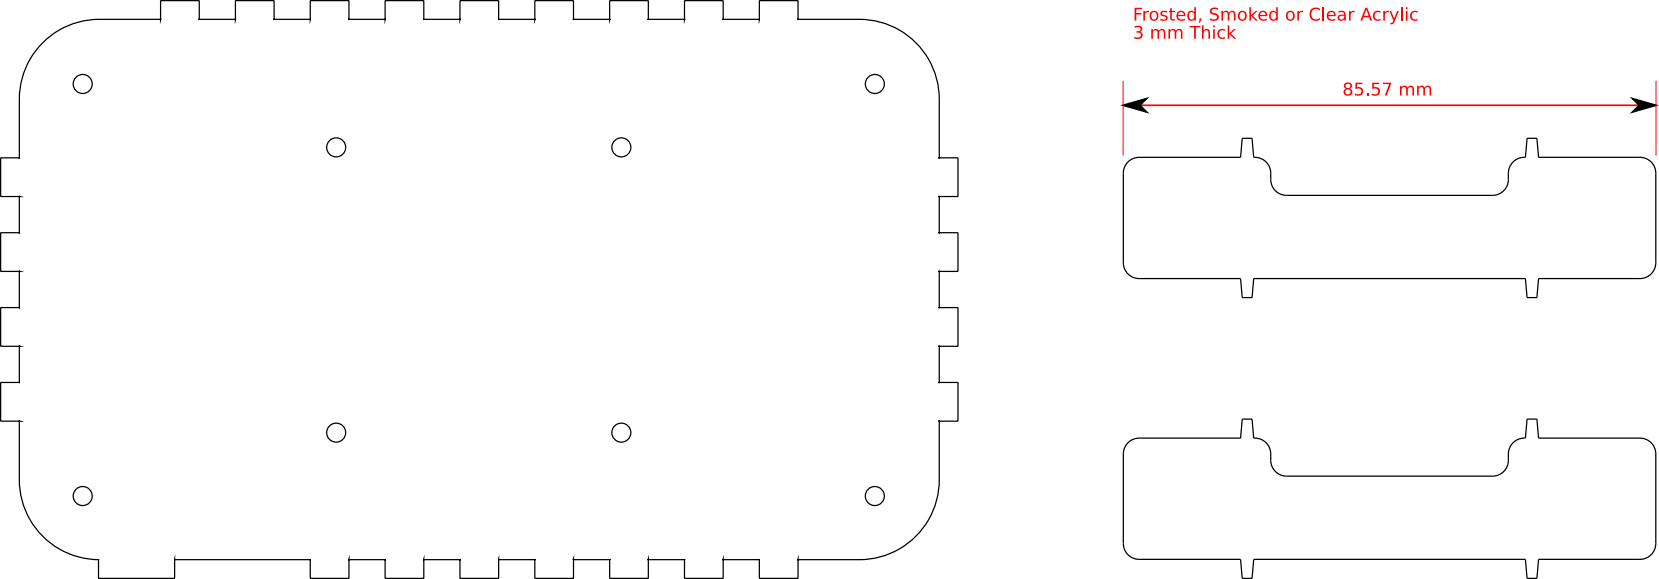
[picture p118: page 1]
