wyolum/KlokTHREEjr/fabricate/DesKLOK_case_anool/laser_cut_ver1/desk_klok_FlexBox_front.pdf

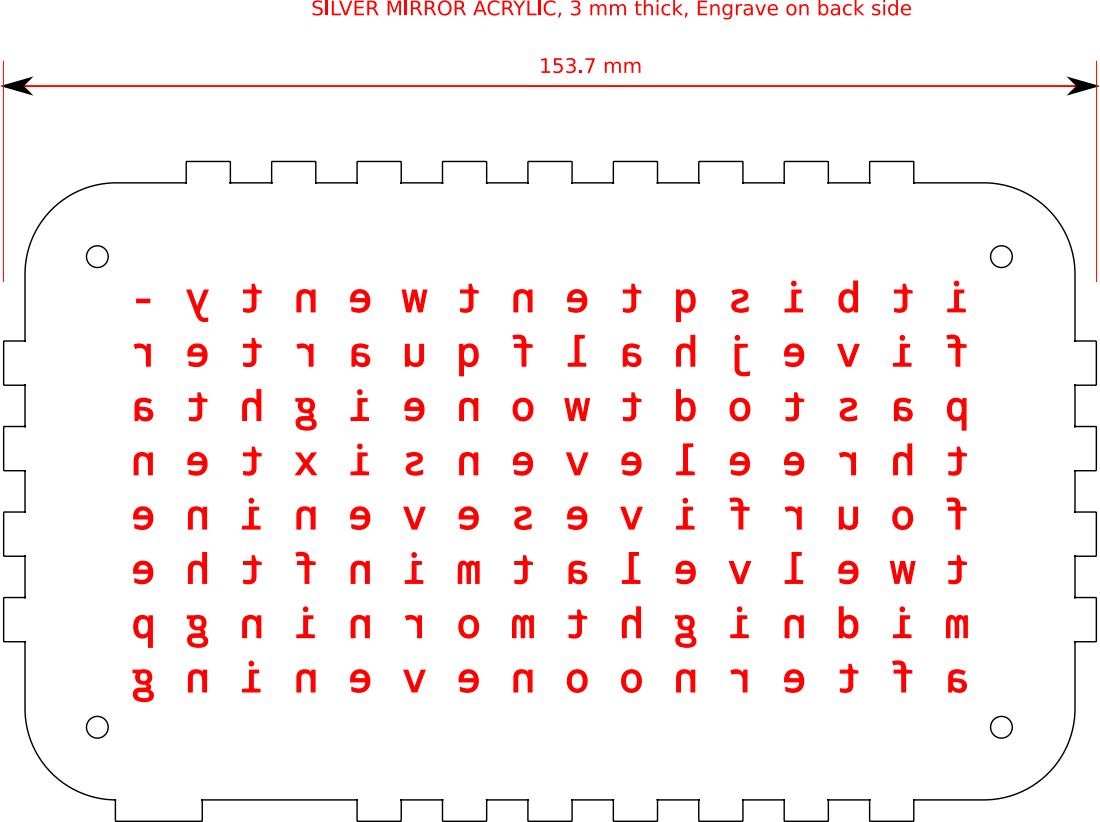
[picture p119: page 1]
