wyolum/KlokTHREEjr/fabricate/DesKLOK_case_anool/laser_cut_ver1/desk_klok_FlexBox_side.pdf

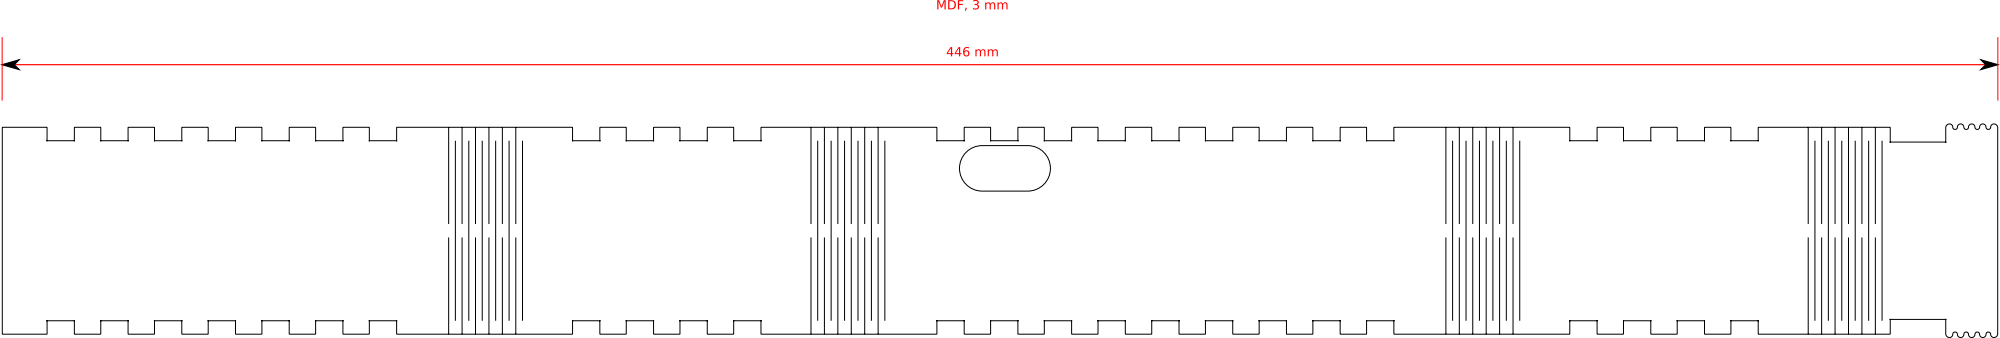
[picture p120: page 1]
